rasusmilch/PT100_Mesh_Datalogger/documents/adafruit_products_framschem.png

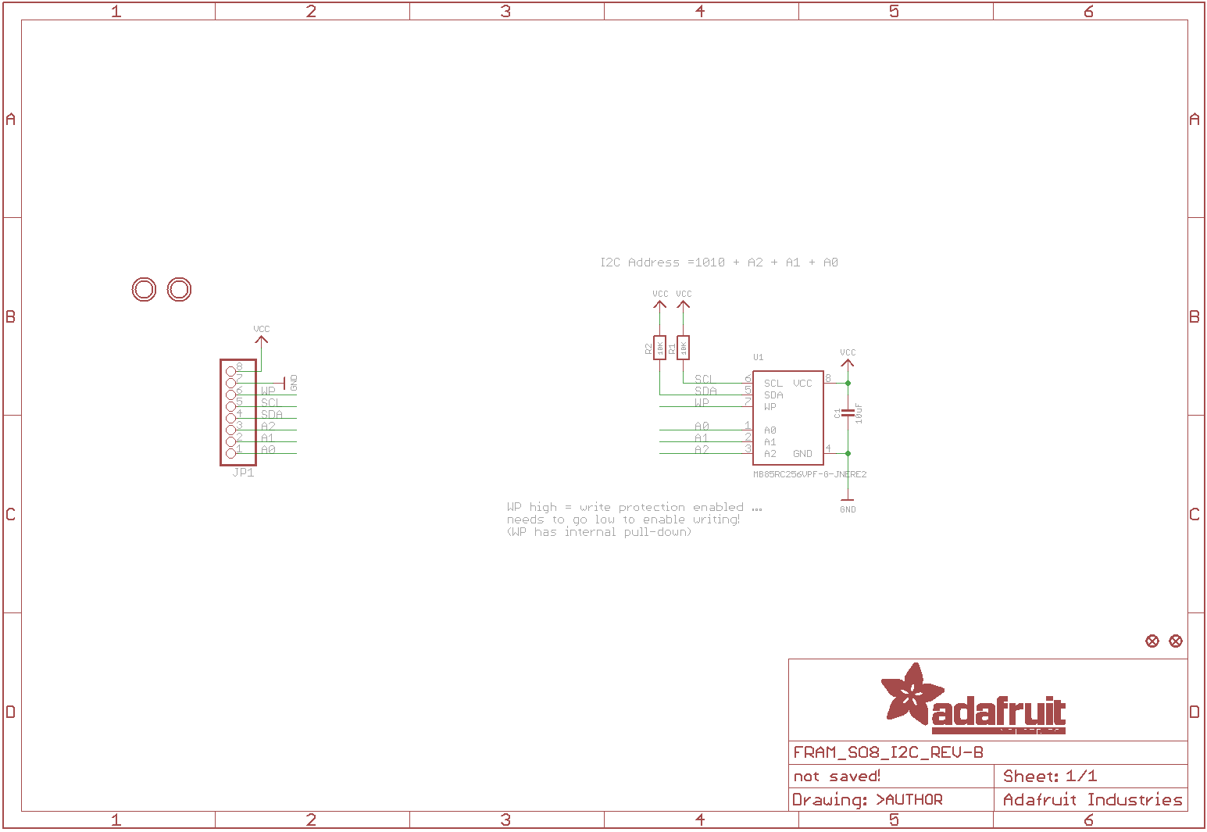
documents/adafruit_products_framschem.png
