rasusmilch/PT100_Mesh_Datalogger/documents/Figure_2.png

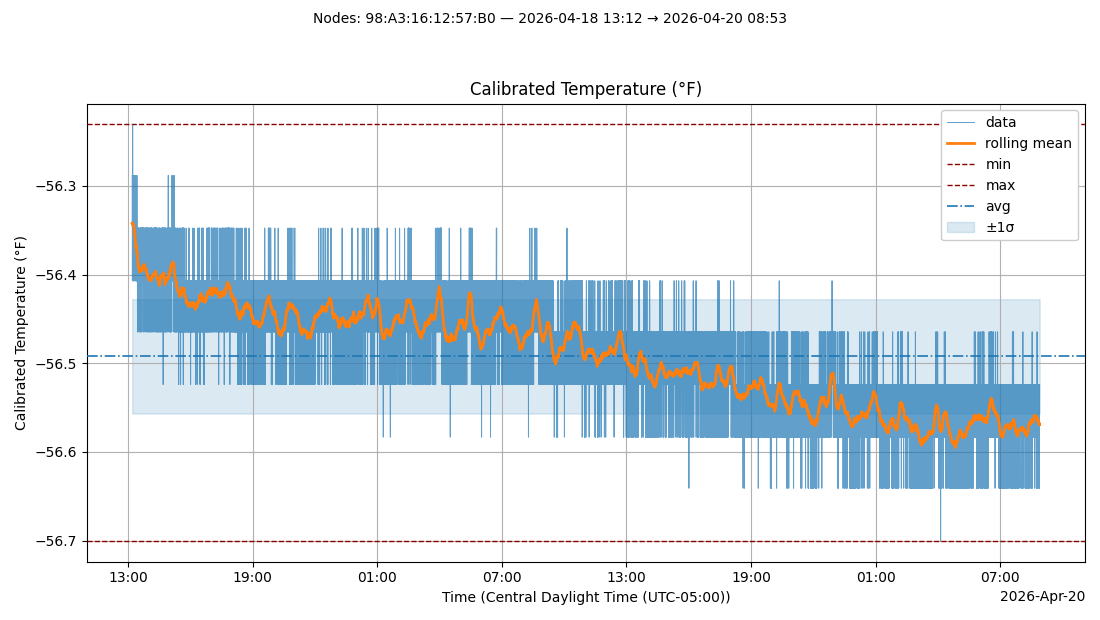
documents/Figure_2.png
