rasusmilch/PT100_Mesh_Datalogger/documents/MAX31865.png

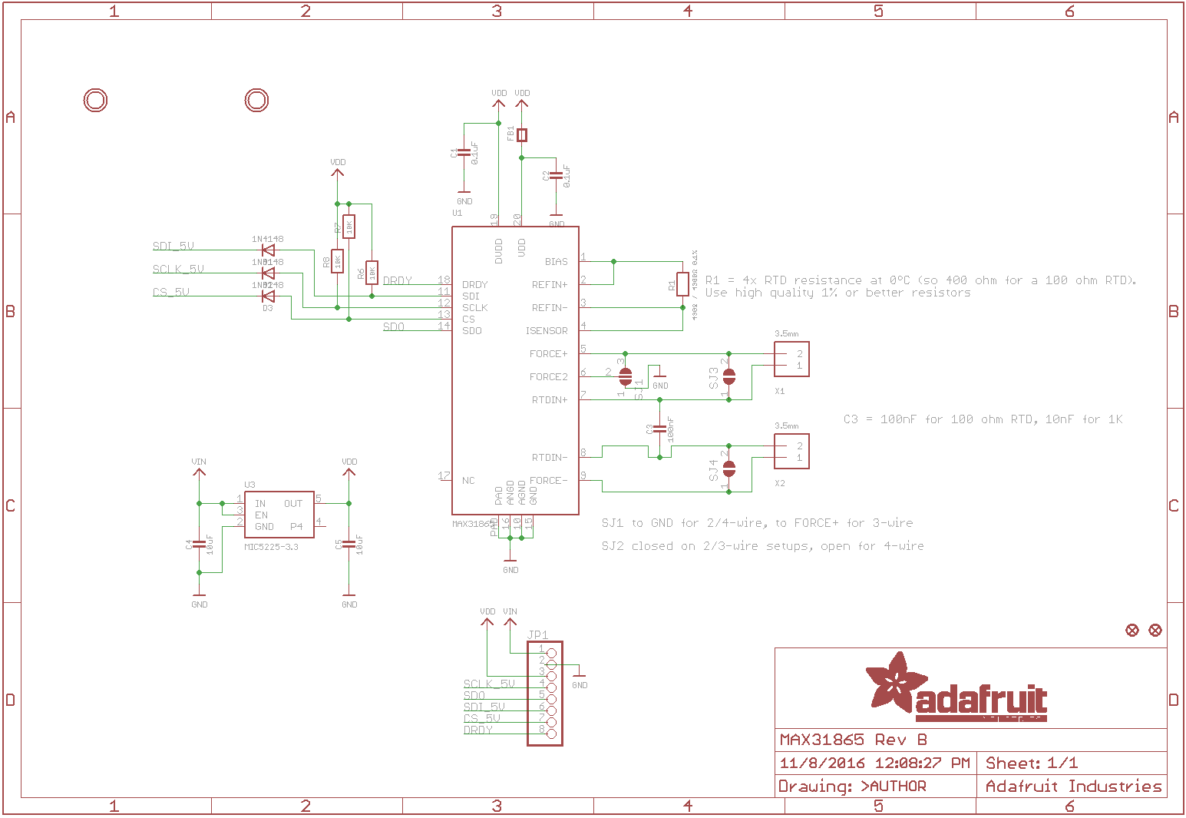
documents/MAX31865.png
