rasusmilch/PT100_Mesh_Datalogger/KiCad/PT100_Datalogger/Documentation/PT100_Datalogger_REV_A.pdf

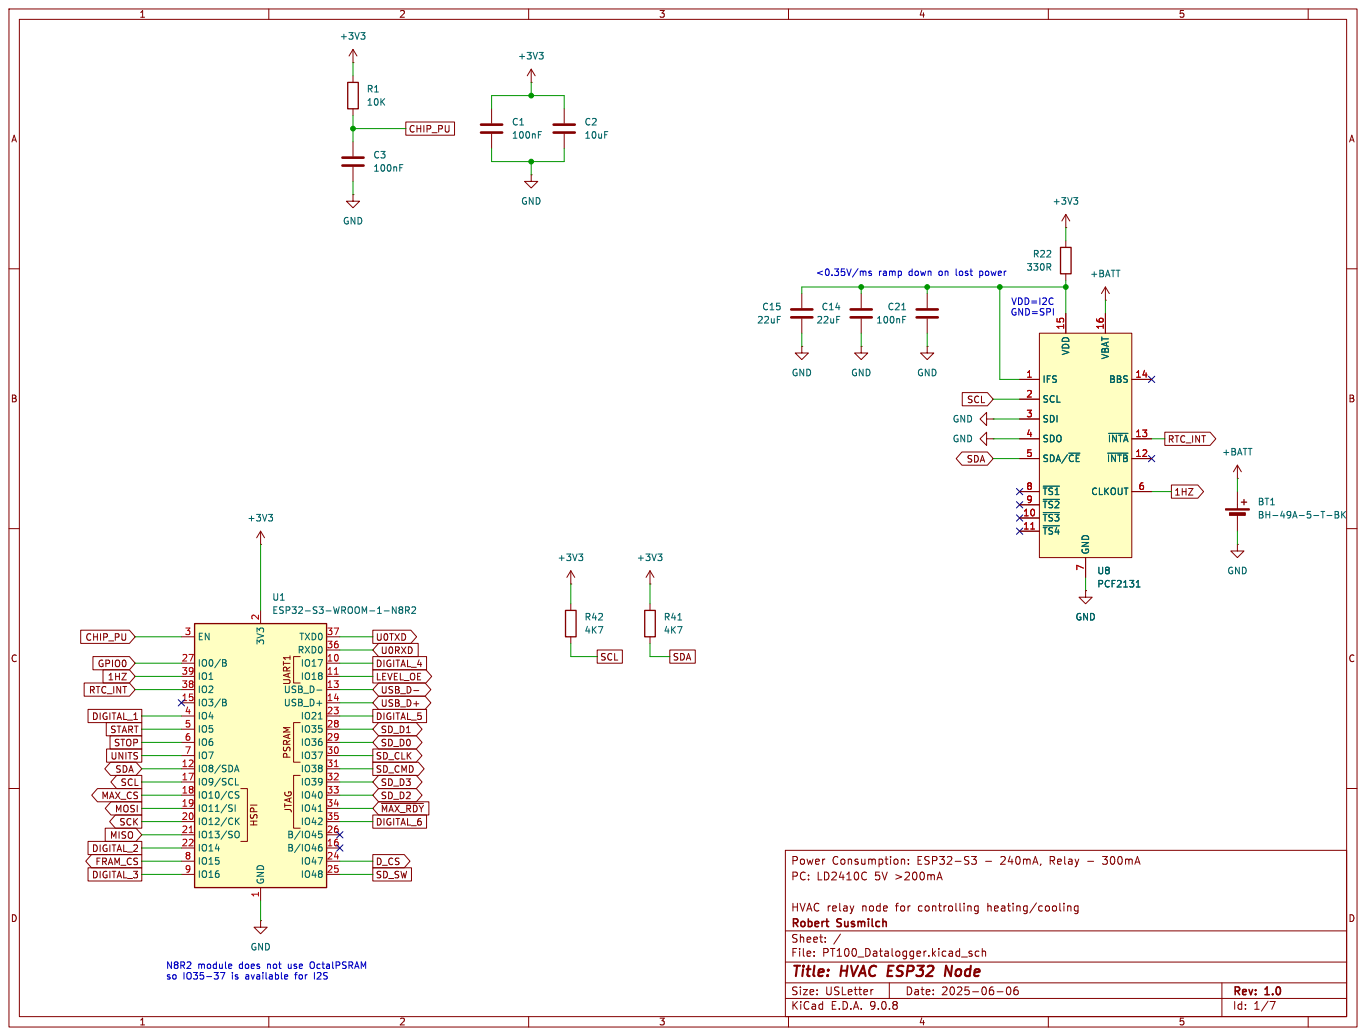
[picture p20: page 1]

7 VBAT 16 BBS 14 ~{INTA}13 ~{INTB}12 CLKOUT 6 U8PCF2131 C14

7 VBAT 16 BBS 14 ~{INTA}13 ~{INTB}12 CLKOUT 6 GND

N8R2 module does not use OctalPSRAM

Id: 1/7 Title: HVAC ESP32 Node

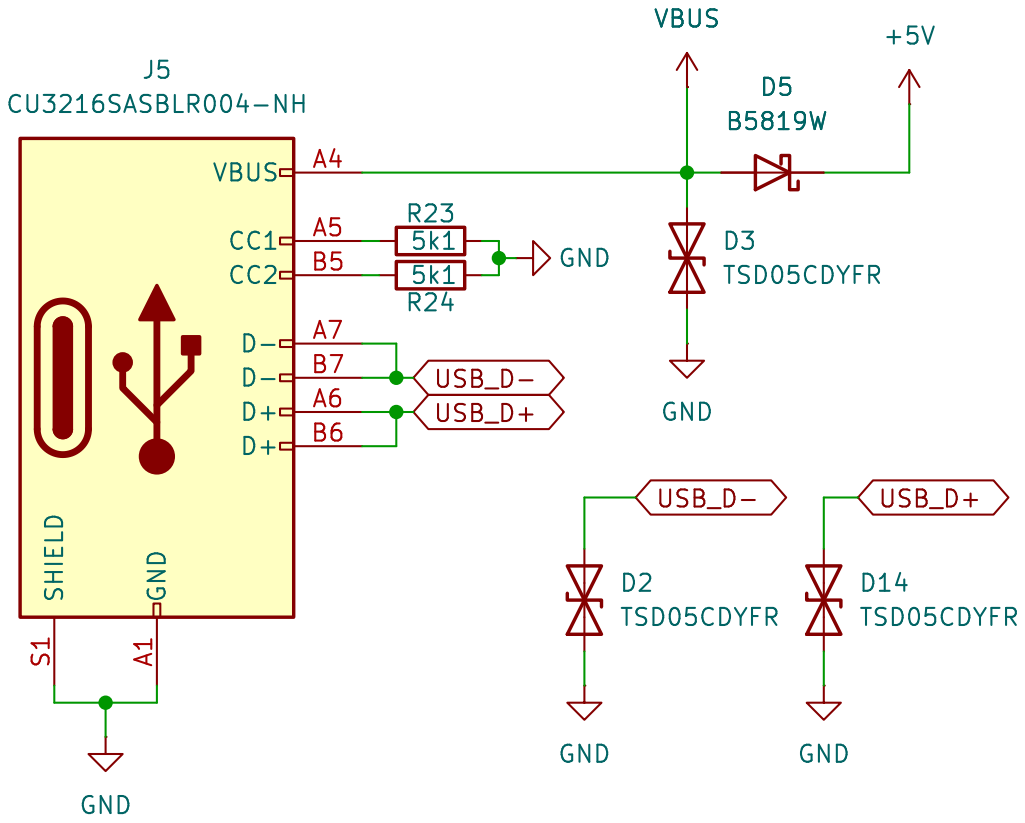
[picture p21: page 2]

Id: 2/7 Title: HVAC ESP32 Node

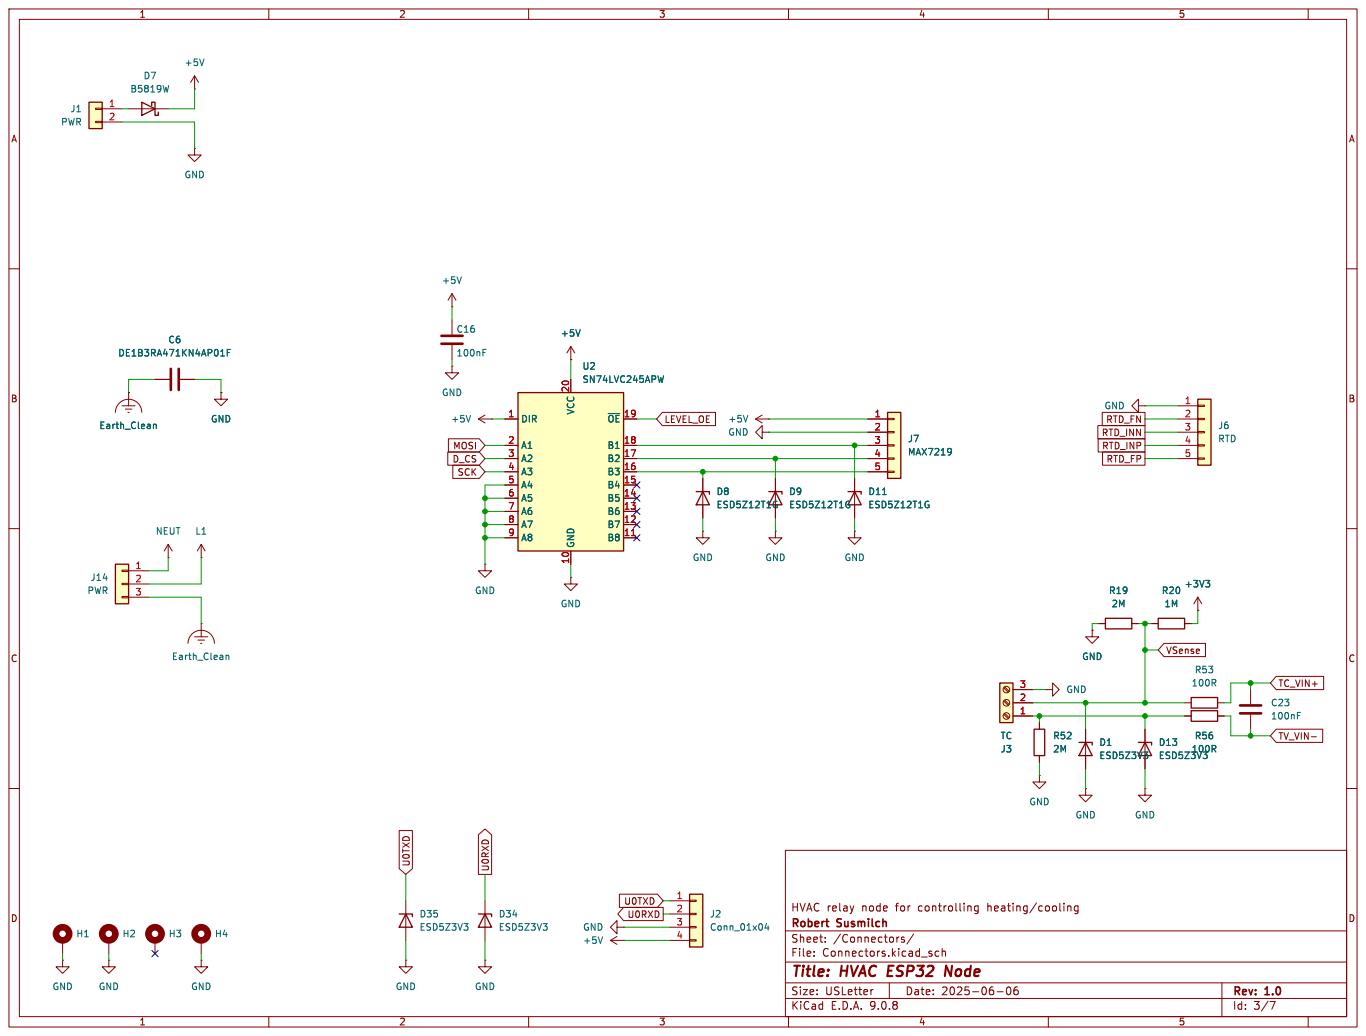
[picture p22: page 3]

Id: 3/7 Title: HVAC ESP32 Node

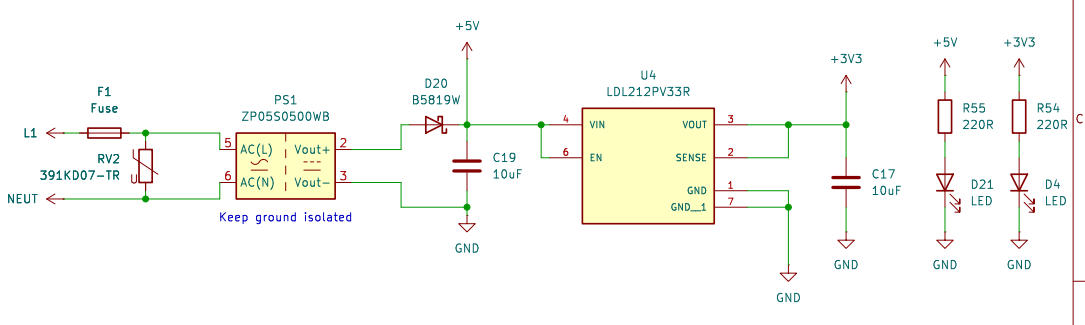
[picture p23: page 4]

Id: 5/7 Title: HVAC ESP32 Node

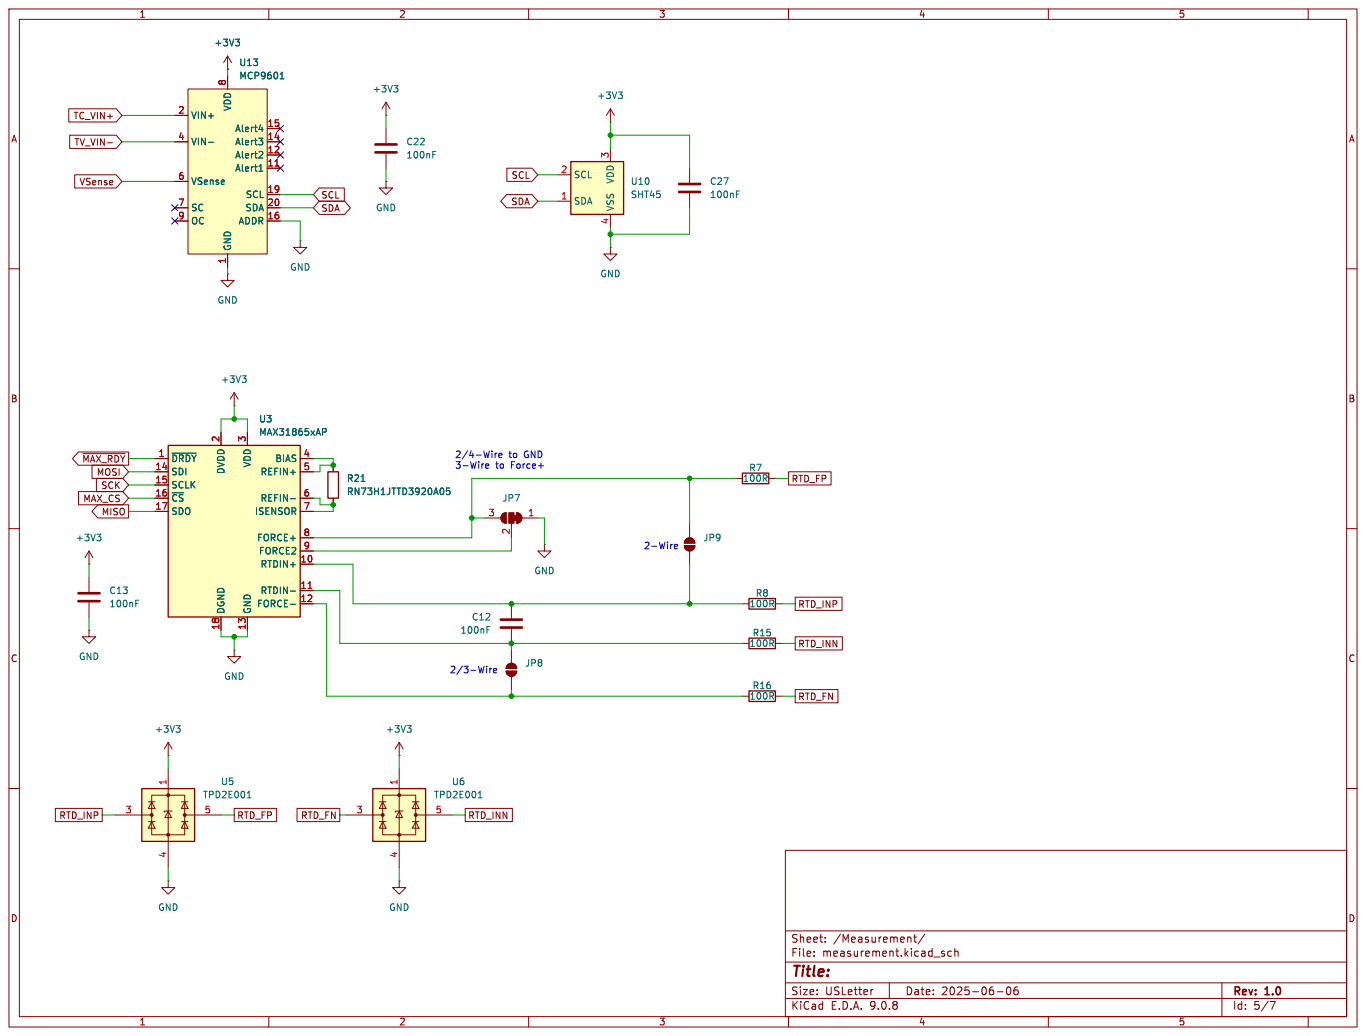
[picture p24: page 5]

3 GND 13 BIAS 4 REFIN+ 5 REFIN- 6

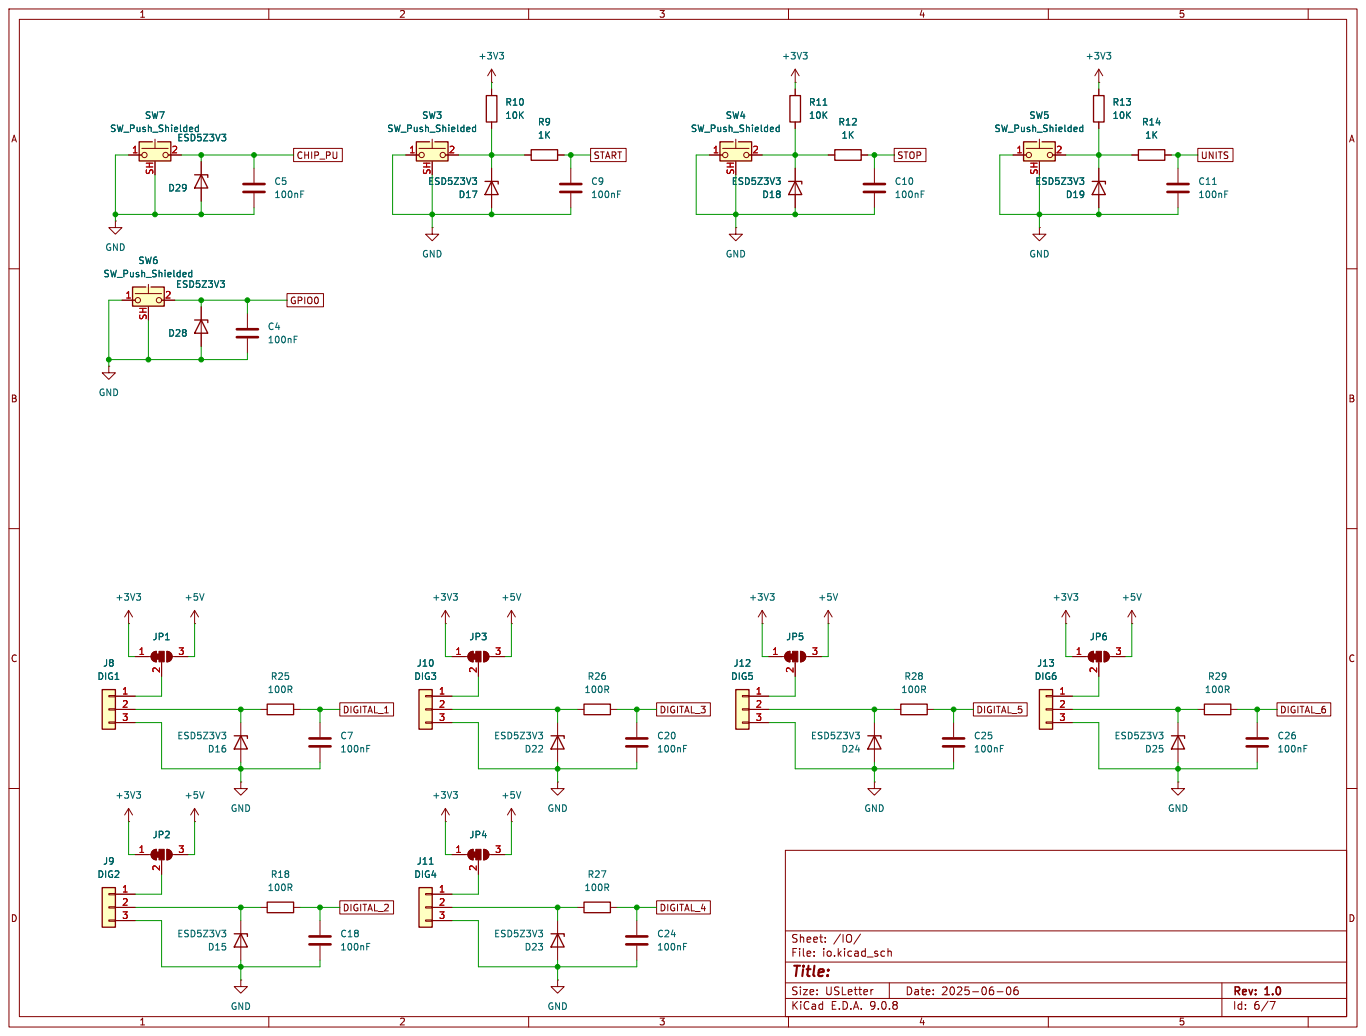
[picture p25: page 6]

Id: 6/7 Title: File: io.kicad_sch Sheet: /IO/ C24

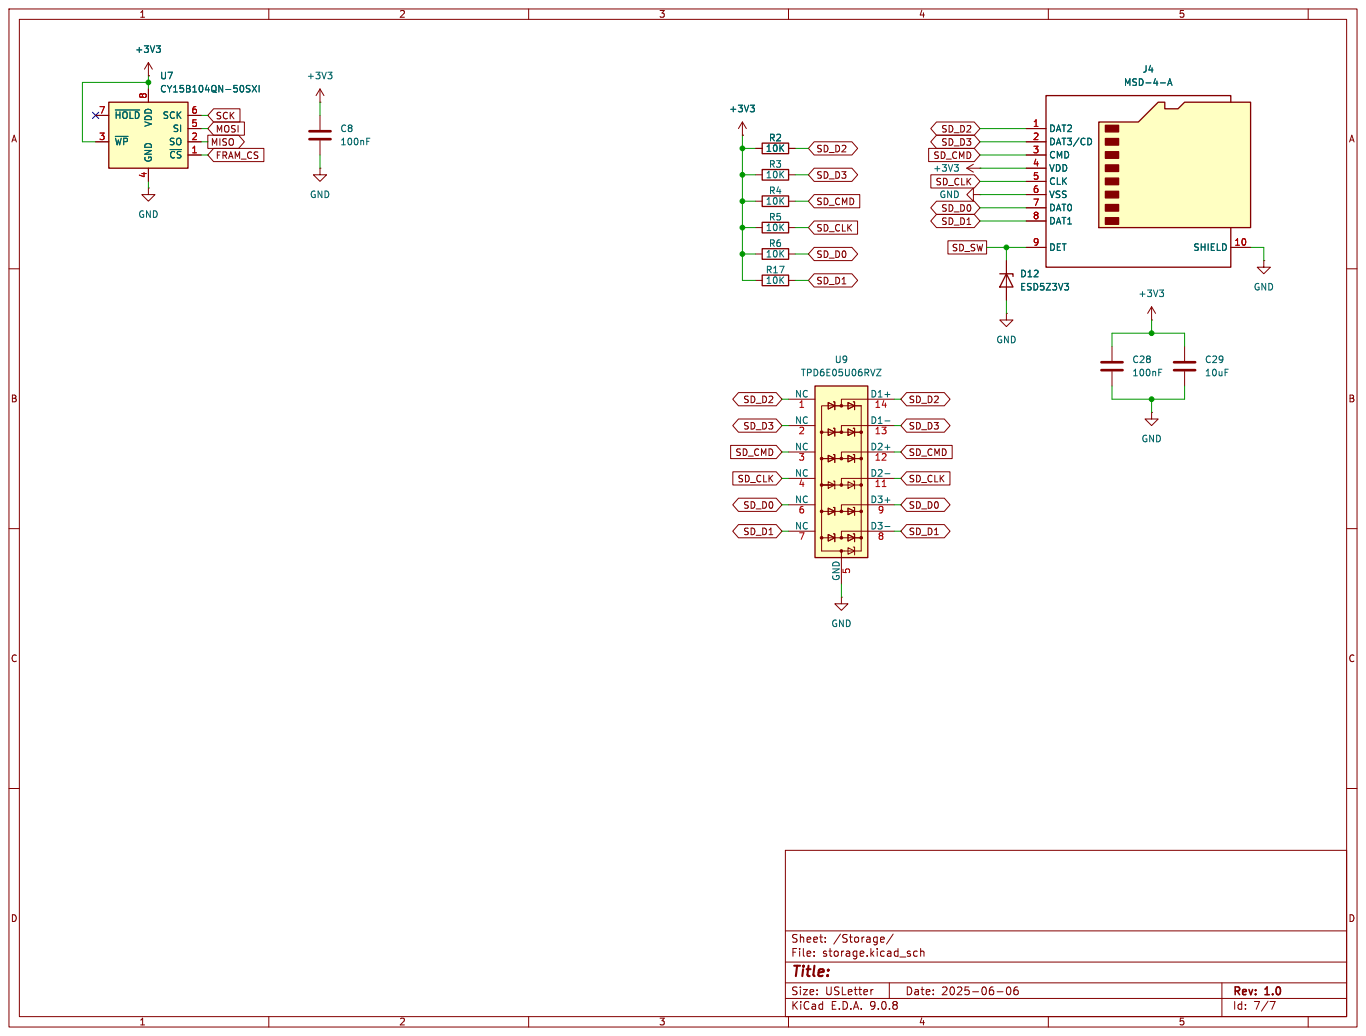
[picture p26: page 7]

4 SCK 6 SI 5 SO 2 ~{CS}1 U7 CY15B104QN-50SXI GND

4 SCK 6 SI 5 SO 2 ~{CS}1 R2

Id: 7/7 Title: File: storage.kicad_sch Sheet: /Storage/
