rasusmilch/PT100_Mesh_Datalogger/main/console_commands.c

#include "console_commands.h"

#include "freertos/FreeRTOS.h"
#include "freertos/semphr.h"
#include "freertos/task.h"

#include <ctype.h>
#include <dirent.h>
#include <errno.h>
#include <inttypes.h>
#include <limits.h>
#include <math.h>
#include <stdio.h>
#include <stdlib.h>
#include <string.h>
#include <sys/stat.h>
#include <time.h>

#include "app_net_config.h"
#include "app_settings.h"
#include "argtable3/argtable3.h"
#include "boot_mode.h"
#include "calibration.h"
#include "diagnostics/diag_fram.h"
#include "diagnostics/diag_mesh.h"
#include "diagnostics/diag_rtc.h"
#include "diagnostics/diag_rtd.h"
#include "diagnostics/diag_sd.h"
#include "diagnostics/diag_storage.h"
#include "diagnostics/diag_wifi.h"
#include "display_attention.h"
#include "driver/uart.h"
#include "driver/uart_vfs.h"
#include "esp_console.h"
#include "esp_heap_caps.h"
#include "esp_memory_utils.h"
#include "esp_netif.h"
#include "esp_timer.h"
#include "esp_wifi.h"
#include "fram_error_log.h"
#include "net_supervisor.h"
#include "runtime_health.h"
#include "time_civil.h"

#if CONFIG_ESP_CONSOLE_USB_SERIAL_JTAG
#include "driver/usb_serial_jtag.h"
#include "driver/usb_serial_jtag_vfs.h"
#include <fcntl.h>
#include <unistd.h>
#endif

#include "console_alerts.h"
#include "console_help.h"
#include "console_registry.h"
#include "esp_log.h"
#include "esp_system.h"
#include "i2c_bus.h"
#include "max31865_reader.h"
#include "mem_guard.h"
#include "runtime_manager.h"
#include "runtime_markers.h"
#include "sd_card_detect.h"
#include "sdkconfig.h"
#include "time_sync.h"
#include "units_gpio.h"
#include "wifi_credentials.h"
#include "wifi_manager.h"
#include "wifi_service.h"

static const char* kTag = "console";
static const TickType_t kConsoleFramLogLockTimeoutTicks = pdMS_TO_TICKS(2000);
static const int32_t kFlushTimeoutDefaultMs = 15000;
static const size_t kConsoleMaxCmdlineLength = 1024;
static const int kConsoleTransportRxBufferSize = 2048;
static const int kConsoleTransportTxBufferSize = 2048;
static const double kDefaultCaptureDriftLimitCPerMin = 0.020;
static char* s_console_cmdline_buffer = NULL;
static char* s_console_cmdline_snapshot = NULL;
static bool s_console_cmdline_buffer_in_psram = false;
static bool s_console_cmdline_snapshot_in_psram = false;
static void
FormatFileTime(const time_t* timestamp, char* buffer, size_t buffer_size);
static void
FormatUtcEpochIso8601(int64_t epoch_utc, char* buffer, size_t buffer_size);
static void
FormatLocalEpochIso8601(int64_t epoch_utc, char* buffer, size_t buffer_size);
static void
FormatErrlogFlags(uint16_t flags, char* buffer, size_t buffer_size);
static bool
CalConsoleOpIsActive(void);
static esp_err_t
CalConsoleOpStartLive(uint32_t every_ms,
                      int seconds,
                      int live_output_mode,
                      bool drift_notify_armed,
                      double drift_notify_threshold_c_per_min);
static esp_err_t
CalConsoleOpStartCapture(double actual_temp_c,
                         double stable_stddev_c,
                         bool drift_limit_enabled,
                         double drift_limit_c_per_min,
                         calibration_drift_limit_source_t drift_limit_source,
                         int min_seconds,
                         int timeout_seconds);
static void
CalConsoleOpRequestCancel(void);
static void
CalConsoleOpTask(void* task_arg);
static void
PrintCalWindowLine_(const char* prefix,
                    const char* timestamp_utc,
                    size_t sample_count,
                    int32_t last_raw_mC,
                    int32_t last_raw_mOhm,
                    int32_t mean_raw_mC,
                    int32_t stddev_mC,
                    double drift_c_per_min,
                    double delta_c,
                    bool drift_target_enabled,
                    const char* drift_eta_to_target_text);
static void
PrintCalWindowCalibratedLine_(const char* timestamp_utc,
                              size_t sample_count,
                              int32_t last_raw_mOhm,
                              int32_t mean_raw_mOhm,
                              int32_t stddev_mOhm,
                              double calibrated_temp_c,
                              double mean_calibrated_temp_c,
                              double stddev_calibrated_temp_c,
                              double drift_c_per_min,
                              double delta_c,
                              uint8_t fault_status);
static bool
ParseCalLiveArguments_(int argc,
                       char** argv,
                       const char* usage,
                       int* every_ms_out,
                       int* seconds_out,
                       bool* drift_notify_armed_out,
                       double* drift_notify_threshold_out);
static void
PrintCalLiveUsage_(const char* command_name);
static bool
FormatCalLiveTimestampNow_(char* buffer, size_t buffer_size);
static bool
EvaluateCalibratedTemperature_(double raw_temp_c,
                               double raw_resistance_ohm,
                               double* calibrated_temp_c_out);
static double
ConsoleResistanceToTemperatureFitCallback_(double resistance_ohm,
                                           void* context);
static void
PrintCalibrationFitLabelAndValueOrNa_(const char* label,
                                      bool available,
                                      double value);
static const char*
CalibrationFitDomainDisplayString_(calibration_domain_t fit_domain);
static const char*
CalibrationFitCorrectionLabel_(calibration_domain_t fit_domain);
static const char*
CalibrationFitCorrectionColumnHeader_(calibration_domain_t fit_domain);
static const char*
CalibrationFitDegreeLabel_(calibration_fit_mode_t fit_mode);
static void
PrintCalibrationFitValueOrNa_(const char* label,
                              bool available,
                              double value,
                              const char* unit_suffix);
static void
PrintCalibrationFitDiagnosticsBlock_(
  const calibration_fit_diagnostics_t* diagnostics);
static void
PrintCalibrationModelFitTable_(const calibration_fit_report_t* fit_report);
static void
PrintCalibrationModelFitReport_(const app_settings_t* settings);
static bool
RefreshCalibratedWindowTempStatsCache_(size_t sample_count,
                                       uint32_t window_generation,
                                       int32_t last_raw_mC,
                                       int32_t last_raw_mOhm,
                                       int32_t mean_raw_mC,
                                       int32_t mean_raw_mOhm);
static bool
CalHistoryEnsureStorage_(void);
static void
CalLogMemorySnapshot_(const char* stage, const char* mode_label);
static void
CalTrackLiveLowWatermark_(void);
static void
CalTrackLiveStackAndTempUsage_(size_t temp_bytes);
static void
CalLogLiveRetainedResources_(const char* mode_label);
/**
 * @brief Queue a one-shot cal live drift-ready ntfy message via alert queue.
 * @param drift_c_per_min Current gated drift value (C/min).
 * @param threshold_c_per_min Armed absolute drift threshold (C/min).
 * @param sustained_seconds Required sustained-under-threshold duration.
 * @return true when an ntfy job was queued successfully.
 */
static bool
QueueCalLiveDriftReadyNtfy_(double drift_c_per_min,
                            double threshold_c_per_min,
                            uint32_t sustained_seconds);
static void
PrintCalCaptureWindowLine_(double elapsed_s,
                           size_t sample_count,
                           int32_t last_raw_mC,
                           int32_t last_raw_mOhm,
                           int32_t mean_raw_mC,
                           double stddev_c,
                           double drift_c_per_min,
                           double delta_c,
                           double stable_elapsed_s,
                           int min_seconds,
                           double stable_stddev_c,
                           bool drift_limit_enabled,
                           double drift_limit_c_per_min,
                           calibration_drift_limit_source_t drift_limit_source,
                           double actual_temp_c);
static const char*
DriftLimitSourceToString_(calibration_drift_limit_source_t source);
static const char*
FindOptionValue_(int argc, char** argv, const char* name);
static bool
OptionPresent_(int argc, char** argv, const char* name);
static bool
ParseOptionInt_(int argc, char** argv, const char* name, int* value_out);
static bool
ParseOptionDouble_(int argc, char** argv, const char* name, double* value_out);
static bool
ParseTempC_(const char* text, double* value_out);
static bool
ParseCalAddPositionalArgs_(int argc,
                           char** argv,
                           double* raw_c_out,
                           double* actual_c_out);
static bool
ParseCalImportArgs_(int argc,
                    char** argv,
                    double* raw_ohm_out,
                    double* actual_c_out,
                    bool* raw_c_supplied_out,
                    double* raw_c_out,
                    bool* stddev_c_supplied_out,
                    double* stddev_c_out);
static bool
ParseCalibrationImportStatusLineSpan_(const char* line_start,
                                      size_t line_len,
                                      calibration_point_t* point_out,
                                      size_t* token_count_out);
static bool
ParseCalibrationImportStatusTokens_(int argc,
                                    char** argv,
                                    int start_index,
                                    calibration_point_t* point_out,
                                    size_t* token_count_out);
static bool
CalibrationImportPayloadFromConsoleLine_(const char* action,
                                         const char** payload_start_out,
                                         size_t* payload_len_out,
                                         bool* payload_quoted_out,
                                         bool* unterminated_quote_out);
static bool
NextCalibrationImportTokenSpan_(const char* line_start,
                                size_t line_len,
                                size_t* cursor_inout,
                                const char** token_start_out,
                                size_t* token_len_out);
static bool
ParseCalibrationImportDoubleSpan_(const char* value_start,
                                  size_t value_len,
                                  double* parsed_out);
static bool
ParseCalibrationImportDriftLimitSourceSpan_(
  const char* value_start,
  size_t value_len,
  calibration_drift_limit_source_t* source_out);
static bool
CalibrationImportKeyEquals_(const char* key_start,
                            size_t key_len,
                            const char* expected);
static int
FindCalibrationPointIndexByActualMc_(const app_settings_t* settings,
                                     int32_t actual_mC);
static esp_err_t
SaveCalibrationPointsAndDomain_(app_settings_t* settings);
static esp_err_t
DeleteCalibrationPointByDisplayIndex_(app_settings_t* settings,
                                      size_t display_index,
                                      calibration_point_t* deleted_point_out);
static bool
JoinArgsWithSpaces(int argc,
                   char** argv,
                   int start_index,
                   char* out,
                   size_t out_size);
static int
CalTopicHelp(const char* topic);
static int
SdTopicHelp(const char* topic);
static void
PrintModeHelpBody(void);
static void
PrintNetHelpBody(void);
static int
ModeTopicHelp(const char* topic);
/**
 * @brief Compute effective sensor poll period shown by console diagnostics.
 * @param settings Current settings snapshot.
 * @return Effective poll period in milliseconds.
 */
static uint32_t
ConsoleEffectiveSensorPollPeriodMs(const app_settings_t* settings);
static bool
ConsoleInputTooLongOrUnterminatedQuote_(const char* line,
                                        size_t max_cmdline_length);
static bool
ConsoleCmdlineBufferInit_(size_t max_cmdline_length);
static bool
ConsoleCmdlineSnapshotCapture_(const char* line, size_t max_cmdline_length);
static char*
ConsoleReadLine_(const char* prompt);

/**
 * @brief Print combined calibration status including window stats, points, and
 * schedule metadata.
 * @param settings Active settings snapshot.
 * @param state Runtime state for time stability / due-check flags.
 */
static void
PrintCalibrationStatusUnified(const app_settings_t* settings,
                              const runtime_state_t* state);
/**
 * @brief Print human-readable calibration equation and named coefficients.
 * @param model Active stored calibration model.
 */
static void
PrintCalibrationEquationBlock_(const calibration_model_t* model);
/**
 * @brief Print polynomial coefficients using symbolic names that map from
 * highest-order term down to constant term.
 * @param coefficients Stored polynomial coefficients in constant-first order.
 * @param degree Polynomial degree to print.
 */
static void
PrintNamedPolynomialCoefficients_(const double* coefficients, uint8_t degree);
/**
 * @brief Summary values for rendering one calibration point in status/report
 * output.
 */
typedef struct
{
  bool ideal_ref_res_available;
  bool captured_raw_res_available;
  bool captured_raw_temp_avg_available;
  bool captured_raw_temp_stddev_available;
  bool captured_raw_res_stddev_available;
  bool captured_drift_available;
  bool captured_delta_available;
  bool drift_limit_available;
  bool captured_window_available;
  bool captured_ema_alpha_available;
  bool residual_res_available;
  bool residual_temp_available;
  double ideal_ref_res_ohm;
  double captured_raw_res_avg_ohm;
  double captured_raw_temp_avg_c;
  double captured_raw_temp_stddev_c;
  double captured_raw_res_stddev_ohm;
  double captured_drift_c_per_min;
  double captured_delta_c;
  double drift_limit_c_per_min;
  double captured_ema_alpha;
  int captured_window_s;
  calibration_drift_limit_source_t drift_limit_source;
  double residual_res_ohm;
  double residual_temp_c;
} cal_point_print_summary_t;

/**
 * @brief Convert reference temperature to ideal PT100 resistance using the
 * shared CVD helper used by calibration apply.
 * @param reference_temp_c Reference temperature in Celsius.
 * @param out_ideal_ref_res_ohm Output ideal resistance in ohms.
 * @return true when conversion succeeds.
 */
static bool
ComputeIdealReferenceResistanceOhm_(double reference_temp_c,
                                    double* out_ideal_ref_res_ohm);

/**
 * @brief Build printable summary values for one calibration point.
 * @param point Calibration point.
 * @param summary_out Receives derived/availability fields for output.
 */
static void
BuildCalibrationPointPrintSummary_(const calibration_point_t* point,
                                   cal_point_print_summary_t* summary_out);

/**
 * @brief Print one concise calibration-point status line.
 * @param point Calibration point.
 * @param summary Precomputed printable summary values.
 * @param display_index 1-based display index.
 * @param point_is_resistance_domain True for captured/imported resistance
 * domain points.
 */
static void
PrintCalibrationPointStatusLine_(const calibration_point_t* point,
                                 const cal_point_print_summary_t* summary,
                                 uint32_t display_index,
                                 bool point_is_resistance_domain);

/**
 * @brief Print one report-friendly calibration-point block.
 * @param point Calibration point.
 * @param summary Precomputed printable summary values.
 * @param display_index 1-based display index.
 * @param point_is_resistance_domain True for captured/imported resistance
 * domain points.
 */
static void
PrintCalibrationPointReportBlock_(const calibration_point_t* point,
                                  const cal_point_print_summary_t* summary,
                                  uint32_t display_index,
                                  bool point_is_resistance_domain);

/**
 * @brief Force PTLOG daily file re-evaluation after calibration metadata
 * changes that affect PTLOG header content.
 * @param reason Human-readable trigger label for operator output.
 */
static void
ForcePtlogRevisionForCalibrationMetadata(const char* reason);

/**
 * @brief Print the compact calibration schedule and due status block.
 * @param settings Current settings.
 * @param state Current runtime state (may be NULL).
 */
static void
PrintCalibrationStatusBlock(const app_settings_t* settings,
                            const runtime_state_t* state);

/**
 * @brief Evaluate whether calibration is currently applied/valid for
 * reporting.
 * @param settings Current settings.
 * @param state Current runtime state (may be NULL).
 * @param reason_out Optional output reason string.
 * @return true when calibration is applied.
 */
static bool
ConsoleCalibrationIsApplied(const app_settings_t* settings,
                            const runtime_state_t* state,
                            const char** reason_out);

/**
 * @brief Parse a UTC date string in YYYY-MM-DD format into an epoch seconds
 * value.
 * @param value Input string.
 * @param epoch_out Output epoch seconds (UTC midnight).
 * @return true on success.
 */
static bool
ParseUtcDateString(const char* value, int64_t* epoch_out);

/**
 * @brief Parse calibration due unit string (days|months|years).
 * @param value Input string.
 * @param unit_out Output unit enum value.
 * @return true on success.
 */
static bool
ParseCalDueUnit(const char* value, uint8_t* unit_out);
static bool
ParseMetarAltimeterInHg(const char* token, float* altimeter_inHg_out);
static bool
MetarTokenLooksLikeObservation_(const char* token);
static bool
MetarTokenLooksLikeStation_(const char* token);
static bool
MetarTokenLooksLikeTempDew_(const char* token);
static bool
ResolveMetarObservationIsoUtc_(const char* token,
                               bool system_time_valid,
                               int64_t now_epoch_utc,
                               char* iso_out,
                               size_t iso_out_size,
                               bool* resolved_out);
static bool
ParseMetarLine_(const char* metar_line,
                calibration_metar_reference_t* metar_out,
                char* error_out,
                size_t error_out_size);
static void
PrintCalibrationMetarBlock_(const calibration_metar_reference_t* metar,
                            const char* heading,
                            bool include_report_block);
static bool
ParseElevationFt_(const char* token, uint16_t* elevation_ft_out);
static float
SaturationTempCFromStationInHg(float station_inHg);
static float
StationPressureFromSlpInHg(float slp_inHg, float elev_ft);
static void
PrintSatPtUsage(void);
/**
 * @brief Print system time in UTC and local time using current TZ/DST settings.
 * @param runtime Runtime context.
 */
static void
PrintTimeShow(const app_runtime_t* runtime);

static bool
ConsoleFramLogLock(const runtime_state_t* state)
{
  if (state == NULL || state->fram_log_mutex == NULL) {
    return false;
  }
  return xSemaphoreTake(state->fram_log_mutex,
                        kConsoleFramLogLockTimeoutTicks) == pdTRUE;
}

static void
ConsoleFramLogUnlock(const runtime_state_t* state)
{
  if (state == NULL || state->fram_log_mutex == NULL) {
    return;
  }
  (void)xSemaphoreGive(state->fram_log_mutex);
}
/**
 * @brief Execute MaybePushCalRawSampleFromSensor.
 */
typedef struct
{
  bool read_ok;
  bool sample_valid_for_window;
  bool sample_skipped_duplicate;
  bool sample_skipped_invalid_or_fault;
  uint8_t fault_status;
} cal_live_sensor_status_t;
static uint32_t g_cal_runtime_last_sample_id = 0u;

static cal_live_sensor_status_t
MaybePushCalRawSampleFromSensorWithStatus_(void)
{
  cal_live_sensor_status_t status = { 0 };

  const app_runtime_t* runtime = RuntimeGetRuntime();
  if (runtime == NULL || runtime->sensor == NULL) {
    return status;
  }

  if (RuntimeIsRunning()) {
    runtime_sensor_sample_t runtime_sample = { 0 };
    if (!RuntimeCopyLatestSensorSample(&runtime_sample)) {
      return status;
    }
    status.read_ok = true;
    status.fault_status = (uint8_t)runtime_sample.fault;
    if (runtime_sample.sample_id == g_cal_runtime_last_sample_id) {
      status.sample_skipped_duplicate = true;
      ESP_LOGD(kTag,
               "cal sample duplicate skipped: sample_id=%" PRIu32,
               runtime_sample.sample_id);
      return status;
    }
    g_cal_runtime_last_sample_id = runtime_sample.sample_id;

    if (!runtime_sample.valid || runtime_sample.fault != 0u) {
      status.sample_skipped_invalid_or_fault = true;
      ESP_LOGD(kTag,
               "cal sample skipped: sample_id=%" PRIu32
               " valid=%u fault=0x%02X",
               runtime_sample.sample_id,
               runtime_sample.valid ? 1u : 0u,
               (unsigned)runtime_sample.fault);
      return status;
    }

    // Calibration window is single-writer (console ops only).
    // Runtime produces sensor samples but MUST NOT write to the window.
    // Console consumes runtime samples via snapshot + sample_id tracking.
    CalWindowPushRawSample(runtime_sample.temp_mC, runtime_sample.ohm_mohm);
    status.sample_valid_for_window = true;
    ESP_LOGD(kTag,
             "cal sample consumed: sample_id=%" PRIu32,
             runtime_sample.sample_id);
    return status;
  }

  max31865_sample_t sample = { 0 };
  esp_err_t read_result = Max31865ReadOnce(runtime->sensor, &sample);
  if (read_result != ESP_OK) {
    return status;
  }

  status.read_ok = true;
  status.fault_status = sample.fault_status;
  if (sample.fault_present) {
    return status;
  }

  // Run mode can remain active while a console calibration operation is in
  // progress; however, this console path remains the sole writer to the
  // calibration window. Runtime/background/display/logging flows must not push
  // samples into this window.
  int32_t raw_milli_c = (int32_t)llround(sample.temperature_c * 1000.0);
  int32_t raw_milli_ohm = (int32_t)llround(sample.resistance_ohm * 1000.0);
  CalWindowPushRawSample(raw_milli_c, raw_milli_ohm);
  status.sample_valid_for_window = true;
  return status;
}

typedef enum
{
  CAL_CONSOLE_OP_NONE = 0,
  CAL_CONSOLE_OP_LIVE,
  CAL_CONSOLE_OP_CAPTURE
} cal_console_op_mode_t;

typedef enum
{
  CAL_CONSOLE_LIVE_OUTPUT_RAW = 0,
  CAL_CONSOLE_LIVE_OUTPUT_CALIBRATED
} cal_console_live_output_mode_t;

typedef struct
{
  cal_console_op_mode_t mode;
  TaskHandle_t task_handle;
  volatile bool cancel_requested;
  uint32_t print_every_ms;
  int live_seconds;
  double capture_actual_temp_c;
  double capture_stable_stddev_c;
  bool capture_drift_limit_enabled;
  double capture_drift_limit_c_per_min;
  calibration_drift_limit_source_t capture_drift_limit_source;
  int capture_min_seconds;
  int capture_timeout_seconds;
  bool capture_armed;
  int64_t capture_armed_start_us;
  bool live_drift_notify_armed;
  double live_drift_notify_threshold_c_per_min;
  cal_console_live_output_mode_t live_output_mode;
  int64_t live_drift_under_start_us;
  bool live_drift_notify_sent;
  int64_t start_us;
  size_t last_sample_count;
  uint32_t start_internal_free;
  uint32_t start_internal_largest;
  uint32_t start_psram_free;
  uint32_t start_psram_largest;
  uint32_t low_internal_free;
  uint32_t low_internal_largest;
  uint32_t min_stack_free_bytes;
  uint32_t max_temp_buffer_bytes;
} cal_console_op_state_t;

static const uint32_t kCalOpTaskStackBytes = 6144u;
static const uint32_t kCalDriftReadyBodyMaxBytes = 160u;

static cal_console_op_state_t g_cal_console_op = { 0 };
static SemaphoreHandle_t g_cal_console_op_mutex = NULL;

static app_runtime_t* g_runtime = NULL;
static app_boot_mode_t g_boot_mode = APP_BOOT_MODE_DIAGNOSTICS;

/**
 * @brief Execute BootModeToString.
 * @param mode Parameter mode.
 * @return Return the function result.
 */
static const char*
BootModeToString(app_boot_mode_t mode)
{
  return (mode == APP_BOOT_MODE_RUN) ? "run" : "diagnostics";
}

/**
 * @brief Execute DisplayAttentionItemToName.
 * @param item Parameter item.
 * @return Return the function result.
 */
static const char*
DisplayAttentionItemToName(display_attention_item_t item)
{
  switch (item) {
    case kDispAttnItemSdOut:
      return "sdout";
    case kDispAttnItemSdIo:
      return "sdio";
    case kDispAttnItemFramOvr:
      return "framovr";
    case kDispAttnItemRtdFault:
      return "rtd";
    case kDispAttnItemTimeBad:
      return "time";
    case kDispAttnItemNtpFail:
      return "ntp";
    case kDispAttnItemMeshDown:
      return "mesh";
    case kDispAttnItemHeap:
      return "heap";
    case kDispAttnItemSdSpace:
      return "sdspace";
    default:
      return "unknown";
  }
}

static void
NotifyNetSupervisor(void)
{
  NetSupervisorNotifyUpdate();
}

static void
FormatPermille(uint16_t permille, char* buffer, size_t buffer_size)
{
  if (buffer == NULL || buffer_size == 0) {
    return;
  }
  const unsigned int whole = permille / 1000u;
  const unsigned int frac = permille % 1000u;
  snprintf(buffer, buffer_size, "%u.%03u", whole, frac);
}

static void
PrintRtdEmaSettings(const app_settings_t* settings,
                    const max31865_reader_t* reader)
{
  if (settings == NULL) {
    return;
  }
  char alpha_buffer[8] = { 0 };
  FormatPermille(
    settings->rtd_ema_alpha_permille, alpha_buffer, sizeof(alpha_buffer));
  printf("rtd_ema_enabled: %s\n", settings->rtd_ema_enabled ? "yes" : "no");
  printf("rtd_ema_alpha: %s\n", alpha_buffer);
  if (reader != NULL) {
    printf("rtd_ema_valid: %s\n", reader->ema_valid ? "yes" : "no");
  }
}

static void
PrintRtdFaultSettings(const app_settings_t* settings,
                      const runtime_state_t* state)
{
  if (settings == NULL) {
    return;
  }
  printf("rtd_fault_assert_ms: %u\n", (unsigned)settings->rtd_fault_assert_ms);
  printf("rtd_fault_clear_ms: %u\n", (unsigned)settings->rtd_fault_clear_ms);
  if (state != NULL) {
    char fault_desc[128] = { 0 };
    Max31865FormatFault(
      state->rtd_fault_last_status, fault_desc, sizeof(fault_desc));
    printf("rtd_fault_debounced: %s\n",
           state->last_sensor_fault_present ? "yes" : "no");
    printf("rtd_fault_last_status: 0x%02X\n", state->rtd_fault_last_status);
    printf("rtd_fault_last_desc: %s\n", fault_desc);
    printf("rtd_fault_suppressed_count: %u\n",
           (unsigned)state->rtd_fault_suppressed_count);
    printf("rtd_fault_first_read_count: %u\n",
           (unsigned)state->rtd_fault_first_read_count);
    printf("rtd_fault_retry_fault_count: %u\n",
           (unsigned)state->rtd_fault_retry_fault_count);
    printf("rtd_fault_retry_clean_count: %u\n",
           (unsigned)state->rtd_fault_retry_clean_count);
    printf("rtd_fault_last_first_status: 0x%02X\n",
           state->rtd_fault_last_first_status);
    printf("rtd_fault_last_retry_status: 0x%02X\n",
           state->rtd_fault_last_retry_status);
    printf("rtd_fault_last_retry_err: %s\n",
           esp_err_to_name(state->rtd_fault_last_retry_err));
    printf("rtd_fault_ntfy_pending_first_read_count: %u\n",
           (unsigned)state->rtd_fault_ntfy_pending_first_read_count);
    printf("rtd_fault_ntfy_pending_retry_fault_count: %u\n",
           (unsigned)state->rtd_fault_ntfy_pending_retry_fault_count);
    printf("rtd_fault_ntfy_pending_retry_clean_count: %u\n",
           (unsigned)state->rtd_fault_ntfy_pending_retry_clean_count);
    printf("rtd_fault_ntfy_suppressed_count: %u\n",
           (unsigned)state->rtd_fault_ntfy_suppressed_count);
    printf("rtd_read_err_last: %s\n",
           esp_err_to_name(state->max31865_last_read_err));
    printf("rtd_read_err_count: %u\n",
           (unsigned)state->max31865_read_err_count);
    printf("rtd_invalid_state_count: %u\n",
           (unsigned)state->max31865_invalid_state_count);
  }
}

/**
 * @brief Execute ParseDisplayAttentionName.
 * @param value Parameter value.
 * @param item_out Parameter item_out.
 * @return Return the function result.
 */
static bool
ParseDisplayAttentionName(const char* value, display_attention_item_t* item_out)
{
  if (value == NULL || item_out == NULL) {
    return false;
  }
  if (strcasecmp(value, "sdout") == 0) {
    *item_out = kDispAttnItemSdOut;
    return true;
  }
  if (strcasecmp(value, "sdio") == 0) {
    *item_out = kDispAttnItemSdIo;
    return true;
  }
  if (strcasecmp(value, "framovr") == 0) {
    *item_out = kDispAttnItemFramOvr;
    return true;
  }
  if (strcasecmp(value, "rtd") == 0) {
    *item_out = kDispAttnItemRtdFault;
    return true;
  }
  if (strcasecmp(value, "time") == 0) {
    *item_out = kDispAttnItemTimeBad;
    return true;
  }
  if (strcasecmp(value, "ntp") == 0) {
    *item_out = kDispAttnItemNtpFail;
    return true;
  }
  if (strcasecmp(value, "mesh") == 0) {
    *item_out = kDispAttnItemMeshDown;
    return true;
  }
  if (strcasecmp(value, "heap") == 0) {
    *item_out = kDispAttnItemHeap;
    return true;
  }
  if (strcasecmp(value, "sdspace") == 0) {
    *item_out = kDispAttnItemSdSpace;
    return true;
  }
  return false;
}

/**
 * @brief Execute WifiServiceModeToString.
 * @param mode Parameter mode.
 * @return Return the function result.
 */
static const char*
WifiServiceModeToString(wifi_service_mode_t mode)
{
  switch (mode) {
    case WIFI_SERVICE_MODE_NONE:
      return "none";
    case WIFI_SERVICE_MODE_DIAGNOSTIC_STA:
      return "diagnostic_sta";
    case WIFI_SERVICE_MODE_MESH:
      return "mesh";
    default:
      return "unknown";
  }
}

/**
 * @brief Execute WifiAuthModeToString.
 * @param mode Parameter mode.
 * @return Return the function result.
 */
static const char*
WifiAuthModeToString(wifi_auth_mode_t mode)
{
  switch (mode) {
    case WIFI_AUTH_OPEN:
      return "open";
    case WIFI_AUTH_WEP:
      return "wep";
    case WIFI_AUTH_WPA_PSK:
      return "wpa_psk";
    case WIFI_AUTH_WPA2_PSK:
      return "wpa2_psk";
    case WIFI_AUTH_WPA_WPA2_PSK:
      return "wpa_wpa2";
    case WIFI_AUTH_WPA2_ENTERPRISE:
      return "wpa2_ent";
    case WIFI_AUTH_WPA3_PSK:
      return "wpa3_psk";
    case WIFI_AUTH_WPA2_WPA3_PSK:
      return "wpa2_wpa3";
    case WIFI_AUTH_WAPI_PSK:
      return "wapi_psk";
    default:
      return "unknown";
  }
}

/**
 * @brief Execute WifiDisconnectReasonToString.
 * @param reason Parameter reason.
 * @return Return the function result.
 */
static const char*
WifiDisconnectReasonToString(wifi_err_reason_t reason)
{
  switch (reason) {
    case WIFI_REASON_AUTH_EXPIRE:
      return "auth_expire";
    case WIFI_REASON_AUTH_LEAVE:
      return "auth_leave";
    case WIFI_REASON_ASSOC_EXPIRE:
      return "assoc_expire";
    case WIFI_REASON_ASSOC_TOOMANY:
      return "assoc_toomany";
    case WIFI_REASON_NOT_AUTHED:
      return "not_authed";
    case WIFI_REASON_NOT_ASSOCED:
      return "not_assoc";
    case WIFI_REASON_ASSOC_LEAVE:
      return "assoc_leave";
    case WIFI_REASON_ASSOC_NOT_AUTHED:
      return "assoc_not_authed";
    case WIFI_REASON_DISASSOC_PWRCAP_BAD:
      return "disassoc_pwrcap";
    case WIFI_REASON_DISASSOC_SUPCHAN_BAD:
      return "disassoc_supchan";
    case WIFI_REASON_IE_INVALID:
      return "ie_invalid";
    case WIFI_REASON_MIC_FAILURE:
      return "mic_failure";
    case WIFI_REASON_4WAY_HANDSHAKE_TIMEOUT:
      return "4way_timeout";
    case WIFI_REASON_GROUP_KEY_UPDATE_TIMEOUT:
      return "gk_timeout";
    case WIFI_REASON_IE_IN_4WAY_DIFFERS:
      return "ie_4way_diff";
    case WIFI_REASON_GROUP_CIPHER_INVALID:
      return "group_cipher";
    case WIFI_REASON_PAIRWISE_CIPHER_INVALID:
      return "pairwise_cipher";
    case WIFI_REASON_AKMP_INVALID:
      return "akmp_invalid";
    case WIFI_REASON_UNSUPP_RSN_IE_VERSION:
      return "rsn_ver";
    case WIFI_REASON_INVALID_RSN_IE_CAP:
      return "rsn_cap";
    case WIFI_REASON_802_1X_AUTH_FAILED:
      return "8021x_failed";
    case WIFI_REASON_BEACON_TIMEOUT:
      return "beacon_timeout";
    case WIFI_REASON_AUTH_FAIL:
      return "auth_fail";
    case WIFI_REASON_NO_AP_FOUND:
      return "no_ap";
    case WIFI_REASON_CONNECTION_FAIL:
      return "conn_fail";
    case WIFI_REASON_ASSOC_FAIL:
      return "assoc_fail";
    case WIFI_REASON_HANDSHAKE_TIMEOUT:
      return "handshake_timeout";
    default:
      return "unknown";
  }
}

/**
 * @brief Execute PrintWifiUsage.
 */
static void
PrintWifiUsage(void)
{
  printf(
    "usage:\n"
    "  wifi help\n"
    "  wifi show\n"
    "  wifi set <ssid> [password]\n"
    "  wifi clear\n"
    "  wifi scan [--max N]\n"
    "  wifi status\n"
    "  wifi connect [--timeout_ms T]\n"
    "  wifi disconnect\n"
    "  wifi cfg show\n"
    "  wifi cfg defaults\n"
    "  wifi cfg set sntp <primary[, secondary[, tertiary]]>\n"
    "  wifi cfg set sntp_fail_n <1..20>\n"
    "  wifi cfg set mesh_chan <1..13>\n"
    "  wifi cfg set mesh_id <XX:XX:XX:XX:XX:XX>\n"
    "  wifi cfg set mesh_ap_pass <password>\n"
    "  wifi cfg set no_router 0|1\n"
    "  wifi cfg set time_sync_s <seconds>\n"
    "  wifi ntp status\n"
    "  wifi ntp sync [--server host] [--timeout_ms T] [--update-rtc 0|1]\n"
    "\n"
    "notes:\n"
    "  - wifi cfg set ... writes to NVS and persists across reboot.\n"
    "  - wifi cfg defaults clears NVS overrides (revert to Kconfig defaults).\n"
    "  - Changes are applied by the network supervisor when possible.\n"
    "  - time_sync_s is clamped to 5..3600 seconds.\n"
    "  - wifi ntp sync performs a one-off sync; it does not change NVS\n"
    "    unless you also use wifi cfg set sntp/time_sync_s.\n"
    "  - sntp CSV allows optional spaces after commas; whitespace is "
    "stripped.\n");
}

// In diagnostics/console mode, Wi-Fi may not be initialized yet. Most Wi-Fi
// manager operations (scan/connect/disconnect) require the Wi-Fi service to be
// acquired so the netif/event loop/Wi-Fi driver are ready.
//
// This helper acquires the diagnostic STA mode if Wi-Fi is currently idle.
// If the system is running Wi-Fi for another mode (e.g., mesh), we refuse to
// mutate it from the console.
static esp_err_t
AcquireWifiForConsole(bool* did_acquire)
{
  if (did_acquire != NULL) {
    *did_acquire = false;
  }

  (void)WifiServiceInitOnce();

  const wifi_service_mode_t active_mode = WifiServiceActiveMode();
  if (active_mode != WIFI_SERVICE_MODE_NONE &&
      active_mode != WIFI_SERVICE_MODE_DIAGNOSTIC_STA) {
    return ESP_ERR_INVALID_STATE;
  }

  const esp_err_t result = WifiServiceAcquire(WIFI_SERVICE_MODE_DIAGNOSTIC_STA);
  if (result == ESP_OK && did_acquire != NULL) {
    *did_acquire = true;
  }
  return result;
}

static void
ReleaseWifiForConsoleIfNeeded(bool did_acquire)
{
  if (did_acquire) {
    (void)WifiServiceRelease();
  }
}

/**
 * @brief Execute PrintWifiConfig.
 */
static void
PrintWifiConfig(void)
{
  const uint8_t mesh_channel = AppNetConfigGetMeshChannel();
  const char* mesh_id = AppNetConfigGetMeshIdString();
  const bool mesh_id_valid = (mesh_id != NULL && mesh_id[0] != '\0');
  const char* ap_password = AppNetConfigGetMeshApPassword();
  const size_t ap_password_len = strlen(ap_password);
  const char* sntp_server_csv = AppNetConfigGetSntpServersCsv();
  const uint8_t sntp_server_count = AppNetConfigGetSntpServerCount();
  const char* sntp_primary = AppNetConfigGetSntpServerAt(0);
  const char* sntp_secondary = AppNetConfigGetSntpServerAt(1);
  const char* sntp_tertiary = AppNetConfigGetSntpServerAt(2);

  printf("mesh_channel: %u\n", (unsigned)mesh_channel);
  printf("mesh_channel_source: %s\n",
         AppNetConfigMeshChannelIsOverridden() ? "nvs" : "kconfig");
  printf("mesh_id: %s\n", mesh_id_valid ? mesh_id : "<invalid>");
  printf("mesh_id_source: %s\n",
         AppNetConfigMeshIdIsOverridden() ? "nvs" : "kconfig");
  if (ap_password_len == 0) {
    printf("mesh_ap_password: <empty>\n");
  } else {
    printf("mesh_ap_password: <redacted>\n");
  }
  printf("mesh_ap_password_len: %u\n", (unsigned)ap_password_len);
  printf("mesh_ap_password_source: %s\n",
         AppNetConfigMeshApPasswordIsOverridden() ? "nvs" : "kconfig");
  printf("mesh_no_router: %u\n", AppNetConfigGetMeshDisableRouter() ? 1u : 0u);
  printf("mesh_no_router_source: %s\n",
         AppNetConfigMeshDisableRouterIsOverridden() ? "nvs" : "kconfig");

  printf("sntp_servers_csv: %s\n",
         (sntp_server_csv[0] != '\0') ? sntp_server_csv : "<empty>");
  printf("sntp_server_count: %u\n", (unsigned)sntp_server_count);
  printf("sntp_primary: %s\n",
         (sntp_primary[0] != '\0') ? sntp_primary : "<empty>");
  printf("sntp_secondary: %s\n",
         (sntp_secondary[0] != '\0') ? sntp_secondary : "<empty>");
  printf("sntp_tertiary: %s\n",
         (sntp_tertiary[0] != '\0') ? sntp_tertiary : "<empty>");
  printf("sntp_server_source: %s\n",
         AppNetConfigSntpServerIsOverridden() ? "nvs" : "kconfig");
  printf("sntp_fail_n: %u\n", (unsigned)AppNetConfigGetSntpFailThresholdN());
  printf("sntp_fail_n_source: %s\n",
         AppNetConfigSntpFailThresholdIsOverridden() ? "nvs" : "kconfig");
  printf("time_sync_s: %u\n", (unsigned)AppNetConfigGetTimeSyncPeriodSeconds());
  printf("time_sync_s_source: %s\n",
         AppNetConfigTimeSyncPeriodIsOverridden() ? "nvs" : "kconfig");
}

/**
 * @brief Execute PickDefaultSntpServer.
 * @return Return the function result.
 */
static const char*
PickDefaultSntpServer(void)
{
  const char* server = AppNetConfigGetSntpServer();
  return (server[0] != '\0') ? server : "pool.ntp.org";
}

/**
 * @brief Execute PrintDisplayAttentionPolicy.
 * @param policy Parameter policy.
 */
static void
PrintDisplayAttentionPolicy(uint32_t policy)
{
  const display_attention_item_t items[] = {
    kDispAttnItemSdOut,    kDispAttnItemSdIo,    kDispAttnItemFramOvr,
    kDispAttnItemRtdFault, kDispAttnItemTimeBad, kDispAttnItemNtpFail,
    kDispAttnItemMeshDown, kDispAttnItemHeap,    kDispAttnItemSdSpace,
  };
  printf("display_attention_policy: 0x%08" PRIX32 "\n", policy);
  for (size_t idx = 0; idx < sizeof(items) / sizeof(items[0]); ++idx) {
    const display_attention_item_t item = items[idx];
    const display_attention_severity_t severity =
      DisplayAttentionPolicyGet(policy, item);
    const char* label = "off";
    if (severity == DISP_SEV_WARN) {
      label = "warn";
    } else if (severity == DISP_SEV_ERROR) {
      label = "error";
    }
    printf("  %s: %s\n", DisplayAttentionItemToName(item), label);
  }
}

/**
 * @brief Execute SaveDisplayAttentionPolicy.
 * @param policy Parameter policy.
 * @return Return the function result.
 */
static int
SaveDisplayAttentionPolicy(uint32_t policy)
{
  if (g_runtime == NULL) {
    return 1;
  }
  const esp_err_t result = AppSettingsSaveDisplayAttentionPolicy(policy);
  if (result != ESP_OK) {
    printf("save failed: %s\n", esp_err_to_name(result));
    return 1;
  }
  g_runtime->settings->display_attention_policy = policy;
  g_runtime->settings->display_attention_mask =
    AppSettingsGetDisplayAttentionMask();

  // Ensure the display task reflects policy changes immediately.
  RuntimeSetDisplayAttentionPolicy(policy);
  printf("OK\n");
  PrintDisplayAttentionPolicy(policy);
  return 0;
}

/**
 * @brief Execute ParseDisplayAttentionSeverity.
 * @param value Parameter value.
 * @param severity_out Parameter severity_out.
 * @return Return the function result.
 */
static bool
ParseDisplayAttentionSeverity(const char* value,
                              display_attention_severity_t* severity_out)
{
  if (value == NULL || severity_out == NULL) {
    return false;
  }
  if (strcasecmp(value, "off") == 0) {
    *severity_out = DISP_SEV_OFF;
    return true;
  }
  if (strcasecmp(value, "warn") == 0) {
    *severity_out = DISP_SEV_WARN;
    return true;
  }
  if (strcasecmp(value, "error") == 0) {
    *severity_out = DISP_SEV_ERROR;
    return true;
  }
  return false;
}

/**
 * @brief Execute CalibrationModeToString.
 * @param mode Parameter mode.
 * @return Return the function result.
 */
static const char*
CalibrationModeToString(calibration_fit_mode_t mode)
{
  switch (mode) {
    case CAL_FIT_MODE_LINEAR:
      return "linear";
    case CAL_FIT_MODE_PIECEWISE:
      return "piecewise";
    case CAL_FIT_MODE_POLY:
      return "poly";
    default:
      return "unknown";
  }
}

/**
 * @brief Execute SaveCalibrationWithContext.
 * @param model Parameter model.
 * @return Return the function result.
 */
static esp_err_t
SaveCalibrationWithContext(const calibration_model_t* model)
{
  if (g_runtime == NULL || g_runtime->sensor == NULL) {
    return ESP_ERR_INVALID_STATE;
  }
  calibration_context_t context;
  AppSettingsBuildCalibrationContextFromReader(&context, g_runtime->sensor);

  if (g_runtime->settings != NULL) {
    g_runtime->settings->calibration = *model;
    g_runtime->settings->calibration_context = context;
    g_runtime->settings->calibration_context_valid = true;
  }

  esp_err_t result = AppSettingsSaveCalibrationWithContext(model, &context);
  if (result != ESP_OK) {
    return result;
  }
  if (TimeSyncIsSystemTimeValid() && g_runtime->settings != NULL) {
    g_runtime->settings->cal_last_utc = (int64_t)time(NULL);
    result = AppSettingsSaveCalibrationSchedule(g_runtime->settings);
  }
  return result;
}

/**
 * @brief Compute effective sensor polling period from display and log periods.
 * @param settings Current settings snapshot.
 * @return Poll period in milliseconds clamped to [100, 3600000].
 */
static uint32_t
ConsoleEffectiveSensorPollPeriodMs(const app_settings_t* settings)
{
  uint32_t display_period_ms = 1000u;
  uint32_t log_period_ms = 1000u;

  if (settings != NULL) {
    display_period_ms = settings->display_sample_period_ms;
    log_period_ms = settings->log_period_ms;
  }

  if (display_period_ms == 0u) {
    display_period_ms = 1000u;
  }
  if (display_period_ms < 100u) {
    display_period_ms = 100u;
  } else if (display_period_ms > 3600000u) {
    display_period_ms = 3600000u;
  }

  if (log_period_ms >= 100u && log_period_ms <= 3600000u &&
      log_period_ms < display_period_ms) {
    display_period_ms = log_period_ms;
  }

  return display_period_ms;
}

/**
 * @brief Execute CommandStatus.
 * @param argc Parameter argc.
 * @param argv Parameter argv.
 * @return Return the function result.
 */
static int
CommandStatus(int argc, char** argv)
{
  (void)argc;
  (void)argv;
  if (g_runtime == NULL) {
    return 1;
  }

  const app_settings_t* settings = g_runtime->settings;
  const runtime_state_t* state = RuntimeGetState();

  printf("node_id: %s\n", g_runtime->node_id_string);
  printf("runtime_running: %s\n", RuntimeIsRunning() ? "yes" : "no");
  printf("time_valid: %s\n", TimeSyncIsSystemTimeValid() ? "yes" : "no");
  printf("log_period_ms: %u\n", (unsigned)settings->log_period_ms);
  printf("display_sample_period_ms: %u\n",
         (unsigned)settings->display_sample_period_ms);
  printf("rtc_resync_period_ms: %u\n",
         (unsigned)settings->rtc_resync_period_ms);
  printf("sd_flush_period_ms: %u\n", (unsigned)settings->sd_flush_period_ms);
  printf("sd_batch_target_bytes: %u\n",
         (unsigned)settings->sd_batch_bytes_target);
  printf("sd_verify_readback: %s\n",
         (state != NULL && state->sd_verify_readback) ? "on" : "off");
  printf("node_role: %s\n", AppSettingsRoleToString(settings->node_role));
  const app_net_mode_t effective_net_mode =
    AppSettingsGetEffectiveNetMode(settings->node_role, settings->net_mode);
  printf("configured_net_mode: %s\n",
         AppSettingsNetModeToString(settings->net_mode));
  printf("effective_net_mode: %s\n",
         AppSettingsNetModeToString(effective_net_mode));
  const char* net_override_reason = AppSettingsGetNetModeOverrideReason(
    settings->node_role, settings->net_mode);
  if (net_override_reason != NULL) {
    printf("effective_override_reason: %s\n", net_override_reason);
  }
  printf("allow_children: %s\n", settings->allow_children ? "yes" : "no");
  printf("tz_posix: %s\n", settings->tz_posix);
  printf("dst_enabled: %s\n", settings->dst_enabled ? "yes" : "no");
  printf("mqtt_enabled: %s\n", settings->mqtt_enabled ? "yes" : "no");
  printf("mqtt_broker_uri: %s\n", settings->mqtt_broker_uri);
  printf("mqtt_topic_prefix: %s\n", settings->mqtt_topic_prefix);
  printf("mqtt_qos: %u\n", (unsigned)settings->mqtt_qos);
  printf("mqtt_retain: %s\n", settings->mqtt_retain ? "yes" : "no");
  if (settings->node_role == APP_NODE_ROLE_ROOT) {
    printf("bridge_mode: %s\n",
           AppSettingsMqttBridgeModeToString(settings->mqtt_bridge_mode));
    const bool broker_bridge_active =
      settings->mqtt_enabled &&
      (settings->mqtt_bridge_mode == MQTT_BRIDGE_BROKER ||
       settings->mqtt_bridge_mode == MQTT_BRIDGE_BOTH);
    printf("broker_bridge_active: %s\n", broker_bridge_active ? "yes" : "no");
  }
  PrintRtdEmaSettings(settings, g_runtime->sensor);
  PrintRtdFaultSettings(settings, RuntimeGetState());

  // Ensure the TZ rules are loaded before formatting local time.
  // (TZ is applied via AppSettingsApplyTimeZone() at boot and by the tz/dst
  // commands.)
  tzset();

  const time_t now = time(NULL);

  struct tm utc_time;
  char utc_buffer[48] = { 0 };
  if (gmtime_r(&now, &utc_time) != NULL) {
    strftime(utc_buffer, sizeof(utc_buffer), "%Y-%m-%d %H:%M:%SZ", &utc_time);
  }
  printf("utc_time: %s (epoch=%ld)\n",
         (utc_buffer[0] != '\0') ? utc_buffer : "unknown",
         (long)now);

  struct tm local_time;
  char local_buffer[48] = { 0 };
  if (localtime_r(&now, &local_time) != NULL) {
    strftime(
      local_buffer, sizeof(local_buffer), "%Y-%m-%d %H:%M:%S", &local_time);
  }

  // Compute UTC offset in seconds (local = UTC + offset).
  // Avoid relying on non-portable tm_gmtoff.
  struct tm utc_as_local = utc_time;
  utc_as_local.tm_isdst = -1;
  const time_t utc_epoch_as_local = mktime(&utc_as_local);
  long utc_offset_sec = 0;
  if (utc_epoch_as_local != (time_t)-1) {
    utc_offset_sec = (long)difftime(now, utc_epoch_as_local);
  }

  printf("local_time: %s (utc_offset_sec=%ld dst_in_effect=%d)\n",
         (local_buffer[0] != '\0') ? local_buffer : "unknown",
         utc_offset_sec,
         local_time.tm_isdst);
  size_t fram_count = 0;
  size_t fram_capacity = 0;
  uint64_t fram_overrun_total = 0;
  uint32_t fram_buffered = 0;
  uint32_t fram_next_sequence = 0;
  const bool fram_locked = ConsoleFramLogLock(state);
  if (fram_locked) {
    fram_count = FramLogGetCountRecords(g_runtime->fram_log);
    fram_capacity = FramLogGetCapacityRecords(g_runtime->fram_log);
    fram_overrun_total = FramLogGetOverrunRecordsTotal(g_runtime->fram_log);
    fram_buffered = FramLogGetBufferedRecords(g_runtime->fram_log);
    fram_next_sequence = FramLogNextSequence(g_runtime->fram_log);
    ConsoleFramLogUnlock(state);
  } else {
    printf("fram_stats: unavailable (lock timeout)\n");
  }
  const uint32_t fram_fill_pct =
    (fram_capacity > 0) ? (uint32_t)((fram_count * 100u) / fram_capacity) : 0u;
  printf("fram_count: %zu\n", fram_count);
  printf("fram_capacity: %zu\n", fram_capacity);
  printf("fram_fill_pct: %u\n", (unsigned)fram_fill_pct);
  printf("fram_overrun_records_total: %" PRIu64 "\n", fram_overrun_total);
  printf("fram_flush_watermark_records: %u\n",
         (unsigned)settings->fram_flush_watermark_records);
  const bool fram_full =
    (g_runtime->fram_full != NULL) ? *g_runtime->fram_full : false;
  printf("fram_full: %s\n", fram_full ? "yes" : "no");
  printf("fram_count/seq: %u/%u\n",
         (unsigned)fram_buffered,
         (unsigned)fram_next_sequence);
  if (state != NULL) {
    printf("fram_corrupt_detect_count: %u\n",
           (unsigned)state->fram_corrupt_detect_count);
    printf("fram_corrupt_skip_count: %u\n",
           (unsigned)state->fram_corrupt_skip_count);
    printf("fram_corrupt_last_reason: %s\n",
           FramLogValidateResultToString(state->fram_corrupt_last_reason));
    printf("fram_corrupt_last_slot: %u\n",
           (unsigned)state->fram_corrupt_last_slot);
    printf("fram_corrupt_last_addr: 0x%04x\n",
           (unsigned)state->fram_corrupt_last_addr);
    printf("fram_corrupt_last_magic: 0x%08" PRIx32 "\n",
           state->fram_corrupt_last_magic);
    printf("fram_corrupt_last_schema: %u\n",
           (unsigned)state->fram_corrupt_last_schema);
    printf("fram_corrupt_last_exp_crc: 0x%04x\n",
           (unsigned)state->fram_corrupt_last_exp_crc);
    printf("fram_corrupt_last_act_crc: 0x%04x\n",
           (unsigned)state->fram_corrupt_last_act_crc);
  }
  const uint32_t export_dropped = (g_runtime->export_dropped_count != NULL)
                                    ? *g_runtime->export_dropped_count
                                    : 0u;
  const uint32_t export_write_fail =
    (g_runtime->export_write_fail_count != NULL)
      ? *g_runtime->export_write_fail_count
      : 0u;
  printf("data_csv_drop_count: %u\n", (unsigned)export_dropped);
  printf("data_csv_write_fail_count: %u\n", (unsigned)export_write_fail);
  printf("data_stream_enabled: %s\n",
         RuntimeIsDataStreamingEnabled() ? "yes" : "no");
  DataPortBackend data_stream_backend = RuntimeGetDataStreamBackend();
  printf("data_stream_backend: %s\n",
         DataPortBackendToString(data_stream_backend));
  if (data_stream_backend == DATA_PORT_BACKEND_UART0) {
    int32_t uart0_tx_gpio = -1;
    int32_t uart0_rx_gpio = -1;
    DataPortGetUart0Pins(&uart0_tx_gpio, &uart0_rx_gpio);
    printf("data_stream_uart0_tx_gpio: %ld\n", (long)uart0_tx_gpio);
    printf("data_stream_uart0_rx_gpio: %ld\n", (long)uart0_rx_gpio);
  }
  printf("data_stream_init_err: %s\n",
         esp_err_to_name(RuntimeGetDataStreamInitError()));
  const uint32_t export_drop_count =
    (g_runtime->export_drop_count != NULL) ? *g_runtime->export_drop_count : 0u;
  const uint32_t export_send_fail_count =
    (g_runtime->export_send_fail_count != NULL)
      ? *g_runtime->export_send_fail_count
      : 0u;
  const uint32_t broker_drop_count =
    (g_runtime->broker_drop_count != NULL) ? *g_runtime->broker_drop_count : 0u;
  const uint32_t broker_send_fail_count =
    (g_runtime->broker_send_fail_count != NULL)
      ? *g_runtime->broker_send_fail_count
      : 0u;
  const runtime_cached_status_t* cached_status = RuntimeGetCachedStatus();
  runtime_health_snapshot_t health = { 0 };
  if (state != NULL) {
    RuntimeHealthRead(&state->health_cache, &health);
  }
  const bool mqtt_connected = (g_runtime->mqtt_client_connected != NULL)
                                ? *g_runtime->mqtt_client_connected
                                : false;
  UBaseType_t export_outbox_used = 0;
  if (g_runtime->export_outbox != NULL && *g_runtime->export_outbox != NULL) {
    export_outbox_used = uxQueueMessagesWaiting(*g_runtime->export_outbox);
  }
  printf("mqtt_connected: %s\n", mqtt_connected ? "yes" : "no");
  printf("export_outbox_depth/used: %u/%u\n",
         (unsigned)CONFIG_APP_EXPORT_OUTBOX_DEPTH,
         (unsigned)export_outbox_used);
  printf("export_drop_count: %u\n", (unsigned)export_drop_count);
  printf("export_send_fail_count: %u\n", (unsigned)export_send_fail_count);
  if (settings->node_role == APP_NODE_ROLE_ROOT) {
    UBaseType_t broker_outbox_used = 0;
    if (g_runtime->broker_outbox != NULL && *g_runtime->broker_outbox != NULL) {
      broker_outbox_used = uxQueueMessagesWaiting(*g_runtime->broker_outbox);
    }
    printf("broker_outbox_depth/used: %u/%u\n",
           (unsigned)CONFIG_APP_BROKER_OUTBOX_DEPTH,
           (unsigned)broker_outbox_used);
    printf("broker_drop_count: %u\n", (unsigned)broker_drop_count);
    printf("broker_send_fail_count: %u\n", (unsigned)broker_send_fail_count);
    if (cached_status != NULL) {
      printf("root_publish_consumer_active: %s\n",
             cached_status->root_publish_consumer_active ? "yes" : "no");
      printf("root_publish_drop_no_consumer: %u\n",
             (unsigned)cached_status->root_publish_drop_no_consumer);
    }
  }

  printf("calibration: mode=%s degree=%u coeffs=[%.9g, %.9g, %.9g, %.9g]\n",
         CalibrationModeToString(settings->calibration.mode),
         (unsigned)settings->calibration.degree,
         settings->calibration.coefficients[0],
         settings->calibration.coefficients[1],
         settings->calibration.coefficients[2],
         settings->calibration.coefficients[3]);
  PrintCalibrationStatusBlock(settings, state);

  const bool sd_mounted = g_runtime->sd_logger->is_mounted;
  const bool sd_degraded = RuntimeSdIsDegraded();
  const uint32_t sd_fail_count = RuntimeSdFailCount();
  const TickType_t now_ticks = xTaskGetTickCount();
  const uint32_t sd_backoff_until = RuntimeSdBackoffUntilTicks();
  uint32_t sd_backoff_remaining_ms = 0;
  if (sd_backoff_until != 0 && now_ticks < (TickType_t)sd_backoff_until) {
    sd_backoff_remaining_ms =
      (uint32_t)pdTICKS_TO_MS((TickType_t)sd_backoff_until - now_ticks);
  }
  const char* sd_card_present = "unknown";
  const char* sd_safe_to_remove = "unknown";
  if (cached_status != NULL) {
    sd_card_present = cached_status->sd_card_present ? "yes" : "no";
    sd_safe_to_remove = cached_status->sd_safe_to_remove ? "yes" : "no";
  }
  printf("sd_mounted: %s\n", sd_mounted ? "yes" : "no");
  printf("sd_card_present: %s\n", sd_card_present);
  printf("sd_safe_to_remove: %s\n", sd_safe_to_remove);
  printf("sd_card_detect_gpio: %d\n", CONFIG_APP_SD_CARD_DETECT_GPIO);
  printf("sd_card_detect_present_level: %s\n",
#if CONFIG_APP_SD_CARD_DETECT_PRESENT_HIGH
         "high"
#else
         "low"
#endif
  );
  printf("sd_degraded: %s\n", sd_degraded ? "yes" : "no");
  if (cached_status != NULL) {
    printf("deferred_count: %u\n", (unsigned)cached_status->deferred_count);
    printf("deferred_drops: %u\n", (unsigned)cached_status->deferred_drops);
    printf("deferred_active: %s\n",
           cached_status->deferred_active ? "yes" : "no");
    printf("i2c_quiesce_active: %s\n",
           cached_status->i2c_quiesce_active ? "yes" : "no");
  }
  printf("sd_fail_count: %u\n", (unsigned)sd_fail_count);
  printf("sd_backoff_remaining_ms: %u\n", (unsigned)sd_backoff_remaining_ms);
  if (cached_status != NULL) {
    const uint64_t total = cached_status->sd_total_bytes;
    const uint64_t free = cached_status->sd_free_bytes;
    printf("sd_total_bytes: %" PRIu64 " (%" PRIu64 " MiB)\n",
           total,
           (total / (1024u * 1024u)));
    printf("sd_free_bytes: %" PRIu64 " (%" PRIu64 " MiB)\n",
           free,
           (free / (1024u * 1024u)));
    printf("sd_space_reclaim_active: %s\n",
           cached_status->sd_space_reclaim_active ? "yes" : "no");
    printf("sd_space_reclaim_deleted_total: %u\n",
           (unsigned)cached_status->sd_space_reclaim_deleted_total);
    printf("sd_out_of_space_active: %s\n",
           cached_status->sd_out_of_space_active ? "yes" : "no");
  }
  printf("sd_last_record_id: %" PRIu64 "\n",
         SdLoggerLastRecordIdOnSd(g_runtime->sd_logger));
#if CONFIG_APP_HEAP_MONITOR_ENABLE
  printf("heap_internal_free_bytes: %u\n",
         (unsigned)health.heap_internal_free_bytes);
  printf("heap_internal_largest_free_block_bytes: %u\n",
         (unsigned)health.heap_internal_largest_free_block_bytes);
  printf("heap_internal_min_free_bytes: %u\n",
         (unsigned)health.heap_internal_min_free_bytes);
  printf("heap_internal_min_largest_free_block_bytes: %u\n",
         (unsigned)health.heap_internal_min_largest_free_block_bytes);
  printf("heap_internal_frag_percent: %u\n",
         (unsigned)health.heap_internal_frag_percent);
  printf("heap_internal_warn: %s\n", health.heap_internal_warn ? "yes" : "no");
  printf("heap_internal_crit: %s\n", health.heap_internal_crit ? "yes" : "no");
#if CONFIG_APP_HEAP_PSRAM_MONITOR_ENABLE
  printf("heap_psram_free_bytes: %u\n", (unsigned)health.heap_psram_free_bytes);
  printf("heap_psram_largest_free_block_bytes: %u\n",
         (unsigned)health.heap_psram_largest_free_block_bytes);
  printf("heap_psram_min_free_bytes: %u\n",
         (unsigned)health.heap_psram_min_free_bytes);
  printf("heap_psram_min_largest_free_block_bytes: %u\n",
         (unsigned)health.heap_psram_min_largest_free_block_bytes);
  printf("heap_psram_frag_percent: %u\n",
         (unsigned)health.heap_psram_frag_percent);
  printf("heap_psram_warn: %s\n", health.heap_psram_warn ? "yes" : "no");
  printf("heap_psram_crit: %s\n", health.heap_psram_crit ? "yes" : "no");
#endif
#endif
  printf("allocs_since_run: %" PRIu64 "\n", MemGuardGetAllocCountSinceRun());
  printf("mesh_connected: %s\n",
         MeshTransportIsConnected(g_runtime->mesh) ? "yes" : "no");
  const bool wifi_connected = WifiManagerIsConnected();
  printf("wifi_connected: %s\n", wifi_connected ? "yes" : "no");
  if (wifi_connected) {
    esp_netif_ip_info_t ip_info;
    memset(&ip_info, 0, sizeof(ip_info));
    if (WifiManagerGetIpInfo(&ip_info) == ESP_OK) {
      char ip[16] = { 0 };
      esp_ip4addr_ntoa(&ip_info.ip, ip, sizeof(ip));
      printf("wifi_ip: %s\n", ip);
    } else {
      printf("wifi_ip: n/a\n");
    }
  } else {
    printf("wifi_ip: n/a\n");
  }
  const bool calibration_applied =
    (g_runtime->settings->calibration_points_count > 0u) &&
    g_runtime->settings->calibration.is_valid && !(*g_runtime->cal_overdue) &&
    !(*g_runtime->cal_due_check_suspended);
  printf("calibration_applied: %s (points=%u)\n",
         calibration_applied ? "yes" : "no",
         (unsigned)g_runtime->settings->calibration_points_count);
  return 0;
}

/**
 * @brief Execute CommandRtd.
 * @param argc Parameter argc.
 * @param argv Parameter argv.
 * @return Return the function result.
 */
static int
CommandRtd(int argc, char** argv)
{
  if (g_runtime == NULL) {
    return 1;
  }
  if (argc < 2) {
    printf("usage: rtd show | rtd ema show | rtd ema on|off | rtd ema alpha "
           "<0.0..1.0> | rtd fault [assert_ms clear_ms]\n");
    return 1;
  }

  app_settings_t* settings = g_runtime->settings;
  const char* action = argv[1];

  if (strcmp(action, "show") == 0) {
    PrintRtdEmaSettings(settings, g_runtime->sensor);
    return 0;
  }

  if (strcmp(action, "fault") == 0) {
    if (argc == 2) {
      PrintRtdFaultSettings(settings, RuntimeGetState());
      return 0;
    }
    if (argc != 4) {
      printf("usage: rtd fault [assert_ms clear_ms]\n");
      return 1;
    }
    char* end = NULL;
    const uint32_t max_ms = 60000u;
    long long assert_value = strtoll(argv[2], &end, 10);
    if (end == argv[2] || *end != '\0' || assert_value < 0) {
      printf("assert_ms must be a non-negative integer\n");
      return 1;
    }
    long long clear_value = strtoll(argv[3], &end, 10);
    if (end == argv[3] || *end != '\0' || clear_value < 0) {
      printf("clear_ms must be a non-negative integer\n");
      return 1;
    }
    uint32_t assert_ms = (uint32_t)assert_value;
    uint32_t clear_ms = (uint32_t)clear_value;
    if (assert_value > (long long)max_ms) {
      assert_ms = max_ms;
      printf("assert_ms clamped to %u\n", (unsigned)max_ms);
    }
    if (clear_value > (long long)max_ms) {
      clear_ms = max_ms;
      printf("clear_ms clamped to %u\n", (unsigned)max_ms);
    }
    settings->rtd_fault_assert_ms = assert_ms;
    settings->rtd_fault_clear_ms = clear_ms;
    const esp_err_t result =
      AppSettingsSaveRtdFaultDebounceMs(assert_ms, clear_ms);
    if (result != ESP_OK) {
      printf("save failed: %s\n", esp_err_to_name(result));
      return 1;
    }
    printf("rtd_fault_assert_ms set to %u\n", (unsigned)assert_ms);
    printf("rtd_fault_clear_ms set to %u\n", (unsigned)clear_ms);
    return 0;
  }

  if (strcmp(action, "ema") != 0) {
    printf("usage: rtd show | rtd ema show | rtd ema on|off | rtd ema alpha "
           "<0.0..1.0> | rtd fault [assert_ms clear_ms]\n");
    return 1;
  }

  if (argc < 3) {
    printf("usage: rtd ema show | rtd ema on|off | rtd ema alpha <0.0..1.0>\n");
    return 1;
  }

  const char* subaction = argv[2];
  if (strcmp(subaction, "show") == 0) {
    PrintRtdEmaSettings(settings, g_runtime->sensor);
    return 0;
  }

  if (strcmp(subaction, "on") == 0 || strcmp(subaction, "off") == 0) {
    if (argc != 3) {
      printf("usage: rtd ema on|off\n");
      return 1;
    }
    const bool enabled = (strcmp(subaction, "on") == 0);
    settings->rtd_ema_enabled = enabled;
    esp_err_t result = AppSettingsSaveRtdEmaEnabled(enabled);
    if (result != ESP_OK) {
      printf("save failed: %s\n", esp_err_to_name(result));
      return 1;
    }
    printf("rtd_ema_enabled set to %s\n", enabled ? "on" : "off");
    return 0;
  }

  if (strcmp(subaction, "alpha") == 0) {
    if (argc != 4) {
      printf("usage: rtd ema alpha <0.0..1.0>\n");
      return 1;
    }
    char* end = NULL;
    const double value = strtod(argv[3], &end);
    if (end == argv[3] || *end != '\0' || value <= 0.0 || value > 1.0) {
      printf("usage: rtd ema alpha <0.0..1.0>\n");
      return 1;
    }
    long long permille = llround(value * 1000.0);
    if (permille < 1) {
      permille = 1;
    } else if (permille > 1000) {
      permille = 1000;
    }
    const uint16_t permille_u16 = (uint16_t)permille;
    settings->rtd_ema_alpha_permille = permille_u16;
    esp_err_t result = AppSettingsSaveRtdEmaAlphaPermille(permille_u16);
    if (result != ESP_OK) {
      printf("save failed: %s\n", esp_err_to_name(result));
      return 1;
    }
    char alpha_buffer[8] = { 0 };
    FormatPermille(permille_u16, alpha_buffer, sizeof(alpha_buffer));
    printf("rtd_ema_alpha set to %s\n", alpha_buffer);
    return 0;
  }

  printf("usage: rtd show | rtd ema show | rtd ema on|off | rtd ema alpha "
         "<0.0..1.0> | rtd fault [assert_ms clear_ms]\n");
  return 1;
}

static void
PrintStackUsage(void)
{
  printf("usage: stack [show] [--headroom BYTES]\n");
  printf("       Reports monitored tasks from a static registry; includes\n");
  printf("       alloc/min_free/peak/recommended history.\n");
  printf("       recommended = round_up(peak_used + headroom, 256).\n");
}

/**
 * @brief Execute CommandStack.
 * @param argc Parameter argc.
 * @param argv Parameter argv.
 * @return Return the function result.
 */
static int
CommandStack(int argc, char** argv)
{
  uint32_t headroom_bytes = 1024;

  for (int i = 1; i < argc; ++i) {
    if (strcmp(argv[i], "show") == 0) {
      continue;
    }
    if (strcmp(argv[i], "--headroom") == 0) {
      if ((i + 1) >= argc) {
        printf("--headroom requires a byte count\n");
        PrintStackUsage();
        return 2;
      }
      headroom_bytes = (uint32_t)strtoul(argv[++i], NULL, 10);
      continue;
    }

    printf("unknown option: %s\n", argv[i]);
    PrintStackUsage();
    return 2;
  }

  RuntimePrintStackMonitor(headroom_bytes);
  return 0;
}

/**
 * @brief Execute CommandDisplay.
 * @param argc Parameter argc.
 * @param argv Parameter argv.
 * @return Return the function result.
 */
static int
CommandDisplay(int argc, char** argv)
{
  if (g_runtime == NULL) {
    return 1;
  }
  if (argc < 2) {
    printf("usage: disp show | disp units C|F | disp interval <ms> | disp attn "
           "... | disp test [ms]\n");
    return 1;
  }

  const char* action = argv[1];
  if (strcmp(action, "show") == 0) {
    const spi_host_device_t display_host = RuntimeGetDisplaySpiHost();
    const int display_host_id = (display_host == SPI3_HOST) ? 3 : 2;
#if CONFIG_APP_MAX7219_SHARE_APP_SPI_BUS
    const bool display_shared = true;
#else
    const bool display_shared = false;
#endif
#if CONFIG_APP_MAX7219_ENABLE
    const bool display_enabled = true;
#else
    const bool display_enabled = false;
#endif
    const app_display_units_t effective_units =
      RuntimeGetEffectiveDisplayUnits();
    printf("display_units: %s (effective: %s)\n",
           AppSettingsDisplayUnitsToString(g_runtime->settings->display_units),
           AppSettingsDisplayUnitsToString(effective_units));
    printf("display_sample_period_ms: %u\n",
           (unsigned)g_runtime->settings->display_sample_period_ms);
    printf("sensor_poll_period_ms (effective): %u\n",
           (unsigned)ConsoleEffectiveSensorPollPeriodMs(g_runtime->settings));
    printf("max7219_enabled: %s\n", display_enabled ? "yes" : "no");
    printf("max7219_spi_host: %d%s\n",
           display_host_id,
           display_shared ? " (shared)" : "");
    printf("max7219_chain_len: %d\n", CONFIG_APP_MAX7219_CHAIN_LEN);
    printf("max7219_intensity: %d\n", CONFIG_APP_MAX7219_INTENSITY);
    printf("max7219_pins: mosi=%d sclk=%d cs=%d%s\n",
           RuntimeGetDisplayMosiGpio(),
           RuntimeGetDisplaySclkGpio(),
           RuntimeGetDisplayCsGpio(),
           display_shared ? " (shared)" : "");
    PrintDisplayAttentionPolicy(AppSettingsGetDisplayAttentionPolicy());
    return 0;
  }

  if (strcmp(action, "units") == 0) {
    if (argc < 3) {
      printf("usage: disp units C|F\n");
      return 1;
    }
    app_display_units_t units = APP_DISPLAY_UNITS_F;
    if (!AppSettingsParseDisplayUnits(argv[2], &units)) {
      printf("usage: disp units C|F\n");
      return 1;
    }
    if (!UnitsGpioSetTemporaryUnits(units)) {
      printf("failed to set temporary units\n");
      return 1;
    }
    printf("display_units temporary override set to %s\n",
           AppSettingsDisplayUnitsToString(units));
    return 0;
  }

  if (strcmp(action, "interval") == 0) {
    if (argc != 3) {
      printf("usage: disp interval <ms>\n");
      return 1;
    }
    char* end = NULL;
    long interval_ms_long = strtol(argv[2], &end, 10);
    if (end == argv[2] || *end != '\0') {
      printf("invalid interval\n");
      return 1;
    }
    if (interval_ms_long < 100 || interval_ms_long > 3600000) {
      printf("invalid interval\n");
      return 1;
    }

    const uint32_t interval_ms = (uint32_t)interval_ms_long;
    g_runtime->settings->display_sample_period_ms = interval_ms;
    esp_err_t result = AppSettingsSaveDisplaySamplePeriodMs(interval_ms);
    if (result != ESP_OK) {
      printf("save failed: %s\n", esp_err_to_name(result));
      return 1;
    }
    RuntimeNudgeSensorTask();
    printf("display_sample_period_ms set to %u\n", (unsigned)interval_ms);
    return 0;
  }

  if (strcmp(action, "attn") == 0) {
    if (argc < 3) {
      printf("usage: disp attn show|set|defaults|ack\n");
      return 1;
    }
    const char* attn_action = argv[2];
    if (strcmp(attn_action, "show") == 0) {
      PrintDisplayAttentionPolicy(AppSettingsGetDisplayAttentionPolicy());
      return 0;
    }
    if (strcmp(attn_action, "set") == 0) {
      if (argc < 5) {
        printf("usage: disp attn set <name> <off|warn|error>\n");
        return 1;
      }
      display_attention_item_t item = kDispAttnItemSdOut;
      if (!ParseDisplayAttentionName(argv[3], &item)) {
        printf(
          "unknown name. valid: sdout, sdio, framovr, rtd, time, mesh, heap\n");
        return 1;
      }
      display_attention_severity_t severity = DISP_SEV_OFF;
      if (!ParseDisplayAttentionSeverity(argv[4], &severity)) {
        printf("unknown severity. valid: off, warn, error\n");
        return 1;
      }
      uint32_t policy = AppSettingsGetDisplayAttentionPolicy();
      policy = DisplayAttentionPolicySet(policy, item, severity);
      return SaveDisplayAttentionPolicy(policy);
    }
    if (strcmp(attn_action, "defaults") == 0) {
      const uint32_t policy = AppSettingsDefaultDisplayAttentionPolicy();
      return SaveDisplayAttentionPolicy(policy);
    }
    if (strcmp(attn_action, "ack") == 0) {
      if (RuntimeAcknowledgeDisplayAttention(kDispAttnItemFramOvr)) {
        printf("OK\n");
        return 0;
      }
      printf("ack failed\n");
      return 1;
    }
    printf("unknown action. usage: disp attn show|set|defaults|ack\n");
    return 1;
  }

  if (strcmp(action, "test") == 0) {
    uint32_t duration_ms = 2000u;
    if (argc >= 3) {
      char* end = NULL;
      unsigned long parsed = strtoul(argv[2], &end, 10);
      if (end == argv[2] || *end != '\0') {
        printf("usage: disp test [ms]\n");
        return 1;
      }
      duration_ms = (uint32_t)parsed;
    }
    esp_err_t result = RuntimeShowDisplayTestPattern(duration_ms);
    if (result != ESP_OK) {
      printf("display test failed: %s\n", esp_err_to_name(result));
      return 1;
    }
    printf("display test pattern for %u ms\n", (unsigned)duration_ms);
    return 0;
  }

  printf("unknown action. usage: disp show | disp units C|F | disp interval "
         "<ms> | disp attn ... | disp "
         "test [ms]\n");
  return 1;
}

static void
PrintUnitsUsage(void)
{
  printf("usage: units set C|F\n");
}

/**
 * @brief Execute CommandUnits.
 * @param argc Parameter argc.
 * @param argv Parameter argv.
 * @return Return the function result.
 */
static int
CommandUnits(int argc, char** argv)
{
  if (g_runtime == NULL) {
    return 1;
  }
  if (argc < 2) {
    PrintUnitsUsage();
    return 1;
  }

  const char* action = argv[1];
  if (strcmp(action, "set") == 0) {
    if (argc < 3) {
      PrintUnitsUsage();
      return 1;
    }
    app_display_units_t units = APP_DISPLAY_UNITS_F;
    if (!AppSettingsParseDisplayUnits(argv[2], &units)) {
      PrintUnitsUsage();
      return 1;
    }
    if (!UnitsGpioSetTemporaryUnits(units)) {
      printf("failed to set temporary units\n");
      return 1;
    }
    printf("display_units temporary override set to %s\n",
           AppSettingsDisplayUnitsToString(units));
    return 0;
  }

  PrintUnitsUsage();
  return 1;
}

/**
 * @brief Execute CommandRaw.
 * @param argc Parameter argc.
 * @param argv Parameter argv.
 * @return Return the function result.
 */
static int
CommandRaw(int argc, char** argv)
{
  (void)argc;
  (void)argv;
  if (g_runtime == NULL) {
    return 1;
  }

  max31865_sample_t sample;
  esp_err_t result = Max31865ReadOnce(g_runtime->sensor, &sample);
  if (result != ESP_OK) {
    printf("read failed: %s\n", esp_err_to_name(result));
    return 1;
  }

  const calibration_domain_t domain = g_runtime->settings->calibration_domain;
  double corrected_resistance_ohm = sample.resistance_ohm;
  if (domain == CAL_DOMAIN_RESISTANCE_OHM) {
    corrected_resistance_ohm = CalibrationModelEvaluateWithPoints(
      &g_runtime->settings->calibration,
      sample.resistance_ohm,
      g_runtime->settings->calibration_points,
      g_runtime->settings->calibration_points_count);
  }
  double calibrated_temp_c = sample.temperature_c;
  if (!EvaluateCalibratedTemperature_(
        sample.temperature_c, sample.resistance_ohm, &calibrated_temp_c)) {
    printf("calibration evaluate failed\n");
    return 1;
  }

  char fault[64] = { 0 };
  Max31865FormatFault(sample.fault_status, fault, sizeof(fault));

  printf("adc_code_15: %u\n", (unsigned)sample.adc_code);
  printf("resistance_ohm: %.3f\n", sample.resistance_ohm);
  if (domain == CAL_DOMAIN_RESISTANCE_OHM) {
    printf("corrected_resistance_ohm: %.3f\n", corrected_resistance_ohm);
  }
  printf("temp_raw_c: %.3f\n", sample.temperature_c);
  printf("temp_cal_c: %.3f\n", calibrated_temp_c);
  printf("fault: %s (0x%02x)\n", fault, (unsigned)sample.fault_status);
  return 0;
}

/**
 * @brief Execute FlushAllRecordsToSd.
 * @param runtime Parameter runtime.
 * @return Return the function result.
 */
static esp_err_t
FlushAllRecordsToSd(app_runtime_t* runtime)
{
  if (runtime->flush_callback == NULL) {
    return ESP_ERR_INVALID_STATE;
  }
  return runtime->flush_callback(runtime->flush_context);
}

/**
 * @brief Execute FlushOp.
 * @param runtime Parameter runtime.
 * @param ctx Parameter ctx.
 * @return Return the function result.
 */
static esp_err_t
FlushOp(app_runtime_t* runtime, void* ctx)
{
  (void)ctx;
  return FlushAllRecordsToSd(runtime);
}

/**
 * @brief Execute FormatRecordFlags.
 * @param flags Parameter flags.
 * @param out Parameter out.
 * @param out_size Parameter out_size.
 */
static void
FormatRecordFlags(uint16_t flags, char* out, size_t out_size)
{
  if (out == NULL || out_size == 0) {
    return;
  }
  out[0] = '\0';
  const struct
  {
    uint16_t flag;
    const char* name;
  } entries[] = {
    { LOG_RECORD_FLAG_TIME_VALID, "time_valid" },
    { LOG_RECORD_FLAG_CAL_VALID, "cal_valid" },
    { LOG_RECORD_FLAG_SD_ERROR, "sd_error" },
    { LOG_RECORD_FLAG_MESH_CONNECTED, "mesh_connected" },
    { LOG_RECORD_FLAG_SENSOR_FAULT, "sensor_fault" },
    { LOG_RECORD_FLAG_FRAM_FULL, "fram_full" },
    { LOG_RECORD_FLAG_RTD_EMA, "rtd_ema" },
  };

  size_t used = 0;
  bool first = true;
  for (size_t i = 0; i < sizeof(entries) / sizeof(entries[0]); ++i) {
    if ((flags & entries[i].flag) == 0) {
      continue;
    }
    const char* separator = first ? "" : ",";
    const int written =
      snprintf(out + used, out_size - used, "%s%s", separator, entries[i].name);
    if (written < 0 || (size_t)written >= out_size - used) {
      out[out_size - 1] = '\0';
      return;
    }
    used += (size_t)written;
    first = false;
  }

  if (first) {
    snprintf(out, out_size, "none");
  }
}

/**
 * @brief Execute CommandFlush.
 * @param argc Parameter argc.
 * @param argv Parameter argv.
 * @return Return the function result.
 */
static int
CommandFlush(int argc, char** argv)
{
  if (g_runtime == NULL) {
    return 1;
  }

  bool async = false;
  int32_t timeout_ms = kFlushTimeoutDefaultMs;
  for (int index = 1; index < argc; ++index) {
    const char* arg = argv[index];
    if (strcmp(arg, "--async") == 0) {
      async = true;
      continue;
    }
    if (strcmp(arg, "--timeout") == 0) {
      if ((index + 1) >= argc) {
        printf("usage: flush [--async] [--timeout <ms>]\n");
        return 1;
      }
      char* end = NULL;
      const long timeout_long = strtol(argv[index + 1], &end, 10);
      if (end == argv[index + 1] || *end != '\0') {
        printf("invalid timeout\n");
        return 1;
      }
      timeout_ms = (int32_t)timeout_long;
      if (timeout_ms < 0) {
        printf("invalid timeout\n");
        return 1;
      }
      index++;
      continue;
    }
    printf("usage: flush [--async] [--timeout <ms>]\n");
    return 1;
  }

  if (RuntimeIsRunning()) {
    runtime_state_t* state = RuntimeGetState();
    if (state == NULL || state->sd_flush_task == NULL) {
      printf("flush unavailable; SD flush task not running\n");
      return 1;
    }
    const TickType_t now_ticks = xTaskGetTickCount();
    const TickType_t deadline_ticks =
      (timeout_ms > 0) ? (now_ticks + pdMS_TO_TICKS(timeout_ms)) : 0;
    state->sd_manual_drain_active = true;
    state->sd_manual_drain_deadline_ticks = deadline_ticks;
    state->sd_manual_drain_passes = 0;
    state->sd_flush_pending = true;
    state->sd_next_flush_allowed_ticks = 0;
    xTaskNotifyGive(state->sd_flush_task);

    if (async) {
      printf("flush armed (timeout=%d ms)\n", (int)timeout_ms);
      return 0;
    }

    uint32_t remaining = 0;
    while (true) {
      if (ConsoleFramLogLock(state)) {
        remaining = FramLogGetBufferedRecords(&state->fram_log);
        ConsoleFramLogUnlock(state);
      }

      if (remaining == 0u) {
        break;
      }
      if (!state->sd_manual_drain_active) {
        break;
      }
      if (deadline_ticks != 0 &&
          (int32_t)(xTaskGetTickCount() - deadline_ticks) >= 0) {
        break;
      }
      vTaskDelay(pdMS_TO_TICKS(100));
    }

    if (remaining == 0u) {
      printf("flush complete; remaining=0\n");
      return 0;
    }
    if (deadline_ticks != 0 &&
        (int32_t)(xTaskGetTickCount() - deadline_ticks) >= 0) {
      printf("flush timed out; remaining=%u\n", (unsigned)remaining);
      return 1;
    }
    printf("flush stopped; remaining=%u\n", (unsigned)remaining);
    return 1;
  }

  if (async) {
    printf("flush async unsupported while stopped\n");
    return 1;
  }

  const esp_err_t result = RuntimeWithTemporarySdMount(&FlushOp, NULL);
  if (result != ESP_OK) {
    printf("flush failed: %s\n", esp_err_to_name(result));
    return 1;
  }
  return 0;
}

/**
 * @brief Execute CommandFram.
 * @param argc Parameter argc.
 * @param argv Parameter argv.
 * @return Return the function result.
 */
static int
CommandFram(int argc, char** argv)
{
  if (g_runtime == NULL) {
    return 1;
  }
  if (argc < 2) {
    printf("usage: fram status | fram show | fram clear\n");
    return 1;
  }

  const char* action = argv[1];
  if (strcmp(action, "status") != 0 && strcmp(action, "show") != 0 &&
      strcmp(action, "clear") != 0) {
    printf(
      "unknown fram command. try 'fram status | fram show | fram clear'\n");
    return 1;
  }

  runtime_state_t* state = RuntimeGetState();
  if (!ConsoleFramLogLock(state)) {
    printf("fram: busy (lock timeout)\n");
    return 1;
  }
  fram_log_status_t status;
  esp_err_t result = FramLogGetStatus(g_runtime->fram_log, &status);
  ConsoleFramLogUnlock(state);
  if (result != ESP_OK) {
    printf("fram: not initialized\n");
    return 1;
  }
  status.flush_watermark_records =
    g_runtime->settings->fram_flush_watermark_records;

  printf("fram: mounted=%s full=%s\n",
         status.mounted ? "yes" : "no",
         status.full ? "yes" : "no");
  printf("fram: cap=%u rec_size=%u watermark=%u\n",
         (unsigned)status.capacity_records,
         (unsigned)status.record_size_bytes,
         (unsigned)status.flush_watermark_records);
  printf("fram: write=%u read=%u count=%u seq=%u id=%" PRIu64 "\n",
         (unsigned)status.write_index_abs,
         (unsigned)status.read_index_abs,
         (unsigned)status.buffered_count,
         (unsigned)status.next_sequence,
         status.next_record_id);
  if (strcmp(action, "clear") == 0) {
    if (!ConsoleFramLogLock(state)) {
      printf("fram clear skipped: lock timeout\n");
      return 1;
    }
    result = FramLogReset(g_runtime->fram_log);
    ConsoleFramLogUnlock(state);
    if (result != ESP_OK) {
      printf("fram clear failed: %s\n", esp_err_to_name(result));
      return 1;
    }
    if (g_runtime->fram_full != NULL) {
      *g_runtime->fram_full = false;
    }
    printf("fram: cleared\n");
    return 0;
  }
  if (strcmp(action, "show") == 0) {
    if (!ConsoleFramLogLock(state)) {
      printf("fram show skipped: lock timeout\n");
      return 1;
    }
    const uint32_t buffered = FramLogGetBufferedRecords(g_runtime->fram_log);
    const uint64_t last_sd_id = SdLoggerLastRecordIdOnSd(g_runtime->sd_logger);
    printf("fram: buffered=%u last_sd_record_id=%" PRIu64 "\n",
           (unsigned)buffered,
           last_sd_id);
    for (uint32_t offset = 0; offset < buffered; ++offset) {
      log_record_t record;
      const esp_err_t peek_result =
        FramLogPeekOffset(g_runtime->fram_log, offset, &record);
      if (peek_result == ESP_ERR_NOT_FOUND) {
        break;
      }
      const bool corrupted = (peek_result == ESP_ERR_INVALID_RESPONSE);
      if (peek_result != ESP_OK && !corrupted) {
        printf("fram show failed at offset %u: %s\n",
               (unsigned)offset,
               esp_err_to_name(peek_result));
        ConsoleFramLogUnlock(state);
        return 1;
      }

      if (corrupted) {
        uint16_t actual_crc = 0;
        const fram_log_validate_result_t validate_result =
          FramLogValidateRecord(&record, &actual_crc);
        printf(
          "record[%u]: corrupt=yes reason=%s exp_crc=0x%04x act_crc=0x%04x\n",
          (unsigned)offset,
          FramLogValidateResultToString(validate_result),
          (unsigned)record.crc16_ccitt,
          (unsigned)actual_crc);
        continue;
      }

      char time_string[32] = "unknown";
      if (record.timestamp_epoch_sec > 0) {
        const time_t epoch = (time_t)record.timestamp_epoch_sec;
        FormatFileTime(&epoch, time_string, sizeof(time_string));
      }

      char flags_string[128];
      FormatRecordFlags(record.flags, flags_string, sizeof(flags_string));
      const bool pending = record.record_id > last_sd_id;

      printf("record[%u]: id=%" PRIu64 " seq=%u pending=%s corrupt=no\n",
             (unsigned)offset,
             record.record_id,
             (unsigned)record.sequence,
             pending ? "yes" : "no");
      printf("  time: %s.%03d epoch=%" PRIi64 "\n",
             time_string,
             (int)record.timestamp_millis,
             record.timestamp_epoch_sec);
      printf("  temp: raw=%.3fC cal=%.3fC resistance=%.3f ohm\n",
             record.raw_temp_milli_c / 1000.0,
             record.temp_milli_c / 1000.0,
             record.resistance_milli_ohm / 1000.0);
      printf("  flags: 0x%04x [%s]\n", (unsigned)record.flags, flags_string);
      printf("  fault_status: 0x%02x\n", (unsigned)record.fault_status);
    }
    ConsoleFramLogUnlock(state);
  }
  return 0;
}

/**
 * @brief Execute PrintSdStatus.
 * @param runtime Parameter runtime.
 */
static void
PrintSdStatus(const app_runtime_t* runtime)
{
  const sd_logger_t* logger = runtime->sd_logger;
  const bool sd_mounted = logger->is_mounted;
  const bool sd_degraded = RuntimeSdIsDegraded();
  const uint32_t sd_fail_count = RuntimeSdFailCount();
  const TickType_t now_ticks = xTaskGetTickCount();
  const uint32_t sd_backoff_until = RuntimeSdBackoffUntilTicks();
  const runtime_cached_status_t* cached_status = RuntimeGetCachedStatus();
  uint32_t sd_backoff_remaining_ms = 0;
  if (sd_backoff_until != 0 && now_ticks < (TickType_t)sd_backoff_until) {
    sd_backoff_remaining_ms =
      (uint32_t)pdTICKS_TO_MS((TickType_t)sd_backoff_until - now_ticks);
  }

  printf("sd_mounted: %s\n", sd_mounted ? "yes" : "no");
  printf("sd_degraded: %s\n", sd_degraded ? "yes" : "no");
  if (cached_status != NULL) {
    printf("deferred_count: %u\n", (unsigned)cached_status->deferred_count);
    printf("deferred_drops: %u\n", (unsigned)cached_status->deferred_drops);
    printf("deferred_active: %s\n",
           cached_status->deferred_active ? "yes" : "no");
    printf("i2c_quiesce_active: %s\n",
           cached_status->i2c_quiesce_active ? "yes" : "no");
  }
  printf("sd_fail_count: %u\n", (unsigned)sd_fail_count);
  printf("sd_backoff_remaining_ms: %u\n", (unsigned)sd_backoff_remaining_ms);
  runtime_state_t* state = RuntimeGetState();
  if (state != NULL) {
    printf("sd_verify_readback: %s\n",
           state->sd_verify_readback ? "on" : "off");
  }
  printf("sd_last_record_id: %" PRIu64 "\n", SdLoggerLastRecordIdOnSd(logger));
  if (sd_mounted) {
    printf("sd_mount_point: %s\n", logger->mount_point);
    if (logger->card != NULL) {
      const uint64_t size_bytes = (uint64_t)logger->card->csd.capacity *
                                  (uint64_t)logger->card->csd.sector_size;
      printf("sd_card_name: %s\n", logger->card->cid.name);
      printf("sd_card_size_mb: %llu\n",
             (unsigned long long)(size_bytes / (1024ULL * 1024ULL)));
    }
  }
}

/**
 * @brief Execute FormatFileTime.
 * @param timestamp Parameter timestamp.
 * @param buffer Parameter buffer.
 * @param buffer_size Parameter buffer_size.
 */
static void
FormatFileTime(const time_t* timestamp, char* buffer, size_t buffer_size)
{
  if (buffer == NULL || buffer_size == 0) {
    return;
  }
  struct tm time_info;
  if (timestamp == NULL || gmtime_r(timestamp, &time_info) == NULL) {
    buffer[0] = '\0';
    return;
  }
  strftime(buffer, buffer_size, "%Y-%m-%d %H:%M:%SZ", &time_info);
}

/**
 * @brief Execute CommandSdView.
 * @param logger Parameter logger.
 * @return Return the function result.
 */
static int
CommandSdView(const sd_logger_t* logger)
{
  if (!logger->is_mounted) {
    printf("sd not mounted\n");
    return 1;
  }

  runtime_state_t* state = RuntimeGetState();
  if (state == NULL || !RuntimeSdIoLock(state, pdMS_TO_TICKS(2000))) {
    printf("sd view failed: sd io lock timeout\n");
    return 1;
  }

  if (!RuntimeSpiBusLockForSharedDevices(state, pdMS_TO_TICKS(2000))) {
    RuntimeSdIoUnlock(state);
    printf("sd view failed: spi bus lock timeout\n");
    return 1;
  }

  DIR* dir = opendir(logger->mount_point);
  if (dir == NULL) {
    RuntimeSpiBusUnlockForSharedDevices(state);
    RuntimeSdIoUnlock(state);
    printf("sd view failed: %s\n", strerror(errno));
    return 1;
  }

  printf("sd files in %s:\n", logger->mount_point);
  struct dirent* entry = NULL;
  int file_count = 0;
  while ((entry = readdir(dir)) != NULL) {
    if (strcmp(entry->d_name, ".") == 0 || strcmp(entry->d_name, "..") == 0) {
      continue;
    }
    // FATFS long file names may be up to 255 chars. Include mount point, '/',
    // and NUL terminator. Keep this comfortably above worst-case.
    char path[512];
    int path_length =
      snprintf(path, sizeof(path), "%s/%s", logger->mount_point, entry->d_name);
    if (path_length < 0 || path_length >= (int)sizeof(path)) {
      printf("  %s (path too long)\n", entry->d_name);
      continue;
    }
    struct stat info;
    if (stat(path, &info) != 0) {
      printf("  %s (stat failed: %s)\n", entry->d_name, strerror(errno));
      continue;
    }
    char time_buffer[32];
    FormatFileTime(&info.st_mtime, time_buffer, sizeof(time_buffer));
    const char* kind = S_ISDIR(info.st_mode) ? "dir" : "file";
    printf("  %s %-4s size=%llu mtime=%s\n",
           entry->d_name,
           kind,
           (unsigned long long)info.st_size,
           time_buffer);
    ++file_count;
  }
  closedir(dir);
  RuntimeSpiBusUnlockForSharedDevices(state);
  RuntimeSdIoUnlock(state);
  printf("sd file count: %d\n", file_count);
  return 0;
}

/**
 * @brief Execute SdStatusOp.
 * @param runtime Parameter runtime.
 * @param ctx Parameter ctx.
 * @return Return the function result.
 */
static esp_err_t
SdStatusOp(app_runtime_t* runtime, void* ctx)
{
  (void)ctx;
  PrintSdStatus(runtime);
  return ESP_OK;
}

/**
 * @brief Execute SdViewOp.
 * @param runtime Parameter runtime.
 * @param ctx Parameter ctx.
 * @return Return the function result.
 */
static esp_err_t
SdViewOp(app_runtime_t* runtime, void* ctx)
{
  (void)ctx;
  return (CommandSdView(runtime->sd_logger) == 0) ? ESP_OK : ESP_FAIL;
}

/**
 * @brief Execute SdFormatOp.
 * @param runtime Parameter runtime.
 * @param ctx Parameter ctx.
 * @return Return the function result.
 */
static esp_err_t
SdFormatOp(app_runtime_t* runtime, void* ctx)
{
  (void)ctx;
  runtime_state_t* state = RuntimeGetState();
  if (state == NULL || !RuntimeSdIoLock(state, pdMS_TO_TICKS(2000))) {
    return ESP_ERR_TIMEOUT;
  }
  if (!RuntimeSpiBusLockForSharedDevices(state, pdMS_TO_TICKS(2000))) {
    RuntimeSdIoUnlock(state);
    return ESP_ERR_TIMEOUT;
  }
  esp_err_t result = SdLoggerFormatDestructive(runtime->sd_logger);
  RuntimeSpiBusUnlockForSharedDevices(state);
  RuntimeSdIoUnlock(state);
  return result;
}

/**
 * @brief Execute SdMountOp.
 * @param runtime Parameter runtime.
 * @param ctx Parameter ctx.
 * @return Return the function result.
 */
static esp_err_t
SdMountOp(app_runtime_t* runtime, void* ctx)
{
  (void)runtime;
  (void)ctx;
  return ESP_OK;
}

/**
 * @brief Execute CommandSd.
 * @param argc Parameter argc.
 * @param argv Parameter argv.
 * @return Return the function result.
 */
static int
CommandSd(int argc, char** argv)
{
  if (g_runtime == NULL || g_runtime->sd_logger == NULL) {
    return 1;
  }
  if (argc < 2) {
    printf("usage: sd status|mount|unmount|format|view|verify\n");
    return 1;
  }

  const char* action = argv[1];
  if (strcmp(action, "status") == 0) {
    if (!heap_caps_check_integrity_all(true)) {
      printf("heap integrity check failed (heap corrupted)\r\n");
      return 1;
    }

    if (!RuntimeIsRunning()) {
      esp_err_t result = RuntimeWithTemporarySdMount(&SdStatusOp, NULL);
      if (result != ESP_OK) {
        printf("sd status failed: %s\n", esp_err_to_name(result));
        return 1;
      }
      return 0;
    }
    PrintSdStatus(g_runtime);
    return 0;
  }

  if (strcmp(action, "view") == 0) {
    if (!RuntimeIsRunning()) {
      esp_err_t result = RuntimeWithTemporarySdMount(&SdViewOp, NULL);
      if (result != ESP_OK) {
        printf("sd view failed: %s\n", esp_err_to_name(result));
        return 1;
      }
      return 0;
    }
    return CommandSdView(g_runtime->sd_logger);
  }

  if (strcmp(action, "verify") == 0) {
    runtime_state_t* state = RuntimeGetState();
    if (state == NULL) {
      printf("sd verify failed: runtime unavailable\n");
      return 1;
    }
    if (argc < 3) {
      printf("sd verify readback: %s\n",
             state->sd_verify_readback ? "on" : "off");
      return 0;
    }
    const char* value = argv[2];
    if (strcmp(value, "on") == 0) {
      const esp_err_t save_result = AppSettingsSaveSdVerifyReadback(true);
      if (save_result != ESP_OK) {
        printf("sd verify readback save failed: %s\n",
               esp_err_to_name(save_result));
        return 1;
      }
      state->sd_verify_readback = true;
      g_runtime->settings->sd_verify_readback = true;
      printf("sd verify readback: on\n");
      return 0;
    }
    if (strcmp(value, "off") == 0) {
      const esp_err_t save_result = AppSettingsSaveSdVerifyReadback(false);
      if (save_result != ESP_OK) {
        printf("sd verify readback save failed: %s\n",
               esp_err_to_name(save_result));
        return 1;
      }
      state->sd_verify_readback = false;
      g_runtime->settings->sd_verify_readback = false;
      printf("sd verify readback: off\n");
      return 0;
    }
    printf("usage: sd verify\n");
    printf("       sd verify on|off\n");
    return 1;
  }

  if (RuntimeIsRunning()) {
    printf("Stop run mode first: run stop\n");
    return 1;
  }

  if (strcmp(action, "mount") == 0) {
    esp_err_t result = RuntimeWithTemporarySdMount(&SdMountOp, NULL);
    if (result != ESP_OK) {
      printf("sd mount failed: %s\n", esp_err_to_name(result));
      return 1;
    }
    printf("sd mounted (temporary)\n");
    return 0;
  }

  if (strcmp(action, "unmount") == 0) {
    esp_err_t result = RuntimeSdUnmountNow();
    if (result != ESP_OK) {
      printf("sd unmount failed: %s\n", esp_err_to_name(result));
      return 1;
    }
    printf("sd unmounted\n");
    return 0;
  }

  if (strcmp(action, "format") == 0) {
    esp_err_t result = RuntimeWithTemporarySdMount(&SdFormatOp, NULL);
    if (result != ESP_OK) {
      printf("sd format failed: %s\n", esp_err_to_name(result));
      return 1;
    }
    printf("sd format complete (FAT filesystem recreated)\n");
    return 0;
  }

  printf(
    "unknown sd command. try 'sd status|mount|unmount|format|view|verify'\n");
  return 1;
}

// NOTE: The "log" command uses manual argv parsing.
//
// We intentionally do NOT use argtable for this command because argtable's
// positional parsing cannot express "subcommand + single positional value"
// without accidentally binding the value to the wrong field.
//
// Example of the problem with argtable positional arguments:
//   "log flush_period 300000"
// would bind "300000" to the first positional integer field, not the one
// associated with "flush_period".
//
// Manual parsing keeps the CLI simple and predictable.

static struct
{
  struct arg_str* action;
  struct arg_str* mode_value;
  struct arg_end* end;
} g_mode_args;

static struct
{
  struct arg_str* action;
  struct arg_end* end;
} g_data_args;

static struct
{
  struct arg_str* action;
  struct arg_end* end;
} g_run_args;

static struct
{
  struct arg_str* action;
  struct arg_str* posix;
  struct arg_end* end;
} g_tz_args;

static struct
{
  struct arg_str* action;
  struct arg_str* local_time;
  struct arg_int* is_dst;
  struct arg_end* end;
} g_time_args;

static struct
{
  struct arg_str* action;
  struct arg_int* enabled;
  struct arg_end* end;
} g_dst_args;

static struct
{
  struct arg_str* action;
  struct arg_str* role;
  struct arg_end* end;
} g_role_args;

static struct
{
  struct arg_str* action;
  struct arg_str* mode;
  struct arg_end* end;
} g_net_args;

static struct
{
  struct arg_str* action;
  struct arg_int* enabled;
  struct arg_end* end;
} g_children_args;

/**
 * @brief Execute CommandLog.
 * @param argc Parameter argc.
 * @param argv Parameter argv.
 * @return Return the function result.
 */
static int
CommandLog(int argc, char** argv)
{
  if (g_runtime == NULL) {
    return 1;
  }

  if (argc < 2) {
    printf("usage: log interval <ms> | log watermark <records> | log "
           "flush_period <ms> | log batch <bytes> | log show\n");
    return 1;
  }

  const char* action = argv[1];
  if (strcmp(action, "flush_ms") == 0) {
    // Backwards/typo-friendly alias.
    action = "flush_period";
  }
  if (strcmp(action, "interval") == 0) {
    if (argc != 3) {
      printf("usage: log interval <ms>\n");
      return 1;
    }
    char* end = NULL;
    long interval_ms_long = strtol(argv[2], &end, 10);
    if (end == argv[2] || *end != '\0') {
      printf("invalid interval\n");
      return 1;
    }
    const int interval_ms = (int)interval_ms_long;
    if (interval_ms < 100 || interval_ms > 3600000) {
      printf("invalid interval\n");
      return 1;
    }
    g_runtime->settings->log_period_ms = (uint32_t)interval_ms;
    esp_err_t result = AppSettingsSaveLogPeriodMs((uint32_t)interval_ms);
    if (result != ESP_OK) {
      printf("save failed: %s\n", esp_err_to_name(result));
      return 1;
    }
    RuntimeNudgeSensorTask();
    printf("log_period_ms set to %d\n", interval_ms);
    return 0;
  }

  if (strcmp(action, "watermark") == 0) {
    if (argc != 3) {
      printf("usage: log watermark <records>\n");
      return 1;
    }
    char* end = NULL;
    long watermark_long = strtol(argv[2], &end, 10);
    if (end == argv[2] || *end != '\0') {
      printf("invalid watermark\n");
      return 1;
    }
    const int watermark = (int)watermark_long;
    if (watermark < 1) {
      printf("invalid watermark\n");
      return 1;
    }
    g_runtime->settings->fram_flush_watermark_records = (uint32_t)watermark;
    esp_err_t result =
      AppSettingsSaveFramFlushWatermarkRecords((uint32_t)watermark);
    if (result != ESP_OK) {
      printf("save failed: %s\n", esp_err_to_name(result));
      return 1;
    }
    printf("fram flush watermark set to %d\n", watermark);
    return 0;
  }

  if (strcmp(action, "flush_period") == 0) {
    if (argc != 3) {
      printf("usage: log flush_period <ms>\n");
      return 1;
    }
    char* end = NULL;
    long period_ms_long = strtol(argv[2], &end, 10);
    if (end == argv[2] || *end != '\0') {
      printf("invalid period\n");
      return 1;
    }
    const int period_ms = (int)period_ms_long;
    if (period_ms < 1000) {
      printf("invalid period\n");
      return 1;
    }
    g_runtime->settings->sd_flush_period_ms = (uint32_t)period_ms;
    esp_err_t result = AppSettingsSaveSdFlushPeriodMs((uint32_t)period_ms);
    if (result != ESP_OK) {
      printf("save failed: %s\n", esp_err_to_name(result));
      return 1;
    }
    printf("sd_flush_period_ms set to %d\n", period_ms);
    return 0;
  }

  if (strcmp(action, "batch") == 0) {
    if (argc != 3) {
      printf("usage: log batch <bytes>\n");
      return 1;
    }
    char* end = NULL;
    long batch_bytes_long = strtol(argv[2], &end, 10);
    if (end == argv[2] || *end != '\0') {
      printf("invalid batch size\n");
      return 1;
    }
    const int batch_bytes = (int)batch_bytes_long;
    if (batch_bytes < 4096) {
      printf("invalid batch size\n");
      return 1;
    }
    g_runtime->settings->sd_batch_bytes_target = (uint32_t)batch_bytes;
    esp_err_t result = AppSettingsSaveSdBatchBytes((uint32_t)batch_bytes);
    if (result != ESP_OK) {
      printf("save failed: %s\n", esp_err_to_name(result));
      return 1;
    }
    printf("sd batch target set to %d bytes\n", batch_bytes);
    return 0;
  }

  if (strcmp(action, "show") == 0) {
    printf("log_period_ms: %u\n", (unsigned)g_runtime->settings->log_period_ms);
    printf("fram_flush_watermark_records: %u\n",
           (unsigned)g_runtime->settings->fram_flush_watermark_records);
    printf("sd_flush_period_ms: %u\n",
           (unsigned)g_runtime->settings->sd_flush_period_ms);
    printf("sd_batch_target_bytes: %u\n",
           (unsigned)g_runtime->settings->sd_batch_bytes_target);
    return 0;
  }

  printf("unknown action. usage: log interval <ms> | log watermark <records> | "
         "log flush_period <ms> | log batch <bytes> | log show\n");
  return 1;
}

/**
 * @brief Execute CommandErrlog.
 * @param argc Parameter argc.
 * @param argv Parameter argv.
 * @return Return the function result.
 */
static int
CommandErrlog(int argc, char** argv)
{
  runtime_state_t* state = RuntimeGetState();
  if (state != NULL) {
    (void)RuntimeMaybeInitFramErrorLog(state);
  }
  if (g_runtime == NULL || g_runtime->fram_error_log == NULL) {
    printf("runtime not ready\n");
    return 1;
  }
  if (!g_runtime->fram_error_log->initialized) {
    uint64_t pending_active = 0;
    uint64_t pending_resolved = 0;
    if (state != NULL) {
      taskENTER_CRITICAL(&state->errlog_latch_lock);
      pending_active = state->errlog_pending_active_mask;
      pending_resolved = state->errlog_pending_resolved_mask;
      taskEXIT_CRITICAL(&state->errlog_latch_lock);
    }
    printf("FRAM errlog unavailable; pending_latches=0x%016" PRIx64
           "/0x%016" PRIx64 "\n",
           pending_active,
           pending_resolved);
    return 1;
  }
  if (argc < 2) {
    printf(
      "usage: errlog show [--last N] | errlog stats | errlog status | errlog "
      "clear\n");
    return 1;
  }

  const char* action = argv[1];
  fram_error_log_status_t status = { 0 };
  const esp_err_t status_result =
    FramErrorLogGetStatus(g_runtime->fram_error_log, &status);
  if (status_result != ESP_OK) {
    printf("errlog status failed: %s\n", esp_err_to_name(status_result));
    return 1;
  }
  if (strcmp(action, "stats") == 0) {
    if (status.state == FRAM_ERRLOG_STATE_CORRUPT) {
      printf("FRAM errlog corrupt; run `errlog clear` to reinitialize.\n");
      return 1;
    }
    fram_error_log_stats_t stats = { 0 };
    const esp_err_t result =
      FramErrorLogGetStats(g_runtime->fram_error_log, &stats);
    if (result != ESP_OK) {
      printf("errlog stats failed: %s\n", esp_err_to_name(result));
      return 1;
    }
    printf("errlog count=%" PRIu32 " capacity=%" PRIu32 " write_index=%" PRIu32
           "\n",
           stats.count,
           stats.capacity,
           stats.write_index);
    printf("errlog active_bitmap=0x%08" PRIx32 "%08" PRIx32 "\n",
           stats.active_bitmap_high,
           stats.active_bitmap_low);
    return 0;
  }

  if (strcmp(action, "status") == 0) {
    printf("errlog state=%s blank=%s\n",
           FramErrorLogStateToString(status.state),
           status.region_blank ? "yes" : "no");
    printf("header copy0: valid=%s reason=%s\n",
           status.copy0.valid ? "yes" : "no",
           FramErrorLogHeaderReasonToString(status.copy0.reason));
    printf("header copy1: valid=%s reason=%s\n",
           status.copy1.valid ? "yes" : "no",
           FramErrorLogHeaderReasonToString(status.copy1.reason));
    printf("rtc_pending=%" PRIu16 "\n", RuntimeRtcErrlogLatchPendingCount());
    return 0;
  }

  if (strcmp(action, "clear") == 0) {
    const esp_err_t result = FramErrorLogClear(g_runtime->fram_error_log);
    if (result != ESP_OK) {
      printf("errlog clear failed: %s\n", esp_err_to_name(result));
      return 1;
    }
    printf("errlog cleared\n");
    return 0;
  }

  if (strcmp(action, "show") == 0) {
    if (status.state == FRAM_ERRLOG_STATE_CORRUPT) {
      printf("FRAM errlog corrupt; run `errlog clear` to reinitialize.\n");
      printf("header copy0: valid=%s reason=%s\n",
             status.copy0.valid ? "yes" : "no",
             FramErrorLogHeaderReasonToString(status.copy0.reason));
      printf("header copy1: valid=%s reason=%s\n",
             status.copy1.valid ? "yes" : "no",
             FramErrorLogHeaderReasonToString(status.copy1.reason));
      return 0;
    }
    int last = 0;
    for (int i = 2; i < argc; ++i) {
      if (strcmp(argv[i], "--last") == 0 && (i + 1) < argc) {
        last = atoi(argv[++i]);
      } else {
        printf("usage: errlog show [--last N]\n");
        return 1;
      }
    }
    if (last < 0) {
      printf("last must be >= 0\n");
      return 1;
    }
    fram_error_log_stats_t stats = { 0 };
    const esp_err_t stats_result =
      FramErrorLogGetStats(g_runtime->fram_error_log, &stats);
    if (stats_result != ESP_OK) {
      printf("errlog show failed: %s\n", esp_err_to_name(stats_result));
      return 1;
    }
    if (stats.count == 0) {
      printf("errlog empty\n");
      return 0;
    }
    uint32_t start_index = 0;
    if (last > 0 && (uint32_t)last < stats.count) {
      start_index = stats.count - (uint32_t)last;
    }
    printf("errlog entries: showing %" PRIu32 " of %" PRIu32 "\n",
           stats.count - start_index,
           stats.count);
    for (uint32_t i = start_index; i < stats.count; ++i) {
      fram_error_log_entry_t entry = { 0 };
      bool crc_ok = false;
      const esp_err_t result =
        FramErrorLogReadEntry(g_runtime->fram_error_log, i, &entry, &crc_ok);
      if (result != ESP_OK) {
        printf(
          "entry[%" PRIu32 "] read failed: %s\n", i, esp_err_to_name(result));
        continue;
      }
      char utc_buffer[32];
      char local_buffer[32];
      char flags_buffer[32];
      FormatUtcEpochIso8601(entry.epoch_sec, utc_buffer, sizeof(utc_buffer));
      FormatLocalEpochIso8601(
        entry.epoch_sec, local_buffer, sizeof(local_buffer));
      FormatErrlogFlags(entry.flags, flags_buffer, sizeof(flags_buffer));
      printf("entry[%" PRIu32 "]: utc=%s local=%s.%03u code=%u flags=%s "
             "detail0=%" PRId32 " detail1=%" PRId32 " crc=%s\n",
             i,
             utc_buffer,
             local_buffer,
             (unsigned)entry.millis,
             (unsigned)entry.code,
             flags_buffer,
             entry.detail0,
             entry.detail1,
             crc_ok ? "ok" : "bad");
    }
    return 0;
  }

  printf(
    "unknown action. usage: errlog show [--last N] | errlog stats | errlog "
    "status | errlog clear\n");
  return 1;
}

static struct
{
  struct arg_str* action;
  struct arg_dbl* raw_c;
  struct arg_dbl* actual_c;
  struct arg_int* every_ms;
  struct arg_int* seconds;
  struct arg_dbl* stable_stddev_c;
  struct arg_int* min_seconds;
  struct arg_int* timeout_seconds;
  struct arg_dbl* drift_c_per_min;
  struct arg_lit* no_drift_limit;
  struct arg_str* mode;
  struct arg_lit* allow_wide_slope;
  struct arg_end* end;
} g_cal_args;

static bool
CalConsoleOpLock_(TickType_t ticks)
{
  if (g_cal_console_op_mutex == NULL) {
    return false;
  }
  return xSemaphoreTake(g_cal_console_op_mutex, ticks) == pdTRUE;
}

static void
CalConsoleOpUnlock_(void)
{
  if (g_cal_console_op_mutex == NULL) {
    return;
  }
  (void)xSemaphoreGive(g_cal_console_op_mutex);
}

static bool
CalConsoleOpIsActive(void)
{
  bool active = false;
  if (!CalConsoleOpLock_(pdMS_TO_TICKS(50))) {
    return false;
  }
  active = (g_cal_console_op.mode != CAL_CONSOLE_OP_NONE);
  CalConsoleOpUnlock_();
  return active;
}

static esp_err_t
CalConsoleOpStartLive(uint32_t every_ms,
                      int seconds,
                      int live_output_mode,
                      bool drift_notify_armed,
                      double drift_notify_threshold_c_per_min)
{
  if (!CalConsoleOpLock_(pdMS_TO_TICKS(100))) {
    return ESP_ERR_INVALID_STATE;
  }
  if (g_cal_console_op.mode != CAL_CONSOLE_OP_NONE) {
    CalConsoleOpUnlock_();
    return ESP_ERR_INVALID_STATE;
  }
  g_cal_console_op.mode = CAL_CONSOLE_OP_LIVE;
  g_cal_console_op.task_handle = NULL;
  g_cal_console_op.cancel_requested = false;
  g_cal_console_op.print_every_ms = every_ms;
  g_cal_console_op.live_seconds = seconds;
  g_cal_console_op.capture_actual_temp_c = 0.0;
  g_cal_console_op.capture_stable_stddev_c = 0.0;
  g_cal_console_op.capture_drift_limit_enabled = true;
  g_cal_console_op.capture_drift_limit_c_per_min = 0.0;
  g_cal_console_op.capture_drift_limit_source = CAL_DRIFT_LIMIT_SOURCE_DEFAULT;
  g_cal_console_op.capture_min_seconds = 0;
  g_cal_console_op.capture_timeout_seconds = 0;
  g_cal_console_op.capture_armed = false;
  g_cal_console_op.capture_armed_start_us = 0;
  g_cal_console_op.live_drift_notify_armed = drift_notify_armed;
  g_cal_console_op.live_drift_notify_threshold_c_per_min =
    drift_notify_threshold_c_per_min;
  g_cal_console_op.live_output_mode =
    (live_output_mode == (int)CAL_CONSOLE_LIVE_OUTPUT_CALIBRATED)
      ? CAL_CONSOLE_LIVE_OUTPUT_CALIBRATED
      : CAL_CONSOLE_LIVE_OUTPUT_RAW;
  g_cal_console_op.live_drift_under_start_us = -1;
  g_cal_console_op.live_drift_notify_sent = false;
  g_cal_console_op.start_us = esp_timer_get_time();
  g_cal_console_op.last_sample_count = 0;
  g_cal_console_op.start_internal_free =
    heap_caps_get_free_size(MALLOC_CAP_INTERNAL | MALLOC_CAP_8BIT);
  g_cal_console_op.start_internal_largest =
    heap_caps_get_largest_free_block(MALLOC_CAP_INTERNAL | MALLOC_CAP_8BIT);
  g_cal_console_op.start_psram_free =
    heap_caps_get_free_size(MALLOC_CAP_SPIRAM | MALLOC_CAP_8BIT);
  g_cal_console_op.start_psram_largest =
    heap_caps_get_largest_free_block(MALLOC_CAP_SPIRAM | MALLOC_CAP_8BIT);
  g_cal_console_op.low_internal_free = g_cal_console_op.start_internal_free;
  g_cal_console_op.low_internal_largest =
    g_cal_console_op.start_internal_largest;
  g_cal_console_op.min_stack_free_bytes = UINT32_MAX;
  g_cal_console_op.max_temp_buffer_bytes = 0u;
  g_cal_runtime_last_sample_id = 0u;
  if (!CalHistoryEnsureStorage_()) {
    g_cal_console_op.mode = CAL_CONSOLE_OP_NONE;
    g_cal_console_op.task_handle = NULL;
    CalConsoleOpUnlock_();
    printf("cal live: requires PSRAM-backed metric history\n");
    return ESP_ERR_NO_MEM;
  }
  BaseType_t created = xTaskCreate(&CalConsoleOpTask,
                                   "cal_op",
                                   kCalOpTaskStackBytes,
                                   NULL,
                                   2,
                                   &g_cal_console_op.task_handle);
  if (created != pdPASS) {
    g_cal_console_op.mode = CAL_CONSOLE_OP_NONE;
    g_cal_console_op.task_handle = NULL;
    CalConsoleOpUnlock_();
    return ESP_ERR_NO_MEM;
  }
  const char* mode_label =
    (g_cal_console_op.live_output_mode == CAL_CONSOLE_LIVE_OUTPUT_CALIBRATED)
      ? "cal livecal"
      : "cal live";
  CalLogMemorySnapshot_("start-pre", mode_label);
  CalLogLiveRetainedResources_(mode_label);
  CalConsoleOpUnlock_();
  return ESP_OK;
}

static esp_err_t
CalConsoleOpArmCaptureWhileLive(
  double actual_temp_c,
  double stable_stddev_c,
  bool drift_limit_enabled,
  double drift_limit_c_per_min,
  calibration_drift_limit_source_t drift_limit_source,
  int min_seconds,
  int timeout_seconds,
  bool* replaced_out)
{
  if (replaced_out != NULL) {
    *replaced_out = false;
  }
  if (!CalConsoleOpLock_(pdMS_TO_TICKS(100))) {
    return ESP_ERR_INVALID_STATE;
  }
  if (g_cal_console_op.mode != CAL_CONSOLE_OP_LIVE) {
    CalConsoleOpUnlock_();
    return ESP_ERR_INVALID_STATE;
  }
  if (replaced_out != NULL) {
    *replaced_out = g_cal_console_op.capture_armed;
  }
  g_cal_console_op.capture_actual_temp_c = actual_temp_c;
  g_cal_console_op.capture_stable_stddev_c = stable_stddev_c;
  g_cal_console_op.capture_drift_limit_enabled = drift_limit_enabled;
  g_cal_console_op.capture_drift_limit_c_per_min = drift_limit_c_per_min;
  g_cal_console_op.capture_drift_limit_source = drift_limit_source;
  g_cal_console_op.capture_min_seconds = min_seconds;
  g_cal_console_op.capture_timeout_seconds = timeout_seconds;
  g_cal_console_op.capture_armed = true;
  g_cal_console_op.capture_armed_start_us = esp_timer_get_time();
  CalConsoleOpUnlock_();
  return ESP_OK;
}

static esp_err_t
CalConsoleOpStartCapture(double actual_temp_c,
                         double stable_stddev_c,
                         bool drift_limit_enabled,
                         double drift_limit_c_per_min,
                         calibration_drift_limit_source_t drift_limit_source,
                         int min_seconds,
                         int timeout_seconds)
{
  if (!CalConsoleOpLock_(pdMS_TO_TICKS(100))) {
    return ESP_ERR_INVALID_STATE;
  }
  if (g_cal_console_op.mode != CAL_CONSOLE_OP_NONE) {
    CalConsoleOpUnlock_();
    return ESP_ERR_INVALID_STATE;
  }
  g_cal_console_op.mode = CAL_CONSOLE_OP_CAPTURE;
  g_cal_console_op.task_handle = NULL;
  g_cal_console_op.cancel_requested = false;
  g_cal_console_op.print_every_ms = 1000;
  g_cal_console_op.live_seconds = 0;
  g_cal_console_op.capture_actual_temp_c = actual_temp_c;
  g_cal_console_op.capture_stable_stddev_c = stable_stddev_c;
  g_cal_console_op.capture_drift_limit_enabled = drift_limit_enabled;
  g_cal_console_op.capture_drift_limit_c_per_min = drift_limit_c_per_min;
  g_cal_console_op.capture_drift_limit_source = drift_limit_source;
  g_cal_console_op.capture_min_seconds = min_seconds;
  g_cal_console_op.capture_timeout_seconds = timeout_seconds;
  g_cal_console_op.capture_armed = true;
  g_cal_console_op.capture_armed_start_us = esp_timer_get_time();
  g_cal_console_op.live_drift_notify_armed = false;
  g_cal_console_op.live_drift_notify_threshold_c_per_min = 0.0;
  g_cal_console_op.live_output_mode = CAL_CONSOLE_LIVE_OUTPUT_RAW;
  g_cal_console_op.live_drift_under_start_us = -1;
  g_cal_console_op.live_drift_notify_sent = false;
  g_cal_console_op.start_us = esp_timer_get_time();
  g_cal_console_op.last_sample_count = 0;
  g_cal_console_op.start_internal_free =
    heap_caps_get_free_size(MALLOC_CAP_INTERNAL | MALLOC_CAP_8BIT);
  g_cal_console_op.start_internal_largest =
    heap_caps_get_largest_free_block(MALLOC_CAP_INTERNAL | MALLOC_CAP_8BIT);
  g_cal_console_op.start_psram_free =
    heap_caps_get_free_size(MALLOC_CAP_SPIRAM | MALLOC_CAP_8BIT);
  g_cal_console_op.start_psram_largest =
    heap_caps_get_largest_free_block(MALLOC_CAP_SPIRAM | MALLOC_CAP_8BIT);
  g_cal_console_op.low_internal_free = g_cal_console_op.start_internal_free;
  g_cal_console_op.low_internal_largest =
    g_cal_console_op.start_internal_largest;
  g_cal_console_op.min_stack_free_bytes = UINT32_MAX;
  g_cal_console_op.max_temp_buffer_bytes = 0u;
  g_cal_runtime_last_sample_id = 0u;
  if (!CalHistoryEnsureStorage_()) {
    g_cal_console_op.mode = CAL_CONSOLE_OP_NONE;
    g_cal_console_op.task_handle = NULL;
    CalConsoleOpUnlock_();
    printf("cal capture: requires PSRAM-backed metric history\n");
    return ESP_ERR_NO_MEM;
  }
  BaseType_t created = xTaskCreate(&CalConsoleOpTask,
                                   "cal_op",
                                   kCalOpTaskStackBytes,
                                   NULL,
                                   2,
                                   &g_cal_console_op.task_handle);
  if (created != pdPASS) {
    g_cal_console_op.mode = CAL_CONSOLE_OP_NONE;
    g_cal_console_op.task_handle = NULL;
    CalConsoleOpUnlock_();
    return ESP_ERR_NO_MEM;
  }
  CalLogMemorySnapshot_("start-pre", "cal capture");
  CalLogLiveRetainedResources_("cal capture");
  CalConsoleOpUnlock_();
  return ESP_OK;
}

static void
CalConsoleOpRequestCancel(void)
{
  if (!CalConsoleOpLock_(pdMS_TO_TICKS(50))) {
    return;
  }
  if (g_cal_console_op.mode != CAL_CONSOLE_OP_NONE) {
    g_cal_console_op.cancel_requested = true;
  }
  CalConsoleOpUnlock_();
}

static void
PrintCalWindowLine_(const char* prefix,
                    const char* timestamp_utc,
                    size_t sample_count,
                    int32_t last_raw_mC,
                    int32_t last_raw_mOhm,
                    int32_t mean_raw_mC,
                    int32_t stddev_mC,
                    double drift_c_per_min,
                    double delta_c,
                    bool drift_target_enabled,
                    const char* drift_eta_to_target_text)
{
  if (prefix == NULL) {
    return;
  }
  const char* ts_text = (timestamp_utc != NULL) ? timestamp_utc : "n/a";
  const char* eta_text =
    (drift_eta_to_target_text != NULL) ? drift_eta_to_target_text : "n/a";
  if (drift_target_enabled) {
    printf("%s: ts=%s n=%u last=%.3fC last_ohm=%.3f mean=%.3fC std=%.3fC "
           "drift=%.3fC/min delta=%.3fC drift_eta_to_target=%s\n",
           prefix,
           ts_text,
           (unsigned)sample_count,
           last_raw_mC / 1000.0,
           last_raw_mOhm / 1000.0,
           mean_raw_mC / 1000.0,
           stddev_mC / 1000.0,
           drift_c_per_min,
           delta_c,
           eta_text);
    return;
  }

  printf("%s: ts=%s n=%u last=%.3fC last_ohm=%.3f mean=%.3fC std=%.3fC "
         "drift=%.3fC/min delta=%.3fC\n",
         prefix,
         ts_text,
         (unsigned)sample_count,
         last_raw_mC / 1000.0,
         last_raw_mOhm / 1000.0,
         mean_raw_mC / 1000.0,
         stddev_mC / 1000.0,
         drift_c_per_min,
         delta_c);
}

static void
PrintCalWindowCalibratedLine_(const char* timestamp_utc,
                              size_t sample_count,
                              int32_t last_raw_mOhm,
                              int32_t mean_raw_mOhm,
                              int32_t stddev_mOhm,
                              double calibrated_temp_c,
                              double mean_calibrated_temp_c,
                              double stddev_calibrated_temp_c,
                              double drift_c_per_min,
                              double delta_c,
                              uint8_t fault_status)
{
  char fault_desc[64] = { 0 };
  Max31865FormatFault(fault_status, fault_desc, sizeof(fault_desc));
  printf("cal livecal: ts=%s n=%u raw_ohm=%.3f std_ohm=%.3f mean_ohm=%.3f "
         "cal_temp=%.3fC std_temp=%.3fC mean_temp=%.3fC drift=%.3fC/min "
         "delta=%.3fC fault=%s (0x%02X)\n",
         (timestamp_utc != NULL) ? timestamp_utc : "n/a",
         (unsigned)sample_count,
         last_raw_mOhm / 1000.0,
         stddev_mOhm / 1000.0,
         mean_raw_mOhm / 1000.0,
         calibrated_temp_c,
         stddev_calibrated_temp_c,
         mean_calibrated_temp_c,
         drift_c_per_min,
         delta_c,
         fault_desc,
         (unsigned)fault_status);
}

static void
PrintCalCaptureWindowLine_(double elapsed_s,
                           size_t sample_count,
                           int32_t last_raw_mC,
                           int32_t last_raw_mOhm,
                           int32_t mean_raw_mC,
                           double stddev_c,
                           double drift_c_per_min,
                           double delta_c,
                           double stable_elapsed_s,
                           int min_seconds,
                           double stable_stddev_c,
                           bool drift_limit_enabled,
                           double drift_limit_c_per_min,
                           calibration_drift_limit_source_t drift_limit_source,
                           double actual_temp_c)
{
  const char* drift_source = DriftLimitSourceToString_(drift_limit_source);
  char drift_limit_buf[40] = { 0 };
  if (drift_limit_enabled) {
    snprintf(drift_limit_buf,
             sizeof(drift_limit_buf),
             "%.3fC/min(%s)",
             drift_limit_c_per_min,
             drift_source);
  } else {
    snprintf(drift_limit_buf, sizeof(drift_limit_buf), "disabled");
  }
  if (sample_count == 0u) {
    printf("cal capture: t=%.1fs n=%u last=n/a last_ohm=n/a mean=%.3fC "
           "std=%.3fC drift=%.3fC/min delta=%.3fC stable=%.1f/%ds thr=%.3fC "
           "drift_thr=%s actual=%.3fC\n",
           elapsed_s,
           (unsigned)sample_count,
           mean_raw_mC / 1000.0,
           stddev_c,
           drift_c_per_min,
           delta_c,
           stable_elapsed_s,
           min_seconds,
           stable_stddev_c,
           drift_limit_buf,
           actual_temp_c);
    return;
  }

  printf("cal capture: t=%.1fs n=%u last=%.3fC last_ohm=%.3f mean=%.3fC "
         "std=%.3fC drift=%.3fC/min delta=%.3fC stable=%.1f/%ds thr=%.3fC "
         "drift_thr=%s actual=%.3fC\n",
         elapsed_s,
         (unsigned)sample_count,
         last_raw_mC / 1000.0,
         last_raw_mOhm / 1000.0,
         mean_raw_mC / 1000.0,
         stddev_c,
         drift_c_per_min,
         delta_c,
         stable_elapsed_s,
         min_seconds,
         stable_stddev_c,
         drift_limit_buf,
         actual_temp_c);
}

static const char*
DriftLimitSourceToString_(calibration_drift_limit_source_t source)
{
  switch (source) {
    case CAL_DRIFT_LIMIT_SOURCE_DEFAULT:
      return "DEFAULT";
    case CAL_DRIFT_LIMIT_SOURCE_USER:
      return "USER";
    case CAL_DRIFT_LIMIT_SOURCE_DISABLED:
      return "DISABLED";
    case CAL_DRIFT_LIMIT_SOURCE_LEGACY_UNAVAILABLE:
      return "LEGACY_UNAVAILABLE";
    default:
      return "UNKNOWN";
  }
}

static const char*
FindOptionValue_(int argc, char** argv, const char* name)
{
  if (argv == NULL || name == NULL) {
    return NULL;
  }
  const size_t name_len = strlen(name);
  for (int i = 2; i < argc; ++i) {
    const char* arg = argv[i];
    if (arg == NULL || strncmp(arg, "--", 2) != 0) {
      continue;
    }
    const char* option = arg + 2;
    if (strncmp(option, name, name_len) != 0) {
      continue;
    }
    if (option[name_len] == '=') {
      return option + name_len + 1;
    }
    if (option[name_len] == '\0') {
      if (i + 1 < argc) {
        return argv[i + 1];
      }
      return NULL;
    }
  }
  return NULL;
}

static bool
OptionPresent_(int argc, char** argv, const char* name)
{
  if (argv == NULL || name == NULL) {
    return false;
  }
  const size_t name_len = strlen(name);
  for (int i = 2; i < argc; ++i) {
    const char* arg = argv[i];
    if (arg == NULL || strncmp(arg, "--", 2) != 0) {
      continue;
    }
    const char* option = arg + 2;
    if (strncmp(option, name, name_len) != 0) {
      continue;
    }
    if (option[name_len] == '\0' || option[name_len] == '=') {
      return true;
    }
  }
  return false;
}

static bool
ParseOptionInt_(int argc, char** argv, const char* name, int* value_out)
{
  if (value_out == NULL) {
    return false;
  }
  const char* value = FindOptionValue_(argc, argv, name);
  if (value == NULL) {
    return false;
  }
  char* end = NULL;
  long parsed = strtol(value, &end, 10);
  if (end == value || *end != '\0' || parsed < INT_MIN || parsed > INT_MAX) {
    return false;
  }
  *value_out = (int)parsed;
  return true;
}

static bool
NextCalibrationImportTokenSpan_(const char* line_start,
                                size_t line_len,
                                size_t* cursor_inout,
                                const char** token_start_out,
                                size_t* token_len_out)
{
  if (line_start == NULL || cursor_inout == NULL || token_start_out == NULL ||
      token_len_out == NULL) {
    return false;
  }

  size_t cursor = *cursor_inout;
  while (cursor < line_len && isspace((unsigned char)line_start[cursor])) {
    cursor++;
  }
  if (cursor >= line_len) {
    *cursor_inout = cursor;
    return false;
  }

  const char* token_start = line_start + cursor;
  while (cursor < line_len && !isspace((unsigned char)line_start[cursor])) {
    cursor++;
  }

  *token_start_out = token_start;
  *token_len_out = (size_t)((line_start + cursor) - token_start);
  *cursor_inout = cursor;
  return true;
}
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
