rasusmilch/PT100_Mesh_Datalogger/main/runtime_manager.c

#include "runtime_manager.h"

#include <errno.h>
#include <inttypes.h>
#include <math.h>
#include <stdalign.h>
#include <stdio.h>
#include <stdlib.h>
#include <string.h>
#include <time.h>

#include "alerts/alert_manager.h"
#include "app_net_config.h"
#include "calibration.h"
#include "data_csv.h"
#include "data_port.h"
#include "display_attention.h"
#include "esp_app_desc.h"
#include "esp_attr.h"
#include "esp_heap_caps.h"
#include "esp_idf_version.h"
#include "esp_log.h"
#include "esp_mac.h"
#include "esp_mesh_lite.h"
#include "esp_mesh_lite_port.h"
#include "esp_system.h"
#include "esp_timer.h"
#include "fram_error_log.h"
#include "fram_i2c.h"
#include "fram_layout.h"
#include "fram_log.h"
#include "freertos/FreeRTOS.h"
#include "freertos/queue.h"
#include "freertos/semphr.h"
#include "freertos/task.h"
#include "gpio_buttons.h"
#include "heap_event_log.h"
#include "heap_monitor.h"
#include "heap_phase_log.h"
#include "i2c_bus.h"
#include "log_rate_limit.h"
#include "max31865_reader.h"
#include "max7219_display.h"
#include "mem_guard.h"
#include "mem_pool.h"
#include "mesh_transport.h"
#include "mqtt_client_wrap.h"
#include "net_supervisor.h"
#include "ptlog_format.h"
#include "run_gpio.h"
#include "runtime_health.h"
#include "runtime_health_publisher.h"
#include "runtime_markers.h"
#include "runtime_state.h"
#include "sd_logger.h"
#include "sdkconfig.h"
#include "stack_monitor.h"
#include "time_civil.h"
#include "time_sync.h"
#include "units_gpio.h"
#include "wifi_credentials.h"
#include "wifi_manager.h"
#include "wifi_service.h"

static const char* kTag = "runtime";

// String used to represent "no holder" for mutex/I2C operation state.
// This must be a compile-time constant so it can be used in static
// initializers.
static const char kMutexHolderNone[] = "<none>";

static const uint32_t kSdFlushMaxRecordsPerPass = 100;
static const uint32_t kSdFlushMaxMsPerPass = 50;
static const uint32_t kSdFlushTimeSliceMs = 50;
static const uint32_t kSdFlushWarnIntervalMs = 10000;
static const uint32_t kFramLogLockWarnIntervalMs = 10000;
static const uint32_t kI2cTimeoutWarnIntervalMs = 5000;
static const uint32_t kI2cLockDumpIntervalMs = 60000;
static const uint32_t kI2cHangWarnMs = 2000;
static const uint32_t kI2cHangRestartMs = 8000;
static const uint32_t kSdFlushFailureBackoffMs = 5000;
static const uint32_t kSdFlushFailureBackoffMaxMs = 300000;
static const uint32_t kSdFlushMinIntervalMs = 200;
static const uint32_t kSdDetectPollIntervalMs = 250;
static const uint32_t kExportQueueDepth = 64;
static const uint32_t kExportOutboxDepth = CONFIG_APP_EXPORT_OUTBOX_DEPTH;
static const uint32_t kSdIoErrorSetThreshold = 2;
static const uint32_t kSdIoErrorClearThreshold = 2;
static const uint32_t kFramOverrunActiveSetThreshold = 2;
static const uint32_t kFramOverrunActiveClearThreshold = 2;
static const int64_t kCalTimeStableDelaySec = 60;
static const uint32_t kBrokerOutboxDepth = CONFIG_APP_BROKER_OUTBOX_DEPTH;
static const uint32_t kExportLogRateLimitMs = CONFIG_APP_EXPORT_RATE_LIMIT_MS;
static const uint32_t kAlertHttpSendFailLogRateLimitMs = 60000;
static const uint32_t kAlertHttpRetryDelayMs = 1000;
static const uint32_t kAlertHttpMaxAttempts = 3;
static const TickType_t kSdIoLockTimeoutTicks = pdMS_TO_TICKS(2000);
static const TickType_t kSensorSpiBusLockTimeoutTicks = pdMS_TO_TICKS(20);
static const TickType_t kFramLogLockTimeoutTicks = pdMS_TO_TICKS(2000);
static const TickType_t kI2cIoLockTimeoutTicks = pdMS_TO_TICKS(150);
static const TickType_t kI2cRecoveryLockTimeoutTicks = pdMS_TO_TICKS(2000);
static const uint32_t kSensorSpiInvalidStreakThreshold = 3;
static const uint32_t kSensorSpiReinitAlertThreshold = 2;
static const int64_t kSensorSpiReinitWindowMs = 60000;
static const int64_t kSensorSpiStableResolveMs = 30000;
static const uint16_t kErrlogSensorSpiFault = 17;
static const int32_t kStopDrainHardMaxDefaultMs = 15000;
static const int64_t kNetTxStallDropMs = 30000;
static const uint32_t kI2cRecoveryTriggerCount = 3;
static const int64_t kFramRetryIntervalMs = 30000;
static const uint32_t kFramInvalidHeapLogEvery = 10;
static const uint32_t kDeferredDropWarnIntervalMs = 60000;
static const uint32_t kFramSuppressedWarnIntervalMs = 10000;
static const uint32_t kRebootAlertLatchMagic = 0x5254424C;
static const uint16_t kRebootAlertLatchVersion = 2;
static const uint32_t kRtcErrlogLatchMagic = 0x5245434C;
static const uint16_t kRtcErrlogLatchVersion = 1;
static const uint32_t kRebootAlertWifiWaitMs = 2500;
static const uint32_t kRebootAlertHttpTimeoutMs = 1500;
static const uint32_t kRebootAlertResolveDelayMs = 5000;
static const uint32_t kRebootAlertResolveCheckIntervalMs = 1000;
static const uint32_t kSafeHoldMaxMs = 120000;
static const uint32_t kSafeHoldMinRetryMs = 2000;
static const uint32_t kSafeHoldMaxRetryMs = 60000;
static const uint32_t kSafeHoldLogIntervalMs = 5000;
static const uint32_t kRtdFaultNtfyBatchHoldoffMs = 30000;
static const uint32_t kRtdFaultNtfyMinResendIntervalMs = 300000;
static const uint32_t kRtdFaultNtfyPendingThreshold = 5;
static const uint32_t kStorageStallThresholdMs =
  CONFIG_APP_ALERT_STORAGE_STALL_MS;
static char g_sd_csv_line_buffer[CONFIG_APP_MAX_CSV_LINE_BYTES];
static stack_monitor_t g_stack_monitor;
static runtime_state_t g_state;
static app_runtime_t g_runtime;
static runtime_sensor_sample_t g_runtime_sensor_sample;
static bool g_alert_http_psram_failure_logged = false;
static RTC_DATA_ATTR runtime_reboot_alert_latch_t g_reboot_alert_latch = {
  .magic = kRebootAlertLatchMagic,
  .version = kRebootAlertLatchVersion,
};
static RTC_DATA_ATTR runtime_rtc_errlog_latch_t g_rtc_errlog_latch;

enum
{
  SD_FLUSH_TRIGGER_WATERMARK = 1u << 0,
  SD_FLUSH_TRIGGER_PERIODIC = 1u << 1,
  SD_FLUSH_TRIGGER_BACKLOG = 1u << 2,
  SD_FLUSH_TRIGGER_RETRY = 1u << 3,
  SD_FLUSH_TRIGGER_MORE_PENDING = 1u << 4,
  SD_FLUSH_TRIGGER_MANUAL = 1u << 5,
};

typedef struct
{
  bool active;
  const char* op_name;
  uint32_t address;
  size_t length;
  TickType_t start_ticks;
  const char* caller;
} runtime_i2c_op_state_t;

static portMUX_TYPE g_i2c_op_lock = portMUX_INITIALIZER_UNLOCKED;
static portMUX_TYPE g_rtc_errlog_latch_lock = portMUX_INITIALIZER_UNLOCKED;
static portMUX_TYPE g_runtime_sensor_sample_lock = portMUX_INITIALIZER_UNLOCKED;
static runtime_i2c_op_state_t g_i2c_op_state = {
  .active = false,
  .op_name = kMutexHolderNone,
  .address = 0,
  .length = 0,
  .start_ticks = 0,
  .caller = kMutexHolderNone,
};

enum
{
  ERROR_FRAM_IO_FAIL = 100,
  ERROR_I2C_RECOVERY_START = 101,
  ERROR_I2C_RECOVERY_SUCCESS = 102,
  ERROR_I2C_RECOVERY_FAILED = 103,
  ERROR_I2C_HANG_RESTART = 104,
};

enum
{
  SPI_PAUSE_ACK_SENSOR = 1u << 0,
  SPI_PAUSE_ACK_DISPLAY = 1u << 1,
};

static esp_err_t
InitSpiBus(spi_host_device_t host);

static esp_err_t
InitializeMax7219Display(runtime_state_t* state);

static void
UpdateCalibrationDueState(runtime_state_t* state,
                          bool time_valid,
                          int64_t now_utc);

static spi_host_device_t
GetSpiHost(void);

static esp_err_t
InitializeMax31865Sensor(runtime_state_t* state, spi_host_device_t spi_host);

static void
AlertHttpTask(void* context);

static void
RuntimeLogNtfyBodyLines(const char* label, const char* text);

static void
RuntimeLogNtfyJob(const alert_ntfy_job_t* job, const char* stage);

static void
AppendStopStorageSummaryLine(runtime_state_t* state, alert_ntfy_job_t* job);

static void
RuntimeResetStorageStallTracking(runtime_state_t* state, int64_t now_ms);

static bool
RuntimeComputeStorageStallCondition(runtime_state_t* state, int64_t now_ms);

static bool
RuntimeRecoverI2cBus(runtime_state_t* state,
                     const char* reason,
                     esp_err_t last_error);

/**
 * @brief Compute effective sensor polling period for sampling/display updates.
 * @param settings Current app settings snapshot.
 * @return Effective polling period in milliseconds.
 */
static uint32_t
RuntimeEffectiveSensorPollPeriodMs(const app_settings_t* settings);

/**
 * @brief Request net_tx + alert_http pause state and wait for acknowledgements.
 * @param state Runtime state.
 * @param pause_enabled True to request pause, false to resume.
 * @param timeout_ms Maximum wait for acknowledgement.
 */
static void
RuntimeRequestNetPause(runtime_state_t* state,
                       bool pause_enabled,
                       uint32_t timeout_ms);

/**
 * @brief Create the alert_http task with a PSRAM-backed stack.
 * @param state Runtime state (owns the task memory).
 * @param stack_bytes Stack size in bytes.
 * @return pdPASS on success, or pdFAIL on failure.
 */
static BaseType_t
CreateAlertHttpTaskWithPsrStack(runtime_state_t* state, uint32_t stack_bytes);

static void
RootRecordRxCallback(const pt100_mesh_addr_t* from,
                     const log_record_t* record,
                     void* context);
static void
RootPublishRecordRxCallback(const uint8_t src_mac[6],
                            const log_record_t* record,
                            void* context);

static uint64_t
PackMacToLeafId(const uint8_t mac[6]);

static sd_append_verify_t
ResolveSdVerifyMode(const runtime_state_t* state);

static bool
RuntimeBuildPtlogHeaderInternal(const runtime_state_t* state,
                                int64_t epoch_utc,
                                ptlog_header_t* header_out,
                                uint32_t* signature_out);

static bool
RuntimeCalibrationApplied(const runtime_state_t* state);

static void
FormatUtcTimestamp(int64_t epoch_utc, char* out, size_t out_size);

static bool
RuntimeFramLogLock(runtime_state_t* state, TickType_t timeout_ticks);

static void
RuntimeFramLogUnlock(runtime_state_t* state);

static bool
RuntimeVerifyFram(runtime_state_t* state);

static void
UpdateDebouncedRtdFault(runtime_state_t* state,
                        const app_settings_t* settings,
                        bool raw_fault_present,
                        bool sd_flush_busy,
                        int64_t now_ms,
                        uint8_t raw_fault_status);

/**
 * @brief Perform one MAX31865 one-shot conversion/read cycle.
 * @param state Runtime state owning the MAX31865 reader.
 * @param sample_out Output sample buffer.
 * @param one_shot_out Optional one-shot state snapshot for diagnostics.
 * @return ESP_OK on read completion, or an ESP_ERR_* code on failure.
 */
static esp_err_t
RuntimePerformSingleMax31865Read(runtime_state_t* state,
                                 max31865_sample_t* sample_out,
                                 max31865_one_shot_state_t* one_shot_out);

/**
 * @brief Perform MAX31865 one-shot read with immediate fault confirmation
 * retry.
 * @param state Runtime state owning counters and MAX31865 reader.
 * @param sample_out Authoritative sample for this sensor loop.
 * @param used_retry_out True when a same-loop retry was attempted.
 * @param retry_faulted_out True when retry completed with a faulted sample.
 * @param first_fault_status_out Fault status from the first read fault.
 * @param retry_fault_status_out Fault status from the retry read, if any.
 * @param retry_result_out Retry read result (ESP_OK or hard error).
 * @return Result of the authoritative sample path.
 */
static esp_err_t
RuntimePerformMax31865ReadWithFaultRetry(runtime_state_t* state,
                                         max31865_sample_t* sample_out,
                                         bool* used_retry_out,
                                         bool* retry_faulted_out,
                                         uint8_t* first_fault_status_out,
                                         uint8_t* retry_fault_status_out,
                                         esp_err_t* retry_result_out);

/**
 * @brief Accumulate RTD retry diagnostics for rate-limited ntfy summary jobs.
 */
static void
RuntimeAccumulateRtdFaultNtfy(runtime_state_t* state,
                              bool first_fault,
                              bool retry_fault,
                              bool retry_clean,
                              uint8_t first_status,
                              uint8_t retry_status,
                              esp_err_t retry_err,
                              int64_t now_ms);

/**
 * @brief Check whether pending RTD retry diagnostics should be sent now.
 */
static bool
RuntimeShouldSendRtdFaultNtfy(const runtime_state_t* state, int64_t now_ms);

/**
 * @brief Build a custom ntfy summary job from pending RTD retry diagnostics.
 */
static bool
RuntimeBuildRtdFaultSummaryNtfyJob(runtime_state_t* state,
                                   int64_t now_ms,
                                   alert_ntfy_job_t* out_job);

/**
 * @brief Try to enqueue a pending RTD retry diagnostic ntfy summary job.
 */
static void
RuntimeMaybeSendRtdFaultSummaryNtfy(runtime_state_t* state, int64_t now_ms);

/**
 * @brief Apply EMA settings to a freshly captured RTD sample.
 * @param state Runtime state containing MAX31865 EMA storage.
 * @param ema_enabled True when EMA filtering is enabled.
 * @param alpha_permille EMA alpha in permille units [1, 1000].
 * @param sample Sample to fold into EMA state.
 * @param result Capture result associated with @p sample.
 */
static void
UpdateSensorEmaFromSample(runtime_state_t* state,
                          bool ema_enabled,
                          uint16_t alpha_permille,
                          const max31865_sample_t* sample,
                          esp_err_t result);

/**
 * @brief Publish latest runtime sensor snapshot from SensorTask.
 * @param sample Source MAX31865 sample.
 */
static void
RuntimePublishSensorSnapshot(const max31865_sample_t* sample);

static const char*
Max31865OneShotPhaseToString(max31865_one_shot_phase_t phase);

/**
 * @brief Execute RuntimeRecoverI2cBusCommon.
 * @param state Parameter state.
 * @param reason Parameter reason.
 * @param last_error Parameter last_error.
 * @param lock_held Parameter lock_held.
 * @return Return the function result.
 */
static bool
RuntimeRecoverI2cBusCommon(runtime_state_t* state,
                           const char* reason,
                           esp_err_t last_error,
                           bool lock_held);

static void
RuntimeRebootOnSdEioEscalation(runtime_state_t* state, const char* context);

/**
 * @brief Enqueue an ntfy job and optionally wait for AlertHttpTask completion.
 * @param state Runtime state.
 * @param job Ntfy job to enqueue.
 * @param wait_ms Maximum time to wait for send counters to change.
 * @param status_out Optional pointer receiving last HTTP status.
 * @param err_out Optional pointer receiving last esp_err_t.
 * @param retry_after_seconds_out Optional pointer receiving cooldown-derived
 * retry seconds.
 * @return Result indicating enqueue/wait/send outcome.
 */
static alert_ntfy_result_t
RuntimeEnqueueNtfyJobAndWait(runtime_state_t* state,
                             const alert_ntfy_job_t* job,
                             uint32_t wait_ms,
                             int* status_out,
                             esp_err_t* err_out,
                             int* retry_after_seconds_out);

static void
RuntimeDumpLocks(runtime_state_t* state, const char* reason);

static void
RuntimeRecordError(runtime_state_t* state,
                   const char* module,
                   esp_err_t err,
                   const char* phase);

static bool
IsRecoverableI2cErr(esp_err_t err);

/**
 * @brief Execute DiscardFramRecordsWithYield.
 * @param state Parameter state.
 * @param records_to_discard Parameter records_to_discard.
 * @param fram_log_timeout_ticks Parameter fram_log_timeout_ticks.
 * @param timeout_counter Parameter timeout_counter.
 * @param last_log_ms Parameter last_log_ms.
 * @param context Parameter context.
 * @return Return the function result.
 */
static esp_err_t
DiscardFramRecordsWithYield(runtime_state_t* state,
                            uint32_t records_to_discard,
                            TickType_t fram_log_timeout_ticks,
                            uint32_t* timeout_counter,
                            uint32_t* last_log_ms,
                            const char* context);

static void
UpdateFramFillState(runtime_state_t* state);

static void
UpdateCachedBool(runtime_state_t* state, bool* field, bool value);

static void
RuntimeLatchOperatorHold(runtime_state_t* state, uint32_t now_ms);

static void
RuntimeClearOperatorHold(runtime_state_t* state);

static void
UpdateCachedUint64(runtime_state_t* state, uint64_t* field, uint64_t value);

static bool
DeferredLogPush(runtime_state_t* state, const log_record_t* record);

static bool
DeferredLogPop(runtime_state_t* state, log_record_t* out);

static uint8_t
DeferredLogCount(runtime_state_t* state);

static uint32_t
DeferredLogDrops(runtime_state_t* state);

static void
DeferredLogReset(runtime_state_t* state);

static void
RuntimeBeginI2cQuiesce(runtime_state_t* state, const char* reason);

static void
RuntimeEndI2cQuiesce(runtime_state_t* state);

static esp_err_t
RuntimeDrainDeferredToFram(runtime_state_t* state, const char* context);

static void
RuntimeAssignFallbackRecordIds(runtime_state_t* state, log_record_t* record);

static void
RuntimeFramRetryTick(runtime_state_t* state, int64_t now_ms);

static void
RestoreTimeJumpBackPendingFromFram(runtime_state_t* state);

static esp_err_t
LogFramErrorEvent(runtime_state_t* state,
                  uint16_t code,
                  bool resolved,
                  int32_t detail0,
                  int32_t detail1);

static void
RuntimeRtcErrlogLatchInitIfNeeded(void);

static void
RuntimeRtcErrlogLatchPush(uint16_t code,
                          bool resolved,
                          int32_t detail0,
                          int32_t detail1,
                          uint32_t epoch_sec,
                          uint16_t millis);

static void
RuntimeRtcErrlogLatchFlushToFram(runtime_state_t* state);

static uint32_t
GetStackMonitorMinBytes(const char* name);

static void
LogDrainPreflight(const runtime_state_t* state, const char* reason);

static void
LogDrainPostflight(const runtime_state_t* state,
                   const char* reason,
                   int32_t flushed_records,
                   int32_t remaining_records,
                   uint32_t duration_ms);

/**
 * @brief Build a printable SD flush trigger list.
 * @param trigger_flags Bitset of SD flush trigger flags.
 * @param buffer Destination buffer for the printable trigger list.
 * @param buffer_len Size of @p buffer in bytes.
 */
static void
SdFlushTriggerFlagsToString(uint32_t trigger_flags,
                            char* buffer,
                            size_t buffer_len);

/**
 * @brief Start an SD flush session if one is not active.
 * @param state Runtime state.
 */
static void
SdFlushMaybeStartSession(runtime_state_t* state);

/**
 * @brief Log end-of-session drain metrics.
 * @param state Runtime state.
 * @param records_flushed Number of records flushed in the session.
 * @param duration_ms Session duration in milliseconds.
 */
static void
SdFlushLogSessionEnd(runtime_state_t* state,
                     uint32_t records_flushed,
                     uint32_t duration_ms);

static uint32_t
RuntimeI2cLockHeldMsNoLock(const runtime_state_t* state);

static void
RuntimeDumpI2cLockState(runtime_state_t* state, const char* reason);

static void
RuntimeI2cOpBegin(const char* op_name,
                  uint32_t address,
                  size_t length,
                  const char* caller);

static void
RuntimeI2cOpEnd(void);

static void
RuntimeDumpI2cOpState(const runtime_state_t* state, const char* reason);

static bool
ReadFramBufferedRecords(runtime_state_t* state, uint32_t* buffered_out);

static void
RuntimeNotifyTask(TaskHandle_t handle)
{
  if (handle == NULL) {
    return;
  }
  xTaskNotifyGive(handle);
}

static bool
RuntimeFramLogLockWithWarn(runtime_state_t* state,
                           TickType_t timeout_ticks,
                           uint32_t* timeout_counter,
                           uint32_t* last_log_ms,
                           const char* context)
{
  if (RuntimeFramLogLock(state, timeout_ticks)) {
    return true;
  }
  if (timeout_counter != NULL) {
    (*timeout_counter)++;
  }
  if (LogRateLimitAllow(last_log_ms, kFramLogLockWarnIntervalMs)) {
    ESP_LOGW(kTag, "FRAM log lock timeout in %s", context);
    RuntimeDumpI2cLockState(state, "fram_log_lock_timeout");
    RuntimeDumpI2cOpState(state, "fram_log_lock_timeout");
    I2cBusLogState(&state->i2c_bus, "fram_log_lock_timeout");
  }
  return false;
}

static void
RegisterStackMonitorTask(const char* name,
                         TaskHandle_t* handle_ptr,
                         uint32_t stack_alloc_bytes)
{
  if (!StackMonitorRegister(
        &g_stack_monitor, name, handle_ptr, stack_alloc_bytes)) {
    ESP_LOGW(kTag, "Stack monitor registration failed; skipping %s", name);
  }
}

/**
 * @brief Update EMA state with an already-read MAX31865 sample.
 * @param state Runtime state containing sensor EMA fields.
 * @param ema_enabled True when EMA filtering is enabled.
 * @param alpha_permille EMA alpha in permille units [1, 1000].
 * @param sample Sample captured in the current sensor loop iteration.
 * @param result Capture status associated with @p sample.
 */
static void
UpdateSensorEmaFromSample(runtime_state_t* state,
                          bool ema_enabled,
                          uint16_t alpha_permille,
                          const max31865_sample_t* sample,
                          esp_err_t result)
{
  if (state == NULL || sample == NULL || !ema_enabled || result != ESP_OK) {
    return;
  }

  const double alpha = (double)alpha_permille / 1000.0;
  (void)Max31865ApplyEmaSample(&state->sensor, alpha, sample, NULL);
}

static void
RuntimePublishSensorSnapshot(const max31865_sample_t* sample)
{
  if (sample == NULL) {
    return;
  }

  taskENTER_CRITICAL(&g_runtime_sensor_sample_lock);
  g_runtime_sensor_sample.timestamp_us = esp_timer_get_time();
  g_runtime_sensor_sample.temp_mC =
    (int32_t)llround(sample->temperature_c * 1000.0);
  g_runtime_sensor_sample.ohm_mohm =
    (int32_t)llround(sample->resistance_ohm * 1000.0);
  g_runtime_sensor_sample.fault = sample->fault_status;
  g_runtime_sensor_sample.valid = !sample->fault_present;
  g_runtime_sensor_sample.sample_id++;
  taskEXIT_CRITICAL(&g_runtime_sensor_sample_lock);
}

static const char*
Max31865OneShotPhaseToString(max31865_one_shot_phase_t phase)
{
  switch (phase) {
    case kMax31865OneShotIdle:
      return "Idle";
    case kMax31865OneShotBiasSettling:
      return "BiasSettling";
    case kMax31865OneShotConverting:
      return "Converting";
    default:
      return "Unknown";
  }
}

static uint32_t
GetStackMonitorMinBytes(const char* name)
{
  uint32_t min_bytes = 0;
  if (!StackMonitorGetMinFreeBytes(&g_stack_monitor, name, &min_bytes)) {
    return 0;
  }
  return min_bytes;
}

static const char*
RuntimeGetCurrentTaskName(void)
{
  if (xTaskGetSchedulerState() != taskSCHEDULER_RUNNING) {
    return "scheduler-not-started";
  }
  const char* name = pcTaskGetName(NULL);
  return (name != NULL) ? name : "unknown";
}

static uint32_t
RuntimeElapsedMs(TickType_t start_ticks, TickType_t now_ticks)
{
  if (start_ticks == 0) {
    return 0;
  }
  return (uint32_t)pdTICKS_TO_MS(now_ticks - start_ticks);
}

static void
RuntimeUpdateHoldMax(uint32_t hold_ms, uint32_t* max_observed_ms)
{
  if (max_observed_ms == NULL) {
    return;
  }
  if (hold_ms > *max_observed_ms) {
    *max_observed_ms = hold_ms;
  }
}

static void
RuntimeRecordError(runtime_state_t* state,
                   const char* module,
                   esp_err_t err,
                   const char* phase)
{
  if (state == NULL) {
    return;
  }
  runtime_error_entry_t* entry = &state->error_ring[state->error_ring_head];
  entry->uptime_ms = (uint32_t)(esp_timer_get_time() / 1000);
  entry->module = (module != NULL) ? module : "unknown";
  entry->err = err;
  entry->phase = (phase != NULL) ? phase : kMutexHolderNone;

  state->error_ring_head =
    (uint8_t)((state->error_ring_head + 1u) % RUNTIME_ERROR_RING_SIZE);
  if (state->error_ring_count < RUNTIME_ERROR_RING_SIZE) {
    state->error_ring_count++;
  }
}

/**
 * @brief Return I2C lock hold duration without taking locks.
 * @param state Parameter state.
 * @return Return the function result.
 */
static uint32_t
RuntimeI2cLockHeldMsNoLock(const runtime_state_t* state)
{
  if (state == NULL) {
    return 0;
  }
  if (state->i2c_mutex_holder == kMutexHolderNone ||
      state->i2c_mutex_hold_start_ticks == 0) {
    return 0;
  }
  return RuntimeElapsedMs(state->i2c_mutex_hold_start_ticks,
                          xTaskGetTickCount());
}

/**
 * @brief Log I2C lock state for debugging.
 * @param state Parameter state.
 * @param reason Parameter reason.
 */
static void
RuntimeDumpI2cLockState(runtime_state_t* state, const char* reason)
{
  if (state == NULL) {
    return;
  }
  const TickType_t now_ticks = xTaskGetTickCount();
  const char* holder = (state->i2c_mutex_holder != NULL)
                         ? state->i2c_mutex_holder
                         : kMutexHolderNone;
  const uint32_t held_ms =
    (holder != kMutexHolderNone)
      ? RuntimeElapsedMs(state->i2c_mutex_hold_start_ticks, now_ticks)
      : 0u;
  const char* phase =
    (state->sd_flush_phase != NULL) ? state->sd_flush_phase : kMutexHolderNone;
  const char* reason_label = (reason != NULL) ? reason : "unknown";
  ESP_LOGW(kTag,
           "I2C lock (%s): holder=%s held_ms=%" PRIu32 " timeouts=%" PRIu32
           " max_ms=%" PRIu32 " sd_phase=%s last_err=%s (%d)",
           reason_label,
           holder,
           held_ms,
           state->i2c_mutex_timeouts,
           state->i2c_mutex_hold_max_ms_observed,
           phase,
           esp_err_to_name(state->sd_flush_last_err),
           (int)state->sd_flush_last_err);
}

/**
 * @brief Begin tracking an I2C operation.
 * @param op_name Parameter op_name.
 * @param address Parameter address.
 * @param length Parameter length.
 * @param caller Parameter caller.
 */
static void
RuntimeI2cOpBegin(const char* op_name,
                  uint32_t address,
                  size_t length,
                  const char* caller)
{
  taskENTER_CRITICAL(&g_i2c_op_lock);
  g_i2c_op_state.active = true;
  g_i2c_op_state.op_name = (op_name != NULL) ? op_name : kMutexHolderNone;
  g_i2c_op_state.address = address;
  g_i2c_op_state.length = length;
  g_i2c_op_state.start_ticks = xTaskGetTickCount();
  g_i2c_op_state.caller = (caller != NULL) ? caller : kMutexHolderNone;
  taskEXIT_CRITICAL(&g_i2c_op_lock);
}

/**
 * @brief End tracking an I2C operation.
 */
static void
RuntimeI2cOpEnd(void)
{
  taskENTER_CRITICAL(&g_i2c_op_lock);
  g_i2c_op_state.active = false;
  g_i2c_op_state.op_name = kMutexHolderNone;
  g_i2c_op_state.address = 0;
  g_i2c_op_state.length = 0;
  g_i2c_op_state.start_ticks = 0;
  g_i2c_op_state.caller = kMutexHolderNone;
  taskEXIT_CRITICAL(&g_i2c_op_lock);
}

/**
 * @brief Log current I2C operation state.
 * @param state Parameter state.
 * @param reason Parameter reason.
 */
static void
RuntimeDumpI2cOpState(const runtime_state_t* state, const char* reason)
{
  runtime_i2c_op_state_t snapshot;
  taskENTER_CRITICAL(&g_i2c_op_lock);
  snapshot = g_i2c_op_state;
  taskEXIT_CRITICAL(&g_i2c_op_lock);

  const TickType_t now_ticks = xTaskGetTickCount();
  const char* holder = kMutexHolderNone;
  const uint32_t held_ms =
    (state != NULL && state->i2c_mutex_holder != NULL &&
     state->i2c_mutex_holder != kMutexHolderNone)
      ? RuntimeElapsedMs(state->i2c_mutex_hold_start_ticks, now_ticks)
      : 0u;
  if (state != NULL) {
    holder = (state->i2c_mutex_holder != NULL) ? state->i2c_mutex_holder
                                               : kMutexHolderNone;
  }
  const char* phase = (state != NULL && state->sd_flush_phase != NULL)
                        ? state->sd_flush_phase
                        : kMutexHolderNone;
  const char* reason_label = (reason != NULL) ? reason : "unknown";
  const uint32_t op_ms = (snapshot.active && snapshot.start_ticks != 0)
                           ? RuntimeElapsedMs(snapshot.start_ticks, now_ticks)
                           : 0u;
  ESP_LOGW(kTag,
           "I2C op (%s): lock_holder=%s held_ms=%" PRIu32
           " op=%s addr=0x%08" PRIx32 " len=%zu op_ms=%" PRIu32
           " caller=%s sd_phase=%s last_err=%s (%d)",
           reason_label,
           holder,
           held_ms,
           snapshot.active ? snapshot.op_name : kMutexHolderNone,
           snapshot.address,
           snapshot.length,
           op_ms,
           snapshot.active ? snapshot.caller : kMutexHolderNone,
           phase,
           (state != NULL) ? esp_err_to_name(state->sd_flush_last_err)
                           : kMutexHolderNone,
           (state != NULL) ? (int)state->sd_flush_last_err : 0);

  if (state != NULL) {
    I2cBusLogState(&state->i2c_bus, reason_label);
  }
}

static void
RuntimeDumpLocks(runtime_state_t* state, const char* reason)
{
  if (state == NULL) {
    return;
  }
  const TickType_t now_ticks = xTaskGetTickCount();
  const char* fram_holder = (state->fram_log_mutex_holder != NULL)
                              ? state->fram_log_mutex_holder
                              : kMutexHolderNone;
  const char* i2c_holder = (state->i2c_mutex_holder != NULL)
                             ? state->i2c_mutex_holder
                             : kMutexHolderNone;
  const char* sd_holder = (state->sd_io_mutex_holder != NULL)
                            ? state->sd_io_mutex_holder
                            : kMutexHolderNone;
  const uint32_t fram_held_ms =
    (fram_holder != kMutexHolderNone)
      ? RuntimeElapsedMs(state->fram_log_mutex_hold_start_ticks, now_ticks)
      : 0u;
  const uint32_t i2c_held_ms =
    (i2c_holder != kMutexHolderNone)
      ? RuntimeElapsedMs(state->i2c_mutex_hold_start_ticks, now_ticks)
      : 0u;
  const uint32_t sd_held_ms =
    (sd_holder != kMutexHolderNone)
      ? RuntimeElapsedMs(state->sd_io_mutex_hold_start_ticks, now_ticks)
      : 0u;
  const char* phase =
    (state->sd_flush_phase != NULL) ? state->sd_flush_phase : kMutexHolderNone;
  const char* reason_label = (reason != NULL) ? reason : "unknown";

  ESP_LOGW(kTag, "Lock dump (%s):", reason_label);
  ESP_LOGW(kTag,
           "  fram_log holder=%s held_ms=%" PRIu32 " timeouts=%" PRIu32
           " max_ms=%" PRIu32,
           fram_holder,
           fram_held_ms,
           state->fram_log_mutex_timeouts,
           state->fram_log_mutex_hold_max_ms_observed);
  ESP_LOGW(kTag,
           "  i2c holder=%s held_ms=%" PRIu32 " timeouts=%" PRIu32
           " max_ms=%" PRIu32,
           i2c_holder,
           i2c_held_ms,
           state->i2c_mutex_timeouts,
           state->i2c_mutex_hold_max_ms_observed);
  ESP_LOGW(kTag,
           "  sd_io holder=%s held_ms=%" PRIu32 " timeouts=%" PRIu32
           " max_ms=%" PRIu32,
           sd_holder,
           sd_held_ms,
           state->sd_io_mutex_timeouts,
           state->sd_io_mutex_hold_max_ms_observed);
  ESP_LOGW(kTag,
           "  sd_flush phase=%s last_err=%s (%d) i2c_errs=%" PRIu32
           " sd_errs=%" PRIu32,
           phase,
           esp_err_to_name(state->sd_flush_last_err),
           (int)state->sd_flush_last_err,
           state->sd_flush_i2c_errs,
           state->sd_flush_sd_errs);

  if (state->error_ring_count > 0u) {
    const uint8_t count = state->error_ring_count;
    const uint8_t start =
      (uint8_t)((state->error_ring_head + RUNTIME_ERROR_RING_SIZE - count) %
                RUNTIME_ERROR_RING_SIZE);
    for (uint8_t i = 0; i < count; ++i) {
      const uint8_t idx = (uint8_t)((start + i) % RUNTIME_ERROR_RING_SIZE);
      const runtime_error_entry_t* entry = &state->error_ring[idx];
      const char* err_phase =
        (entry->phase != NULL) ? entry->phase : kMutexHolderNone;
      ESP_LOGW(kTag,
               "  err[%u] uptime_ms=%" PRIu32 " module=%s err=%s (%d) phase=%s",
               (unsigned)i,
               entry->uptime_ms,
               (entry->module != NULL) ? entry->module : "unknown",
               esp_err_to_name(entry->err),
               (int)entry->err,
               err_phase);
    }
  }
}

void
RuntimeDumpLocksManual(const char* reason)
{
  RuntimeDumpLocks(&g_state, reason);
}

/**
 * @brief Dump current I2C operation diagnostics to log output.
 * @param reason Reason string for the dump.
 */
void
RuntimeDumpI2cOpStateManual(const char* reason)
{
  RuntimeDumpI2cOpState(&g_state, reason);
}

static bool
IsRecoverableI2cErr(esp_err_t err)
{
  return err == ESP_ERR_TIMEOUT || err == ESP_FAIL ||
         err == ESP_ERR_INVALID_STATE || err == ESP_ERR_INVALID_RESPONSE;
}

static void
LogDrainPreflight(const runtime_state_t* state, const char* reason)
{
  if (state == NULL) {
    return;
  }

  StackMonitorMaybeSample(&g_stack_monitor);
  const runtime_cached_status_t* cached = &state->cached_status;
  const uint32_t fram_count = cached->fram_count;
  const uint32_t fram_capacity = cached->fram_capacity;
  const uint32_t watermark = cached->fram_flush_watermark_records;
  const uint32_t fram_pct =
    (fram_capacity > 0u) ? (fram_count * 100u) / fram_capacity : 0u;

  const char* reason_label = (reason != NULL) ? reason : "unknown";

  ESP_LOGI(kTag,
           "Drain preflight(%s): fram=%" PRIu32 "/%" PRIu32 " wm=%" PRIu32
           " (%" PRIu32 "%%) sd=mounted:%u degraded:%u backoff:%" PRIu32
           "ms heap=int:%" PRIu32 "/%" PRIu32 " psram:%" PRIu32 "/%" PRIu32
           " stack_min(ctrl:%" PRIu32 " stor:%" PRIu32 " flush:%" PRIu32
           " net:%" PRIu32 " http:%" PRIu32 ")",
           reason_label,
           fram_count,
           fram_capacity,
           watermark,
           fram_pct,
           cached->sd_mounted ? 1u : 0u,
           cached->sd_degraded ? 1u : 0u,
           cached->sd_backoff_remaining_ms,
           cached->heap_internal_free_bytes,
           cached->heap_internal_largest_free_block_bytes,
           cached->heap_psram_free_bytes,
           cached->heap_psram_largest_free_block_bytes,
           GetStackMonitorMinBytes("control"),
           GetStackMonitorMinBytes("storage"),
           GetStackMonitorMinBytes("sd_flush"),
           GetStackMonitorMinBytes("net_tx"),
           GetStackMonitorMinBytes("alert_http"));
}

static void
LogDrainPostflight(const runtime_state_t* state,
                   const char* reason,
                   int32_t flushed_records,
                   int32_t remaining_records,
                   uint32_t duration_ms)
{
  if (state == NULL) {
    return;
  }

  StackMonitorMaybeSample(&g_stack_monitor);
  ESP_LOGI(kTag,
           "Drain post(%s): flushed=%" PRIi32 " remaining=%" PRIi32
           " duration=%" PRIu32 "ms stack_min(ctrl:%" PRIu32 " stor:%" PRIu32
           " flush:%" PRIu32 " net:%" PRIu32 " http:%" PRIu32 ")",
           (reason != NULL) ? reason : "unknown",
           flushed_records,
           remaining_records,
           duration_ms,
           GetStackMonitorMinBytes("control"),
           GetStackMonitorMinBytes("storage"),
           GetStackMonitorMinBytes("sd_flush"),
           GetStackMonitorMinBytes("net_tx"),
           GetStackMonitorMinBytes("alert_http"));
}

static void
SdFlushTriggerFlagsToString(uint32_t trigger_flags,
                            char* buffer,
                            size_t buffer_len)
{
  if (buffer == NULL || buffer_len == 0u) {
    return;
  }

  buffer[0] = '\0';
  const struct
  {
    uint32_t flag;
    const char* label;
  } entries[] = {
    { SD_FLUSH_TRIGGER_WATERMARK, "watermark" },
    { SD_FLUSH_TRIGGER_PERIODIC, "periodic" },
    { SD_FLUSH_TRIGGER_BACKLOG, "backlog" },
    { SD_FLUSH_TRIGGER_RETRY, "retry" },
    { SD_FLUSH_TRIGGER_MORE_PENDING, "more_pending" },
    { SD_FLUSH_TRIGGER_MANUAL, "manual" },
  };

  size_t used = 0u;
  for (size_t i = 0; i < (sizeof(entries) / sizeof(entries[0])); ++i) {
    if ((trigger_flags & entries[i].flag) == 0u) {
      continue;
    }
    int written = snprintf(buffer + used,
                           buffer_len - used,
                           "%s%s",
                           (used > 0u) ? "+" : "",
                           entries[i].label);
    if (written < 0) {
      buffer[0] = '\0';
      return;
    }
    if ((size_t)written >= (buffer_len - used)) {
      used = buffer_len - 1u;
      break;
    }
    used += (size_t)written;
  }

  if (used == 0u) {
    (void)snprintf(buffer, buffer_len, "unknown");
  }
}

static void
SdFlushMaybeStartSession(runtime_state_t* state)
{
  if (state == NULL || state->sd_flush_quiesce_session_active) {
    return;
  }

  uint32_t trigger_flags = state->sd_flush_pending_trigger_flags;
  if (state->sd_start_drain_pending) {
    trigger_flags |= SD_FLUSH_TRIGGER_BACKLOG;
  }
  if (state->sd_manual_drain_active) {
    trigger_flags |= SD_FLUSH_TRIGGER_MANUAL;
  }
  if (trigger_flags == 0u) {
    trigger_flags = SD_FLUSH_TRIGGER_PERIODIC;
  }

  state->sd_flush_trigger_flags = trigger_flags;
  state->sd_flush_pending_trigger_flags = 0u;
  state->sd_flush_session_records_flushed = 0u;
  state->sd_flush_session_start_ticks = xTaskGetTickCount();
  state->sd_flush_session_id++;

  char trigger_string[64];
  SdFlushTriggerFlagsToString(
    state->sd_flush_trigger_flags, trigger_string, sizeof(trigger_string));
  (void)snprintf(state->sd_flush_session_label,
                 sizeof(state->sd_flush_session_label),
                 "sd_flush/%s#%" PRIu32,
                 trigger_string,
                 state->sd_flush_session_id);
  LogDrainPreflight(state, state->sd_flush_session_label);
}

static void
SdFlushLogSessionEnd(runtime_state_t* state,
                     uint32_t records_flushed,
                     uint32_t duration_ms)
{
  if (state == NULL) {
    return;
  }

  char session_label[RUNTIME_SD_FLUSH_SESSION_LABEL_LEN];
  const char* label = state->sd_flush_session_label;
  if (label == NULL || label[0] == '\0') {
    label = "sd_flush/unknown#0";
  }
  (void)snprintf(session_label, sizeof(session_label), "%s", label);

  uint32_t remaining = 0u;
  (void)ReadFramBufferedRecords(state, &remaining);
  LogDrainPostflight(state,
                     session_label,
                     (int32_t)records_flushed,
                     (int32_t)remaining,
                     duration_ms);

  state->sd_flush_trigger_flags = 0u;
  state->sd_flush_session_records_flushed = 0u;
  state->sd_flush_session_start_ticks = 0;
  state->sd_flush_session_label[0] = '\0';
}

static void
RuntimeNotifyAllRunTasks(runtime_state_t* state)
{
  if (state == NULL) {
    return;
  }
  RuntimeNotifyTask(state->sensor_task);
  RuntimeNotifyTask(state->storage_task);
  RuntimeNotifyTask(state->sd_flush_task);
  RuntimeNotifyTask(state->export_task);
  RuntimeNotifyTask(state->net_tx_task);
  RuntimeNotifyTask(state->alert_http_task);
  RuntimeNotifyTask(state->wifi_direct_task);
}

static bool
AlertManagerEligible(const runtime_state_t* state)
{
  if (state == NULL) {
    return false;
  }
  if (state->node_role_active == APP_NODE_ROLE_ROOT) {
    return true;
  }
  if (state->node_role_active != APP_NODE_ROLE_SENSOR) {
    return false;
  }
  if (state->net_mode_active != APP_NET_MODE_DIRECT_WIFI) {
    return false;
  }
  if (!WifiManagerIsConnected()) {
    return false;
  }
  return !MeshTransportIsConnected(&state->mesh);
}

static bool
AlertManagerSuppressed(const runtime_state_t* state)
{
  if (state == NULL) {
    return true;
  }
  if (state->node_role_active == APP_NODE_ROLE_ROOT) {
    return false;
  }
  if (state->node_role_active != APP_NODE_ROLE_SENSOR) {
    return true;
  }
  if (state->net_mode_active != APP_NET_MODE_DIRECT_WIFI) {
    return true;
  }
  return MeshTransportIsConnected(&state->mesh);
}

static bool
AlertManagerCanSend(const runtime_state_t* state)
{
  if (!AlertManagerEligible(state)) {
    return false;
  }
  if (state->node_role_active == APP_NODE_ROLE_ROOT) {
    return true;
  }
  return WifiManagerIsConnected();
}

/**
 * @brief Reset storage stall tracking baselines.
 * @param state Runtime state.
 * @param now_ms Current uptime in milliseconds.
 */
static void
RuntimeResetStorageStallTracking(runtime_state_t* state, int64_t now_ms)
{
  if (state == NULL) {
    return;
  }

  if (now_ms < 0) {
    now_ms = 0;
  }

  state->storage_stall_last_progress_ms = (uint32_t)now_ms;
  state->storage_stall_last_fram_count = state->cached_status.fram_count;
  state->storage_stall_last_sd_last_record_id =
    SdLoggerLastRecordIdOnSd(&state->sd_logger);
  state->storage_stall_last_sd_fail_count = state->cached_status.sd_fail_count;
  state->storage_stall_active = false;
}

/**
 * @brief Evaluate if storage drain appears stalled.
 * @param state Runtime state.
 * @param now_ms Current uptime in milliseconds.
 * @return True when stall condition is active.
 */
static bool
RuntimeComputeStorageStallCondition(runtime_state_t* state, int64_t now_ms)
{
  if (state == NULL || now_ms < 0) {
    return false;
  }

  const uint32_t now_ms_u32 = (uint32_t)now_ms;
  const uint32_t fram_count = state->cached_status.fram_count;
  const uint32_t watermark = state->cached_status.fram_flush_watermark_records;
  const uint64_t sd_last_record_id =
    SdLoggerLastRecordIdOnSd(&state->sd_logger);
  const uint32_t sd_fail_count = state->cached_status.sd_fail_count;

  const bool progress =
    (sd_last_record_id > state->storage_stall_last_sd_last_record_id) ||
    (fram_count < state->storage_stall_last_fram_count);
  if (progress) {
    state->storage_stall_last_progress_ms = now_ms_u32;
  }

  state->storage_stall_last_fram_count = fram_count;
  state->storage_stall_last_sd_last_record_id = sd_last_record_id;

  const bool fram_pressure = state->cached_status.fram_overrun_active ||
                             (watermark > 0u && fram_count >= watermark);
  const bool sd_issue =
    state->cached_status.sd_degraded ||
    (!state->cached_status.sd_mounted &&
     state->cached_status.sd_card_present) ||
    (state->cached_status.sd_backoff_remaining_ms > 0u) ||
    (sd_fail_count > state->storage_stall_last_sd_fail_count) ||
    state->cached_status.sd_io_error_active ||
    state->cached_status.sd_out_of_space_active;

  state->storage_stall_last_sd_fail_count = sd_fail_count;

  if (!state->cached_status.runtime_running || !fram_pressure || !sd_issue) {
    state->storage_stall_active = false;
    return false;
  }

  const uint32_t elapsed_ms =
    now_ms_u32 - state->storage_stall_last_progress_ms;
  state->storage_stall_active = elapsed_ms >= kStorageStallThresholdMs;
  return state->storage_stall_active;
}

static bool
RuntimeRebootAlertLatchValid(void)
{
  return g_reboot_alert_latch.magic == kRebootAlertLatchMagic &&
         (g_reboot_alert_latch.version == 1 ||
          g_reboot_alert_latch.version == kRebootAlertLatchVersion);
}

static void
RuntimeRebootAlertLatchUpgradeIfNeeded(void)
{
  if (g_reboot_alert_latch.magic != kRebootAlertLatchMagic ||
      g_reboot_alert_latch.version != 1) {
    return;
  }
  g_reboot_alert_latch.version = kRebootAlertLatchVersion;
  g_reboot_alert_latch.send_attempt_count = 0;
  g_reboot_alert_latch.last_attempt_epoch = 0;
  g_reboot_alert_latch.last_attempt_uptime_ms = 0;
  g_reboot_alert_latch.last_gate_reason = RUNTIME_REBOOT_ALERT_GATE_UNKNOWN;
  g_reboot_alert_latch.last_send_result = RUNTIME_REBOOT_ALERT_SEND_NONE;
  g_reboot_alert_latch.last_http_status = 0;
  g_reboot_alert_latch.last_ntfy_err = 0;
  g_reboot_alert_latch.last_retry_after_seconds = 0;
  g_reboot_alert_latch.sent_successfully = false;
}

static void
RuntimeRebootAlertLatchSet(alert_system_code_t code,
                           int64_t epoch,
                           uint32_t uptime_ms)
{
  g_reboot_alert_latch.magic = kRebootAlertLatchMagic;
  g_reboot_alert_latch.version = kRebootAlertLatchVersion;
  g_reboot_alert_latch.pending_is_active = true;
  g_reboot_alert_latch.pending_system_code = (uint32_t)code;
  g_reboot_alert_latch.pending_epoch = epoch;
  g_reboot_alert_latch.pending_uptime_ms = uptime_ms;
  g_reboot_alert_latch.send_attempt_count = 0;
  g_reboot_alert_latch.last_attempt_epoch = 0;
  g_reboot_alert_latch.last_attempt_uptime_ms = 0;
  g_reboot_alert_latch.last_gate_reason = RUNTIME_REBOOT_ALERT_GATE_UNKNOWN;
  g_reboot_alert_latch.last_send_result = RUNTIME_REBOOT_ALERT_SEND_NONE;
  g_reboot_alert_latch.last_http_status = 0;
  g_reboot_alert_latch.last_ntfy_err = 0;
  g_reboot_alert_latch.last_retry_after_seconds = 0;
  g_reboot_alert_latch.sent_successfully = false;
}

static void
RuntimeRebootAlertLatchClear(void)
{
  g_reboot_alert_latch.magic = kRebootAlertLatchMagic;
  g_reboot_alert_latch.version = kRebootAlertLatchVersion;
  g_reboot_alert_latch.pending_is_active = false;
  g_reboot_alert_latch.pending_system_code = 0;
  g_reboot_alert_latch.pending_epoch = 0;
  g_reboot_alert_latch.pending_uptime_ms = 0;
  g_reboot_alert_latch.send_attempt_count = 0;
  g_reboot_alert_latch.last_attempt_epoch = 0;
  g_reboot_alert_latch.last_attempt_uptime_ms = 0;
  g_reboot_alert_latch.last_gate_reason = RUNTIME_REBOOT_ALERT_GATE_UNKNOWN;
  g_reboot_alert_latch.last_send_result = RUNTIME_REBOOT_ALERT_SEND_NONE;
  g_reboot_alert_latch.last_http_status = 0;
  g_reboot_alert_latch.last_ntfy_err = 0;
  g_reboot_alert_latch.last_retry_after_seconds = 0;
  g_reboot_alert_latch.sent_successfully = false;
}

static void
RuntimeLoadRebootAlertLatch(runtime_state_t* state)
{
  if (state == NULL) {
    return;
  }
  state->reboot_alert_pending = false;
  state->reboot_alert_active_sent = false;
  state->reboot_alert_active_sent_ms = 0;
  state->reboot_alert_event_epoch = 0;
  state->reboot_alert_event_uptime_ms = 0;
  state->reboot_alert_code = ALERT_SYSTEM_CODE_NONE;
  state->reboot_alert_next_check_ms = 0;

  if (!RuntimeRebootAlertLatchValid()) {
    return;
  }
  RuntimeRebootAlertLatchUpgradeIfNeeded();
  if (!g_reboot_alert_latch.pending_is_active ||
      g_reboot_alert_latch.pending_system_code == 0) {
    return;
  }

  state->reboot_alert_pending = true;
  state->reboot_alert_code =
    (alert_system_code_t)g_reboot_alert_latch.pending_system_code;
  state->reboot_alert_event_epoch = g_reboot_alert_latch.pending_epoch;
  state->reboot_alert_event_uptime_ms = g_reboot_alert_latch.pending_uptime_ms;
}

static void
RuntimeRtcErrlogLatchInitIfNeeded(void)
{
  taskENTER_CRITICAL(&g_rtc_errlog_latch_lock);
  const bool needs_reset =
    g_rtc_errlog_latch.magic != kRtcErrlogLatchMagic ||
    g_rtc_errlog_latch.version != kRtcErrlogLatchVersion ||
    g_rtc_errlog_latch.count > RUNTIME_RTC_ERRLOG_RING_SIZE ||
    g_rtc_errlog_latch.head >= RUNTIME_RTC_ERRLOG_RING_SIZE;
  if (needs_reset) {
    memset(&g_rtc_errlog_latch, 0, sizeof(g_rtc_errlog_latch));
    g_rtc_errlog_latch.magic = kRtcErrlogLatchMagic;
    g_rtc_errlog_latch.version = kRtcErrlogLatchVersion;
  }
  taskEXIT_CRITICAL(&g_rtc_errlog_latch_lock);
}

static void
RuntimeRtcErrlogLatchPush(uint16_t code,
                          bool resolved,
                          int32_t detail0,
                          int32_t detail1,
                          uint32_t epoch_sec,
                          uint16_t millis)
{
  RuntimeRtcErrlogLatchInitIfNeeded();
  taskENTER_CRITICAL(&g_rtc_errlog_latch_lock);
  uint16_t write_index = 0;
  if (g_rtc_errlog_latch.count >= RUNTIME_RTC_ERRLOG_RING_SIZE) {
    write_index = g_rtc_errlog_latch.head;
    g_rtc_errlog_latch.head =
      (g_rtc_errlog_latch.head + 1u) % RUNTIME_RTC_ERRLOG_RING_SIZE;
    g_rtc_errlog_latch.count = RUNTIME_RTC_ERRLOG_RING_SIZE;
  } else {
    write_index = (g_rtc_errlog_latch.head + g_rtc_errlog_latch.count) %
                  RUNTIME_RTC_ERRLOG_RING_SIZE;
    g_rtc_errlog_latch.count++;
  }
  runtime_rtc_errlog_entry_t* entry = &g_rtc_errlog_latch.entries[write_index];
  entry->code = code;
  entry->resolved = resolved;
  entry->detail0 = detail0;
  entry->detail1 = detail1;
  entry->epoch_sec = epoch_sec;
  entry->millis = millis;
  taskEXIT_CRITICAL(&g_rtc_errlog_latch_lock);
}

static void
RuntimeRtcErrlogLatchFlushToFram(runtime_state_t* state)
{
  if (state == NULL || !state->fram_error_log.initialized) {
    return;
  }
  RuntimeRtcErrlogLatchInitIfNeeded();
  while (true) {
    runtime_rtc_errlog_entry_t entry = { 0 };
    uint16_t head_snapshot = 0;
    bool has_entry = false;
    taskENTER_CRITICAL(&g_rtc_errlog_latch_lock);
    if (g_rtc_errlog_latch.count > 0) {
      head_snapshot = g_rtc_errlog_latch.head;
      entry = g_rtc_errlog_latch.entries[head_snapshot];
      has_entry = true;
    }
    taskEXIT_CRITICAL(&g_rtc_errlog_latch_lock);
    if (!has_entry) {
      break;
    }
    bool logged = false;
    const esp_err_t result =
      entry.resolved ? FramErrorLogAppendResolved(&state->fram_error_log,
                                                  entry.code,
                                                  entry.detail0,
                                                  entry.detail1,
                                                  entry.epoch_sec,
                                                  entry.millis,
                                                  &logged)
                     : FramErrorLogAppendActive(&state->fram_error_log,
                                                entry.code,
                                                entry.detail0,
                                                entry.detail1,
                                                entry.epoch_sec,
                                                entry.millis,
                                                &logged);
    if (result != ESP_OK) {
      break;
    }
    taskENTER_CRITICAL(&g_rtc_errlog_latch_lock);
    if (g_rtc_errlog_latch.count > 0 &&
        g_rtc_errlog_latch.head == head_snapshot) {
      g_rtc_errlog_latch.head =
        (g_rtc_errlog_latch.head + 1u) % RUNTIME_RTC_ERRLOG_RING_SIZE;
      g_rtc_errlog_latch.count--;
    }
    taskEXIT_CRITICAL(&g_rtc_errlog_latch_lock);
  }
}

static const char*
RuntimeRebootAlertGateReasonToString(runtime_reboot_alert_gate_reason_t reason)
{
  switch (reason) {
    case RUNTIME_REBOOT_ALERT_GATE_NOT_CONFIGURED:
      return "not_configured";
    case RUNTIME_REBOOT_ALERT_GATE_DISABLED_BY_MASK:
      return "disabled_by_mask";
    case RUNTIME_REBOOT_ALERT_GATE_NOT_ELIGIBLE_NET_MODE:
      return "not_eligible_net_mode";
    case RUNTIME_REBOOT_ALERT_GATE_NOT_ELIGIBLE_ROLE:
      return "not_eligible_role";
    case RUNTIME_REBOOT_ALERT_GATE_WIFI_DISCONNECTED:
      return "wifi_disconnected";
    case RUNTIME_REBOOT_ALERT_GATE_MESH_CONNECTED_BLOCKING_DIRECT:
      return "mesh_connected";
    case RUNTIME_REBOOT_ALERT_GATE_COOLDOWN_ACTIVE:
      return "cooldown_active";
    case RUNTIME_REBOOT_ALERT_GATE_QUEUE_FULL:
      return "queue_full";
    case RUNTIME_REBOOT_ALERT_GATE_UNKNOWN:
    default:
      return "unknown";
  }
}

static runtime_reboot_alert_gate_reason_t
RuntimeRebootAlertGateReason(const runtime_state_t* state, int64_t now_ms)
{
  if (state == NULL) {
    return RUNTIME_REBOOT_ALERT_GATE_UNKNOWN;
  }
  if (!AlertManagerIsConfigured(&state->alert_manager)) {
    return RUNTIME_REBOOT_ALERT_GATE_NOT_CONFIGURED;
  }
  const uint32_t enable_mask = state->alert_manager.config.enable_mask;
  if ((enable_mask & (1u << ALERT_SYSTEM_ERROR)) == 0u) {
    return RUNTIME_REBOOT_ALERT_GATE_DISABLED_BY_MASK;
  }
  if (state->node_role_active != APP_NODE_ROLE_ROOT &&
      state->node_role_active != APP_NODE_ROLE_SENSOR) {
    return RUNTIME_REBOOT_ALERT_GATE_NOT_ELIGIBLE_ROLE;
  }
  if (state->node_role_active == APP_NODE_ROLE_SENSOR &&
      state->net_mode_active != APP_NET_MODE_DIRECT_WIFI) {
    return RUNTIME_REBOOT_ALERT_GATE_NOT_ELIGIBLE_NET_MODE;
  }
  if (!WifiManagerIsConnected()) {
    return RUNTIME_REBOOT_ALERT_GATE_WIFI_DISCONNECTED;
  }
  if (state->node_role_active == APP_NODE_ROLE_SENSOR &&
      MeshTransportIsConnected(&state->mesh)) {
    return RUNTIME_REBOOT_ALERT_GATE_MESH_CONNECTED_BLOCKING_DIRECT;
  }
  if (state->alert_manager.ntfy.cooldown_until_ms > now_ms) {
    return RUNTIME_REBOOT_ALERT_GATE_COOLDOWN_ACTIVE;
  }
  return RUNTIME_REBOOT_ALERT_GATE_UNKNOWN;
}

static void
RuntimeRebootAlertLatchRecordGate(runtime_reboot_alert_gate_reason_t reason)
{
  if (!RuntimeRebootAlertLatchValid()) {
    return;
  }
  RuntimeRebootAlertLatchUpgradeIfNeeded();
  if (!g_reboot_alert_latch.pending_is_active) {
    return;
  }
  g_reboot_alert_latch.last_gate_reason = (uint32_t)reason;
  g_reboot_alert_latch.last_send_result = RUNTIME_REBOOT_ALERT_SEND_SKIPPED;
}

static void
RuntimeRebootAlertLatchRecordAttempt(runtime_reboot_alert_send_result_t result,
                                     runtime_reboot_alert_gate_reason_t reason,
                                     int64_t attempt_epoch,
                                     uint32_t attempt_uptime_ms,
                                     int http_status,
                                     esp_err_t err,
                                     int retry_after_seconds)
{
  if (!RuntimeRebootAlertLatchValid()) {
    return;
  }
  RuntimeRebootAlertLatchUpgradeIfNeeded();
  if (!g_reboot_alert_latch.pending_is_active) {
    return;
  }
  g_reboot_alert_latch.send_attempt_count++;
  g_reboot_alert_latch.last_attempt_epoch = attempt_epoch;
  g_reboot_alert_latch.last_attempt_uptime_ms = attempt_uptime_ms;
  g_reboot_alert_latch.last_gate_reason = (uint32_t)reason;
  g_reboot_alert_latch.last_send_result = (uint32_t)result;
  g_reboot_alert_latch.last_http_status = (int32_t)http_status;
  g_reboot_alert_latch.last_ntfy_err = (int32_t)err;
  g_reboot_alert_latch.last_retry_after_seconds = (int32_t)retry_after_seconds;
  if (result == RUNTIME_REBOOT_ALERT_SEND_OK) {
    g_reboot_alert_latch.sent_successfully = true;
  }
}

static bool
RuntimeWaitForWifiConnected(uint32_t wait_ms)
{
  if (WifiManagerIsConnected()) {
    return true;
  }
  const int64_t start_ms = esp_timer_get_time() / 1000;
  while ((esp_timer_get_time() / 1000) - start_ms < (int64_t)wait_ms) {
    if (WifiManagerIsConnected()) {
      return true;
    }
    vTaskDelay(pdMS_TO_TICKS(100));
  }
  return WifiManagerIsConnected();
}

static bool
RuntimeEnqueueSystemErrorNote(runtime_state_t* state,
                              alert_system_code_t code,
                              bool resolved,
                              int64_t event_epoch,
                              int64_t event_uptime_ms)
{
  if (state == NULL || !AlertManagerIsConfigured(&state->alert_manager)) {
    return false;
  }
  if (state->alert_manager.ntfy.queue == NULL) {
    return false;
  }
  const uint32_t enable_mask = state->alert_manager.config.enable_mask;
  if ((enable_mask & (1u << ALERT_SYSTEM_ERROR)) == 0u) {
    return false;
  }

  alert_notification_t note = { 0 };
  note.type = ALERT_SYSTEM_ERROR;
  note.severity = ALERT_SEV_CRIT;
  note.resolved = resolved;
  note.leaf_id = state->local_leaf_id;
  note.payload.event_code = (uint32_t)code;
  note.payload.event_epoch = (event_epoch > 0) ? event_epoch : -1;
  note.payload.event_uptime_ms = event_uptime_ms;
  return AlertNtfyEnqueue(&state->alert_manager.ntfy, &note);
}

/**
 * @brief Enqueue an ntfy job and optionally wait for AlertHttpTask completion.
 * @param state Runtime state.
 * @param job Ntfy job to enqueue.
 * @param wait_ms Maximum time to wait for send counters to change.
 * @param status_out Optional pointer receiving last HTTP status.
 * @param err_out Optional pointer receiving last esp_err_t.
 * @param retry_after_seconds_out Optional pointer receiving cooldown-derived
 * retry seconds.
 * @return Result indicating enqueue/wait/send outcome.
 */
static alert_ntfy_result_t
RuntimeEnqueueNtfyJobAndWait(runtime_state_t* state,
                             const alert_ntfy_job_t* job,
                             uint32_t wait_ms,
                             int* status_out,
                             esp_err_t* err_out,
                             int* retry_after_seconds_out)
{
  if (status_out != NULL) {
    *status_out = 0;
  }
  if (err_out != NULL) {
    *err_out = ESP_OK;
  }
  if (retry_after_seconds_out != NULL) {
    *retry_after_seconds_out = -1;
  }
  if (state == NULL) {
    if (err_out != NULL) {
      *err_out = ESP_ERR_INVALID_ARG;
    }
    return ALERT_NTFY_FAILED;
  }
  if (state->alert_manager.ntfy.job_queue == NULL) {
    if (err_out != NULL) {
      *err_out = ESP_ERR_INVALID_STATE;
    }
    return ALERT_NTFY_SKIPPED;
  }

  const uint32_t success_before = state->alert_manager.ntfy.send_success;
  const uint32_t fail_before = state->alert_manager.ntfy.send_fail;
  if (job != NULL && !AlertNtfyEnqueueJob(&state->alert_manager.ntfy, job)) {
    if (err_out != NULL) {
      *err_out = ESP_FAIL;
    }
    return ALERT_NTFY_FAILED;
  }

  const int64_t start_ms = esp_timer_get_time() / 1000;
  while (!state->stop_requested) {
    const bool sent_ok =
      (state->alert_manager.ntfy.send_success != success_before);
    const bool sent_fail = (state->alert_manager.ntfy.send_fail != fail_before);
    if (sent_ok || sent_fail) {
      break;
    }
    const int64_t now_ms = esp_timer_get_time() / 1000;
    if ((uint32_t)(now_ms - start_ms) >= wait_ms) {
      break;
    }
    vTaskDelay(pdMS_TO_TICKS(25));
  }

  const int64_t now_ms = esp_timer_get_time() / 1000;
  if (status_out != NULL) {
    *status_out = state->alert_manager.ntfy.last_http_status;
  }
  if (err_out != NULL) {
    *err_out = state->alert_manager.ntfy.last_err;
  }
  if (retry_after_seconds_out != NULL) {
    *retry_after_seconds_out = -1;
    if (state->alert_manager.ntfy.cooldown_until_ms > now_ms) {
      *retry_after_seconds_out =
        (int)((state->alert_manager.ntfy.cooldown_until_ms - now_ms + 999) /
              1000);
    }
  }

  if (state->alert_manager.ntfy.send_success != success_before) {
    return ALERT_NTFY_OK;
  }
  if (state->alert_manager.ntfy.send_fail != fail_before) {
    return ALERT_NTFY_FAILED;
  }
  if (err_out != NULL && *err_out == ESP_OK) {
    *err_out = ESP_ERR_TIMEOUT;
  }
  return ALERT_NTFY_SKIPPED;
}

static alert_ntfy_result_t
RuntimeAttemptPreRebootAlertSendDetailed(runtime_state_t* state,
                                         alert_system_code_t code,
                                         int64_t event_epoch,
                                         int64_t event_uptime_ms,
                                         int* retry_after_seconds_out,
                                         int* status_out,
                                         esp_err_t* err_out)
{
  if (retry_after_seconds_out != NULL) {
    *retry_after_seconds_out = -1;
  }
  if (status_out != NULL) {
    *status_out = 0;
  }
  if (err_out != NULL) {
    *err_out = ESP_OK;
  }
  if (state == NULL) {
    if (err_out != NULL) {
      *err_out = ESP_ERR_INVALID_ARG;
    }
    return ALERT_NTFY_FAILED;
  }
  if (!AlertManagerIsConfigured(&state->alert_manager)) {
    if (err_out != NULL) {
      *err_out = ESP_ERR_INVALID_STATE;
    }
    return ALERT_NTFY_SKIPPED;
  }
  const uint32_t enable_mask = state->alert_manager.config.enable_mask;
  if ((enable_mask & (1u << ALERT_SYSTEM_ERROR)) == 0u) {
    if (err_out != NULL) {
      *err_out = ESP_ERR_INVALID_STATE;
    }
    return ALERT_NTFY_SKIPPED;
  }

  bool wifi_connected = WifiManagerIsConnected();
  if (!wifi_connected) {
    wifi_connected = RuntimeWaitForWifiConnected(kRebootAlertWifiWaitMs);
  }
  if (!wifi_connected) {
    if (err_out != NULL) {
      *err_out = ESP_ERR_TIMEOUT;
    }
    return ALERT_NTFY_SKIPPED;
  }

  const int64_t now_ms = esp_timer_get_time() / 1000;
  if (!RuntimeEnqueueSystemErrorNote(
        state, code, false, event_epoch, event_uptime_ms)) {
    if (err_out != NULL) {
      *err_out = ESP_FAIL;
    }
    return ALERT_NTFY_FAILED;
  }

  int64_t next_attempt_ms = now_ms;
  (void)AlertManagerPumpNtfy(&state->alert_manager, now_ms, &next_attempt_ms);

  return RuntimeEnqueueNtfyJobAndWait(state,
                                      NULL,
                                      kRebootAlertHttpTimeoutMs,
                                      status_out,
                                      err_out,
                                      retry_after_seconds_out);
}

esp_err_t
RuntimeManagerRunSafeHoldIfNeeded(runtime_state_t* state)
{
  if (state == NULL) {
    return ESP_ERR_INVALID_ARG;
  }
  if (!RuntimeRebootAlertLatchIsPending()) {
    return ESP_OK;
  }

  ESP_LOGW(kTag, "SAFE HOLD active: pending reboot alert latched");
  const int64_t start_ms = esp_timer_get_time() / 1000;
  uint32_t backoff_ms = kSafeHoldMinRetryMs;
  uint32_t last_log_ms = 0;

  while (RuntimeRebootAlertLatchIsPending()) {
    const int64_t now_ms = esp_timer_get_time() / 1000;
    if ((uint32_t)(now_ms - start_ms) >= kSafeHoldMaxMs) {
      ESP_LOGW(kTag, "SAFE HOLD timeout after %u ms", kSafeHoldMaxMs);
      return ESP_ERR_TIMEOUT;
    }

    runtime_reboot_alert_gate_reason_t gate_reason =
      RuntimeRebootAlertGateReason(state, now_ms);
    if (gate_reason != RUNTIME_REBOOT_ALERT_GATE_UNKNOWN) {
      RuntimeRebootAlertLatchRecordGate(gate_reason);
      if (LogRateLimitAllow(&last_log_ms, kSafeHoldLogIntervalMs)) {
        ESP_LOGI(kTag,
                 "SAFE HOLD waiting: gate=%s",
                 RuntimeRebootAlertGateReasonToString(gate_reason));
      }
      vTaskDelay(pdMS_TO_TICKS(backoff_ms));
      backoff_ms = (backoff_ms < kSafeHoldMaxRetryMs) ? (backoff_ms * 2)
                                                      : kSafeHoldMaxRetryMs;
      continue;
    }

    int64_t event_epoch = state->reboot_alert_event_epoch;
    uint32_t event_uptime_ms = state->reboot_alert_event_uptime_ms;
    if (event_uptime_ms == 0) {
      event_uptime_ms = (uint32_t)now_ms;
    }
    if (event_epoch <= 0 && TimeSyncIsSystemTimeValid()) {
      event_epoch = (int64_t)time(NULL);
    }

    int status = 0;
    int retry_after_seconds = -1;
    esp_err_t err = ESP_OK;
    alert_ntfy_result_t result =
      RuntimeAttemptPreRebootAlertSendDetailed(state,
                                               state->reboot_alert_code,
                                               event_epoch,
                                               event_uptime_ms,
                                               &retry_after_seconds,
                                               &status,
                                               &err);
    runtime_reboot_alert_send_result_t send_result =
      (result == ALERT_NTFY_OK)
        ? RUNTIME_REBOOT_ALERT_SEND_OK
        : (result == ALERT_NTFY_FAILED ? RUNTIME_REBOOT_ALERT_SEND_FAIL
                                       : RUNTIME_REBOOT_ALERT_SEND_SKIPPED);
    const int64_t attempt_epoch =
      TimeSyncIsSystemTimeValid() ? (int64_t)time(NULL) : -1;
    RuntimeRebootAlertLatchRecordAttempt(send_result,
                                         gate_reason,
                                         attempt_epoch,
                                         (uint32_t)now_ms,
                                         status,
                                         err,
                                         retry_after_seconds);

    if (result == ALERT_NTFY_OK) {
      state->reboot_alert_pending = false;
      state->reboot_alert_active_sent = true;
      state->reboot_alert_active_sent_ms = now_ms;
      state->reboot_alert_next_check_ms =
        now_ms + (int64_t)kRebootAlertResolveDelayMs;
      RuntimeRebootAlertLatchClear();
      ESP_LOGI(kTag, "SAFE HOLD alert sent");
      return ESP_OK;
    }

    if (LogRateLimitAllow(&last_log_ms, kSafeHoldLogIntervalMs)) {
      ESP_LOGW(kTag,
               "SAFE HOLD send failed: result=%d err=%s status=%d retry=%d",
               (int)result,
               esp_err_to_name(err),
               status,
               retry_after_seconds);
    }
    vTaskDelay(pdMS_TO_TICKS(backoff_ms));
    backoff_ms = (backoff_ms < kSafeHoldMaxRetryMs) ? (backoff_ms * 2)
                                                    : kSafeHoldMaxRetryMs;
  }

  return ESP_OK;
}

static uint32_t
RuntimeExpectedSpiPauseMask(runtime_state_t* state)
{
  if (state == NULL) {
    return 0;
  }
  uint32_t mask = 0;
  if (state->sensor_task != NULL) {
    mask |= SPI_PAUSE_ACK_SENSOR;
  }
  if (state->display_task != NULL) {
    mask |= SPI_PAUSE_ACK_DISPLAY;
  }
  return mask;
}

static bool
RuntimePauseSpiUsers(runtime_state_t* state, uint32_t timeout_ms)
{
  if (state == NULL) {
    return false;
  }

  const uint32_t expected_mask = RuntimeExpectedSpiPauseMask(state);
  if (expected_mask == 0) {
    return true;
  }

  state->spi_pause_requested = true;
  state->spi_pause_ack_mask = 0;
  RuntimeNotifyTask(state->display_task);
  RuntimeNotifyTask(state->sensor_task);

  const TickType_t wait_start = xTaskGetTickCount();
  while (((state->spi_pause_ack_mask & expected_mask) != expected_mask) &&
         (pdTICKS_TO_MS(xTaskGetTickCount() - wait_start) < timeout_ms)) {
    vTaskDelay(pdMS_TO_TICKS(10));
  }

  if ((state->spi_pause_ack_mask & expected_mask) != expected_mask) {
    ESP_LOGW(kTag,
             "SPI pause timed out; acked=0x%02" PRIx32 " expected=0x%02" PRIx32,
             state->spi_pause_ack_mask,
             expected_mask);
    return false;
  }
  return true;
}

static void
RuntimeResumeSpiUsers(runtime_state_t* state)
{
  if (state == NULL) {
    return;
  }
  state->spi_pause_requested = false;
  state->spi_pause_ack_mask = 0;
  RuntimeNotifyTask(state->display_task);
  RuntimeNotifyTask(state->sensor_task);
}

/**
 * @brief Request net_tx + alert_http pause state and wait for acknowledgements.
 * @param state Runtime state.
 * @param pause_enabled True to request pause, false to resume.
 * @param timeout_ms Maximum wait for acknowledgement.
 */
static void
RuntimeRequestNetPause(runtime_state_t* state,
                       bool pause_enabled,
                       uint32_t timeout_ms)
{
  if (state == NULL) {
    return;
  }

  state->net_tx_pause_requested = pause_enabled;
  state->alert_http_pause_requested = pause_enabled;
  RuntimeNotifyTask(state->net_tx_task);
  RuntimeNotifyTask(state->alert_http_task);

  const TickType_t wait_start = xTaskGetTickCount();
  while (pdTICKS_TO_MS(xTaskGetTickCount() - wait_start) < timeout_ms) {
    const bool net_ok =
      (state->net_tx_task == NULL) || (state->net_tx_paused == pause_enabled);
    const bool alert_ok = (state->alert_http_task == NULL) ||
                          (state->alert_http_paused == pause_enabled);
    if (net_ok && alert_ok) {
      return;
    }
    vTaskDelay(pdMS_TO_TICKS(10));
  }

  ESP_LOGW(kTag,
           "net pause timeout: requested=%d net_paused=%d alert_paused=%d",
           (int)pause_enabled,
           (int)state->net_tx_paused,
           (int)state->alert_http_paused);
}

static void
RuntimeInterruptibleDelayTicks(TickType_t delay_ticks)
{
  (void)ulTaskNotifyTake(pdTRUE, delay_ticks);
}

static bool
ManualDrainTimedOutTicks(TickType_t now_ticks, TickType_t deadline_ticks)
{
  if (deadline_ticks == 0) {
    return false;
  }
  return ((int32_t)(now_ticks - deadline_ticks) >= 0);
}

static void
RuntimeSyncFramFallbackCounters(runtime_state_t* state)
{
  if (state == NULL) {
    return;
  }
  const uint32_t next_sequence = FramLogNextSequence(&state->fram_log);
  const uint64_t next_record_id = FramLogNextRecordId(&state->fram_log);
  if (next_sequence != 0) {
    state->fram_fallback_sequence = next_sequence;
  }
  if (next_record_id != 0) {
    state->fram_fallback_record_id = next_record_id;
  }
}

static void
RuntimeSetFramUnavailable(runtime_state_t* state,
                          const char* context,
                          esp_err_t error,
                          int64_t now_ms)
{
  if (state == NULL) {
    return;
  }
  state->fram_available = false;
  state->fram_next_retry_ms = now_ms + kFramRetryIntervalMs;
  if (LogRateLimitAllow(&state->last_fram_retry_log_ms,
                        (uint32_t)kFramRetryIntervalMs)) {
    ESP_LOGW(kTag,
             "FRAM unavailable (%s): %s; retry in %u ms",
             (context != NULL) ? context : "init",
             esp_err_to_name(error),
             (unsigned)kFramRetryIntervalMs);
  }
  if (!state->cached_status.fram_io_error_active) {
    LogFramErrorEvent(state, ERROR_FRAM_IO_FAIL, false, (int32_t)error, 0);
    UpdateCachedBool(state, &state->cached_status.fram_io_error_active, true);
  }
  if (RuntimeFramLogLock(state, kFramLogLockTimeoutTicks)) {
    UpdateFramFillState(state);
    RuntimeFramLogUnlock(state);
  }
}

static bool
ReadFramBufferedRecords(runtime_state_t* state, uint32_t* buffered_out)
{
  if (buffered_out == NULL) {
    return false;
  }
  *buffered_out = 0;
  if (state == NULL) {
    return false;
  }
  if (!state->fram_available) {
    return true;
  }
  if (!RuntimeFramLogLock(state, kFramLogLockTimeoutTicks)) {
    return false;
  }
  *buffered_out = FramLogGetBufferedRecords(&state->fram_log);
  RuntimeFramLogUnlock(state);
  return true;
}

static esp_err_t
RuntimeAssignRecordIds(runtime_state_t* state, log_record_t* record)
{
  if (state == NULL || record == NULL) {
    return ESP_ERR_INVALID_ARG;
  }
  if (!state->fram_available) {
    if (state->fram_fallback_sequence == 0) {
      state->fram_fallback_sequence = 1;
    }
    if (state->fram_fallback_record_id == 0) {
      state->fram_fallback_record_id = 1;
    }
    record->sequence = state->fram_fallback_sequence++;
    record->record_id = state->fram_fallback_record_id++;
    record->schema_version = LOG_RECORD_SCHEMA_VER;
    return ESP_OK;
  }
  const esp_err_t result = FramLogAssignRecordIds(&state->fram_log, record);
  if (result == ESP_OK) {
    state->fram_fallback_sequence = record->sequence + 1u;
    state->fram_fallback_record_id = record->record_id + 1u;
  }
  return result;
}

/**
 * @brief Assign monotonic fallback record IDs without FRAM access.
 * @param state Runtime state.
 * @param record Record to update.
 */
static void
RuntimeAssignFallbackRecordIds(runtime_state_t* state, log_record_t* record)
{
  if (state == NULL || record == NULL) {
    return;
  }
  if (state->fram_fallback_sequence == 0u) {
    state->fram_fallback_sequence = 1u;
  }
  if (state->fram_fallback_record_id == 0u) {
    state->fram_fallback_record_id = 1u;
  }
  record->sequence = state->fram_fallback_sequence++;
  record->record_id = state->fram_fallback_record_id++;
  record->schema_version = LOG_RECORD_SCHEMA_VER;
}

static int32_t
ResolveStopDrainMaxMs(void)
{
  if (CONFIG_APP_STOP_DRAIN_MAX_MS < 0) {
    ESP_LOGW(kTag,
             "Stop drain max ms is unlimited; enforcing hard cap of %d ms",
             kStopDrainHardMaxDefaultMs);
    return kStopDrainHardMaxDefaultMs;
  }
  return CONFIG_APP_STOP_DRAIN_MAX_MS;
}

/**
 * @brief Execute UpdateCachedBool.
 * @param state Parameter state.
 * @param field Parameter field.
 * @param value Parameter value.
 */
static void
UpdateCachedBool(runtime_state_t* state, bool* field, bool value)
{
  if (state == NULL || field == NULL) {
    return;
  }
  if (*field == value) {
    return;
  }
  *field = value;
  RuntimeHealthMarkDirty(state);
}

/**
 * @brief Latch operator hold state for immediate display feedback.
 * @param state Runtime state.
 * @param now_ms Button/event uptime in milliseconds.
 */
static void
RuntimeLatchOperatorHold(runtime_state_t* state, uint32_t now_ms)
{
  if (state == NULL) {
    return;
  }

  (void)now_ms;
  UpdateCachedBool(state, &state->cached_status.operator_hold_latched, true);
}

/**
 * @brief Clear operator hold latch when returning to RUN mode.
 * @param state Runtime state.
 */
static void
RuntimeClearOperatorHold(runtime_state_t* state)
{
  if (state == NULL) {
    return;
  }

  UpdateCachedBool(state, &state->cached_status.operator_hold_latched, false);
}

/**
 * @brief Execute UpdateCachedUint32.
 * @param state Parameter state.
 * @param field Parameter field.
 * @param value Parameter value.
 */
static void
UpdateCachedUint32(runtime_state_t* state, uint32_t* field, uint32_t value)
{
  if (state == NULL || field == NULL) {
    return;
  }
  if (*field == value) {
    return;
  }
  *field = value;
  RuntimeHealthMarkDirty(state);
}

static void
UpdateCachedUint64(runtime_state_t* state, uint64_t* field, uint64_t value)
{
  if (state == NULL || field == NULL) {
    return;
  }
  if (*field == value) {
    return;
  }
  *field = value;
  RuntimeHealthMarkDirty(state);
}

static bool
DeferredLogPush(runtime_state_t* state, const log_record_t* record)
{
  if (state == NULL || record == NULL) {
    return false;
  }
  bool pushed = false;
  taskENTER_CRITICAL(&state->deferred_log.lock);
  if (state->deferred_log.count < DEFERRED_LOG_CAPACITY) {
    state->deferred_log.records[state->deferred_log.head] = *record;
    state->deferred_log.head =
      (uint8_t)((state->deferred_log.head + 1u) % DEFERRED_LOG_CAPACITY);
    state->deferred_log.count++;
    pushed = true;
  }
  taskEXIT_CRITICAL(&state->deferred_log.lock);
  return pushed;
}

static bool
DeferredLogPop(runtime_state_t* state, log_record_t* out)
{
  if (state == NULL || out == NULL) {
    return false;
  }
  bool popped = false;
  taskENTER_CRITICAL(&state->deferred_log.lock);
  if (state->deferred_log.count > 0u) {
    *out = state->deferred_log.records[state->deferred_log.tail];
    state->deferred_log.tail =
      (uint8_t)((state->deferred_log.tail + 1u) % DEFERRED_LOG_CAPACITY);
    state->deferred_log.count--;
    popped = true;
  }
  taskEXIT_CRITICAL(&state->deferred_log.lock);
  return popped;
}

static uint8_t
DeferredLogCount(runtime_state_t* state)
{
  if (state == NULL) {
    return 0;
  }
  uint8_t count = 0;
  taskENTER_CRITICAL(&state->deferred_log.lock);
  count = state->deferred_log.count;
  taskEXIT_CRITICAL(&state->deferred_log.lock);
  return count;
}

static uint32_t
DeferredLogDrops(runtime_state_t* state)
{
  if (state == NULL) {
    return 0;
  }
  uint32_t drops = 0;
  taskENTER_CRITICAL(&state->deferred_log.lock);
  drops = state->deferred_log.drops;
  taskEXIT_CRITICAL(&state->deferred_log.lock);
  return drops;
}

static void
DeferredLogReset(runtime_state_t* state)
{
  if (state == NULL) {
    return;
  }
  taskENTER_CRITICAL(&state->deferred_log.lock);
  state->deferred_log.head = 0;
  state->deferred_log.tail = 0;
  state->deferred_log.count = 0;
  state->deferred_log.drops = 0;
  taskEXIT_CRITICAL(&state->deferred_log.lock);
  UpdateCachedUint32(state, &state->cached_status.deferred_count, 0u);
  UpdateCachedUint32(state, &state->cached_status.deferred_drops, 0u);
  UpdateCachedBool(state, &state->cached_status.deferred_active, false);
}

static void
RuntimeBeginI2cQuiesce(runtime_state_t* state, const char* reason)
{
  if (state == NULL) {
    return;
  }

  if (state->i2c_quiesce_refcount > 0u) {
    state->i2c_quiesce_refcount++;
    state->i2c_quiesce_reason = (reason != NULL) ? reason : "unknown";
    return;
  }

  state->i2c_quiesce_active = true;
  state->i2c_quiesce_refcount = 1u;
  state->i2c_quiesce_enter_count++;
  state->i2c_quiesce_reason = (reason != NULL) ? reason : "unknown";
  UpdateCachedBool(state, &state->cached_status.i2c_quiesce_active, true);
  UpdateCachedUint32(
    state, &state->cached_status.deferred_count, DeferredLogCount(state));
  UpdateCachedUint32(
    state, &state->cached_status.deferred_drops, DeferredLogDrops(state));
  UpdateCachedBool(state,
                   &state->cached_status.deferred_active,
                   (DeferredLogCount(state) > 0u));
  if (strncmp(state->i2c_quiesce_reason, "sd_flush", 8) == 0) {
    char trigger_string[64];
    SdFlushTriggerFlagsToString(
      state->sd_flush_trigger_flags, trigger_string, sizeof(trigger_string));
    ESP_LOGI(kTag,
             "I2C quiesce begin (%s) sd_session_id=%" PRIu32
             " trigger=%s flags=0x%08" PRIx32
             " pending=%u start_drain=%u fram=%" PRIu32 " wm=%" PRIu32
             " deferred=%u drops=%u",
             state->i2c_quiesce_reason,
             state->sd_flush_session_id,
             trigger_string,
             state->sd_flush_trigger_flags,
             state->sd_flush_pending ? 1u : 0u,
             state->sd_start_drain_pending ? 1u : 0u,
             state->cached_status.fram_count,
             state->cached_status.fram_flush_watermark_records,
             (unsigned)state->cached_status.deferred_count,
             (unsigned)state->cached_status.deferred_drops);
  } else {
    ESP_LOGI(kTag,
             "I2C quiesce begin (%s) deferred=%u drops=%u",
             state->i2c_quiesce_reason,
             (unsigned)state->cached_status.deferred_count,
             (unsigned)state->cached_status.deferred_drops);
  }
}

static void
RuntimeEndI2cQuiesce(runtime_state_t* state)
{
  if (state == NULL || state->i2c_quiesce_refcount == 0u) {
    return;
  }

  state->i2c_quiesce_refcount--;
  if (state->i2c_quiesce_refcount > 0u) {
    return;
  }

  state->i2c_quiesce_active = false;
  state->i2c_quiesce_reason = NULL;
  UpdateCachedBool(state, &state->cached_status.i2c_quiesce_active, false);
  UpdateCachedUint32(
    state, &state->cached_status.deferred_count, DeferredLogCount(state));
  UpdateCachedUint32(
    state, &state->cached_status.deferred_drops, DeferredLogDrops(state));
  UpdateCachedBool(state,
                   &state->cached_status.deferred_active,
                   (DeferredLogCount(state) > 0u));
}

static esp_err_t
RuntimeDrainDeferredToFram(runtime_state_t* state, const char* context)
{
  if (state == NULL || !state->fram_available) {
    return ESP_OK;
  }
  log_record_t record;
  while (DeferredLogPop(state, &record)) {
    if (!RuntimeFramLogLockWithWarn(
          state,
          kFramLogLockTimeoutTicks,
          &state->fram_log_lock_timeout_count_sdflush,
          &state->last_fram_log_lock_timeout_sdflush_log_ms,
          context)) {
      (void)DeferredLogPush(state, &record);
      return ESP_ERR_TIMEOUT;
    }
    if (record.sequence == 0u || record.record_id == 0u) {
      const esp_err_t id_result = RuntimeAssignRecordIds(state, &record);
      if (id_result != ESP_OK) {
        RuntimeFramLogUnlock(state);
        (void)DeferredLogPush(state, &record);
        return id_result;
      }
    }
    const esp_err_t append_result = FramLogAppend(&state->fram_log, &record);
    RuntimeFramLogUnlock(state);
    if (append_result != ESP_OK) {
      (void)DeferredLogPush(state, &record);
      return append_result;
    }
    state->sd_flush_records_since++;
  }
  return ESP_OK;
}

static bool
SdCardPresent(const runtime_state_t* state)
{
  if (state == NULL) {
    return true;
  }
  return SdCardDetectIsPresent(&state->sd_card_detect);
}

/**
 * @brief Execute UpdateCachedInt32.
 * @param state Parameter state.
 * @param field Parameter field.
 * @param value Parameter value.
 */
static void
UpdateCachedInt32(runtime_state_t* state, int32_t* field, int32_t value)
{
  if (state == NULL || field == NULL) {
    return;
  }
  if (*field == value) {
    return;
  }
  *field = value;
  RuntimeHealthMarkDirty(state);
}

/**
 * @brief Execute RuntimeDiagHeapCheck.
 * @param state Parameter state.
 * @param context Parameter context.
 * @param force Parameter force.
 * @return Return the function result.
 */
bool
RuntimeDiagHeapCheck(runtime_state_t* state, const char* context, bool force)
{
  if (state == NULL) {
    return true;
  }
  if (!force && !state->diag_heap_check_enabled) {
    return true;
  }
  const bool ok = heap_caps_check_integrity_all(true);
  if (!ok) {
    ESP_LOGE(kTag,
             "HEAP integrity check failed: %s",
             (context != NULL) ? context : "unknown");
    if (!state->logger_running) {
      ESP_LOGE(kTag, "Diagnostics mode heap check failure; aborting");
      abort();
    }
  }
  return ok;
}

static void
MarkSdIoLockFailure(runtime_state_t* state)
{
  if (state == NULL) {
    return;
  }
  state->sd_degraded = true;
  state->sd_fail_count++;
  UpdateCachedBool(state, &state->cached_status.sd_degraded, true);
  UpdateCachedUint32(
    state, &state->cached_status.sd_fail_count, state->sd_fail_count);
  UpdateCachedBool(
    state, &state->cached_status.sd_mounted, state->sd_logger.is_mounted);
}

/**
 * @brief Execute RuntimeSdFsLock.
 * @param state Parameter state.
 * @param timeout_ticks Parameter timeout_ticks.
 * @return Return the function result.
 */
bool
RuntimeSdFsLock(runtime_state_t* state, TickType_t timeout_ticks)
{
  if (state == NULL) {
    return false;
  }
  if (state->sd_io_mutex == NULL) {
    ESP_LOGE(kTag, "SD I/O mutex unavailable; marking SD degraded");
    MarkSdIoLockFailure(state);
    return false;
  }
  if (xSemaphoreTake(state->sd_io_mutex, timeout_ticks) != pdTRUE) {
    const char* phase = (state->stop_requested || !state->logger_running)
                          ? "stop/diag"
                          : "runtime";
    state->sd_io_mutex_timeouts++;
    const TickType_t now_ticks = xTaskGetTickCount();
    const uint32_t held_ms =
      RuntimeElapsedMs(state->sd_io_mutex_hold_start_ticks, now_ticks);
    const char* holder = (state->sd_io_mutex_holder != NULL)
                           ? state->sd_io_mutex_holder
                           : kMutexHolderNone;
    const char* flush_phase = (state->sd_flush_phase != NULL)
                                ? state->sd_flush_phase
                                : kMutexHolderNone;
    ESP_LOGE(kTag,
             "SD I/O mutex timeout during %s; holder=%s held_ms=%" PRIu32
             " task=%s sd_phase=%s",
             phase,
             holder,
             held_ms,
             RuntimeGetCurrentTaskName(),
             flush_phase);
    const TickType_t dump_elapsed = now_ticks - state->last_lock_dump_ticks;
    if (state->last_lock_dump_ticks == 0 ||
        pdTICKS_TO_MS(dump_elapsed) >= kI2cLockDumpIntervalMs) {
      state->last_lock_dump_ticks = now_ticks;
      RuntimeDumpLocks(state, "sd_io_timeout");
    }
    MarkSdIoLockFailure(state);
    return false;
  }
  state->sd_io_mutex_holder = RuntimeGetCurrentTaskName();
  state->sd_io_mutex_hold_start_ticks = xTaskGetTickCount();
  return true;
}

/**
 * @brief Execute RuntimeSdFsUnlock.
 * @param state Parameter state.
 */
void
RuntimeSdFsUnlock(runtime_state_t* state)
{
  if (state == NULL || state->sd_io_mutex == NULL) {
    return;
  }
  const TickType_t now_ticks = xTaskGetTickCount();
  const uint32_t held_ms =
    RuntimeElapsedMs(state->sd_io_mutex_hold_start_ticks, now_ticks);
  RuntimeUpdateHoldMax(held_ms, &state->sd_io_mutex_hold_max_ms_observed);
  state->sd_io_mutex_holder = kMutexHolderNone;
  state->sd_io_mutex_hold_start_ticks = 0;
  (void)xSemaphoreGive(state->sd_io_mutex);
}

/**
 * @brief Execute RuntimeSdIoLock.
 * @param state Parameter state.
 * @param timeout_ticks Parameter timeout_ticks.
 * @return Return the function result.
 */
bool
RuntimeSdIoLock(runtime_state_t* state, TickType_t timeout_ticks)
{
  return RuntimeSdFsLock(state, timeout_ticks);
}

/**
 * @brief Execute RuntimeSdIoUnlock.
 * @param state Parameter state.
 */
void
RuntimeSdIoUnlock(runtime_state_t* state)
{
  RuntimeSdFsUnlock(state);
}

bool
RuntimeSpiBusLockForSharedDevices(runtime_state_t* state,
                                  TickType_t timeout_ticks)
{
  if (state == NULL) {
    return false;
  }
  if (state->spi_bus_mutex == NULL) {
    ESP_LOGE(kTag, "SPI bus mutex unavailable");
    return false;
  }
  if (xSemaphoreTake(state->spi_bus_mutex, timeout_ticks) != pdTRUE) {
    ESP_LOGW(kTag, "SPI bus mutex timeout");
    return false;
  }
  return true;
}

void
RuntimeSpiBusUnlockForSharedDevices(runtime_state_t* state)
{
  if (state == NULL || state->spi_bus_mutex == NULL) {
    return;
  }
  (void)xSemaphoreGive(state->spi_bus_mutex);
}

static bool
RuntimeSpiBusLock(void* context, TickType_t timeout_ticks)
{
  return RuntimeSpiBusLockForSharedDevices((runtime_state_t*)context,
                                           timeout_ticks);
}

static void
RuntimeSpiBusUnlock(void* context)
{
  RuntimeSpiBusUnlockForSharedDevices((runtime_state_t*)context);
}

static bool
RuntimeFramLogLock(runtime_state_t* state, TickType_t timeout_ticks)
{
  if (state == NULL) {
    return false;
  }
  if (state->fram_log_mutex == NULL) {
    ESP_LOGE(kTag, "FRAM log mutex unavailable");
    return false;
  }
  if (xSemaphoreTake(state->fram_log_mutex, timeout_ticks) != pdTRUE) {
    state->fram_log_mutex_timeouts++;
    const TickType_t now_ticks = xTaskGetTickCount();
    const uint32_t held_ms =
      RuntimeElapsedMs(state->fram_log_mutex_hold_start_ticks, now_ticks);
    const char* holder_name = (state->fram_log_mutex_holder != NULL)
                                ? state->fram_log_mutex_holder
                                : kMutexHolderNone;
    const char* flush_phase = (state->sd_flush_phase != NULL)
                                ? state->sd_flush_phase
                                : kMutexHolderNone;
    ESP_LOGW(kTag,
             "FRAM log mutex timeout (holder=%s held_ms=%" PRIu32
             " task=%s sd_phase=%s)",
             holder_name,
             held_ms,
             RuntimeGetCurrentTaskName(),
             flush_phase);
    const TickType_t dump_elapsed = now_ticks - state->last_lock_dump_ticks;
    if (state->last_lock_dump_ticks == 0 ||
        pdTICKS_TO_MS(dump_elapsed) >= kI2cLockDumpIntervalMs) {
      state->last_lock_dump_ticks = now_ticks;
      RuntimeDumpLocks(state, "fram_log_timeout");
    }
    return false;
  }
  state->fram_log_mutex_holder = RuntimeGetCurrentTaskName();
  state->fram_log_mutex_hold_start_ticks = xTaskGetTickCount();
  return true;
}

static void
RuntimeFramLogUnlock(runtime_state_t* state)
{
  if (state == NULL || state->fram_log_mutex == NULL) {
    return;
  }
  const TickType_t now_ticks = xTaskGetTickCount();
  const uint32_t held_ms =
    RuntimeElapsedMs(state->fram_log_mutex_hold_start_ticks, now_ticks);
  RuntimeUpdateHoldMax(held_ms, &state->fram_log_mutex_hold_max_ms_observed);
  state->fram_log_mutex_holder = kMutexHolderNone;
  state->fram_log_mutex_hold_start_ticks = 0;
  (void)xSemaphoreGive(state->fram_log_mutex);
}

/**
 * @brief Execute RuntimeI2cLock.
 * @param timeout_ticks Parameter timeout_ticks.
 * @return Return the function result.
 */
bool
RuntimeI2cLock(TickType_t timeout_ticks)
{
  if (g_state.i2c_mutex == NULL) {
    ESP_LOGE(kTag, "I2C mutex unavailable");
    return false;
  }

  const TaskHandle_t current_task = xTaskGetCurrentTaskHandle();
  if (g_state.i2c_mutex_owner_task != NULL &&
      g_state.i2c_mutex_owner_task == current_task) {
    g_state.i2c_mutex_same_task_reentry_count++;
    const TickType_t now_ticks = xTaskGetTickCount();
    const uint32_t held_ms =
      RuntimeElapsedMs(g_state.i2c_mutex_hold_start_ticks, now_ticks);
    const char* holder = (g_state.i2c_mutex_holder != NULL)
                           ? g_state.i2c_mutex_holder
                           : kMutexHolderNone;
    if (LogRateLimitAllow(&g_state.last_i2c_reentry_warn_ms,
                          kI2cTimeoutWarnIntervalMs)) {
      const uint32_t suppressed = g_state.i2c_mutex_reentry_suppressed_count;
      g_state.i2c_mutex_reentry_suppressed_count = 0;
      ESP_LOGW(kTag,
               "I2C mutex same-task reentry denied (holder=%s held_ms=%" PRIu32
               " task=%s reentry_count=%" PRIu32 " suppressed=%" PRIu32 ")",
               holder,
               held_ms,
               RuntimeGetCurrentTaskName(),
               g_state.i2c_mutex_same_task_reentry_count,
               suppressed);
    } else {
      g_state.i2c_mutex_reentry_suppressed_count++;
    }
    const TickType_t dump_elapsed =
      now_ticks - g_state.last_i2c_lock_dump_ticks;
    if (g_state.last_i2c_lock_dump_ticks == 0 ||
        pdTICKS_TO_MS(dump_elapsed) >= kI2cLockDumpIntervalMs) {
      g_state.last_i2c_lock_dump_ticks = now_ticks;
      RuntimeDumpLocks(&g_state, "i2c_same_task_reentry");
    }
    return false;
  }

  if (xSemaphoreTake(g_state.i2c_mutex, timeout_ticks) != pdTRUE) {
    g_state.i2c_mutex_timeouts++;
    const TickType_t now_ticks = xTaskGetTickCount();
    const uint32_t held_ms =
      RuntimeElapsedMs(g_state.i2c_mutex_hold_start_ticks, now_ticks);
    const char* holder = (g_state.i2c_mutex_holder != NULL)
                           ? g_state.i2c_mutex_holder
                           : kMutexHolderNone;
    const char* flush_phase = (g_state.sd_flush_phase != NULL)
                                ? g_state.sd_flush_phase
                                : kMutexHolderNone;
    if (LogRateLimitAllow(&g_state.last_i2c_timeout_warn_ms,
                          kI2cTimeoutWarnIntervalMs)) {
      const uint32_t suppressed = g_state.i2c_mutex_timeout_suppressed_count;
      g_state.i2c_mutex_timeout_suppressed_count = 0;
      ESP_LOGW(kTag,
               "I2C mutex timeout (holder=%s held_ms=%" PRIu32 " task=%s "
               "sd_phase=%s suppressed=%" PRIu32 ")",
               holder,
               held_ms,
               RuntimeGetCurrentTaskName(),
               flush_phase,
               suppressed);
    } else {
      g_state.i2c_mutex_timeout_suppressed_count++;
    }
    const TickType_t dump_elapsed =
      now_ticks - g_state.last_i2c_lock_dump_ticks;
    if (g_state.last_i2c_lock_dump_ticks == 0 ||
        pdTICKS_TO_MS(dump_elapsed) >= kI2cLockDumpIntervalMs) {
      g_state.last_i2c_lock_dump_ticks = now_ticks;
      RuntimeDumpLocks(&g_state, "i2c_timeout");
    }
    return false;
  }
  g_state.i2c_mutex_holder = RuntimeGetCurrentTaskName();
  g_state.i2c_mutex_owner_task = current_task;
  g_state.i2c_mutex_hold_start_ticks = xTaskGetTickCount();
  return true;
}

/**
 * @brief Execute RuntimeI2cUnlock.
 */
void
RuntimeI2cUnlock(void)
{
  if (g_state.i2c_mutex == NULL) {
    return;
  }
  const TickType_t now_ticks = xTaskGetTickCount();
  const uint32_t held_ms =
    RuntimeElapsedMs(g_state.i2c_mutex_hold_start_ticks, now_ticks);
  RuntimeUpdateHoldMax(held_ms, &g_state.i2c_mutex_hold_max_ms_observed);
  g_state.i2c_mutex_holder = kMutexHolderNone;
  g_state.i2c_mutex_owner_task = NULL;
  g_state.i2c_mutex_hold_start_ticks = 0;
  (void)xSemaphoreGive(g_state.i2c_mutex);
}

typedef struct
{
  log_record_t record;
  char node_id[32];
} export_item_t;

typedef struct
{
  char topic[128];
  char payload[256];
  uint16_t payload_len;
} broker_publish_item_t;

static StaticQueue_t g_export_outbox_queue_struct;
static StaticQueue_t g_broker_outbox_queue_struct;
static uint8_t* g_export_outbox_queue_storage = NULL;
static uint8_t* g_broker_outbox_queue_storage = NULL;
static uint8_t* g_export_outbox_pool_storage = NULL;
static uint8_t* g_broker_outbox_pool_storage = NULL;
static mem_pool_t g_export_outbox_pool;
static mem_pool_t g_broker_outbox_pool;

static StaticQueue_t g_export_queue_struct;
static uint8_t* g_export_queue_storage = NULL;

static void*
AllocatePreferPsram(size_t bytes)
{
  // Prefer PSRAM to preserve internal heap for Wi-Fi/COEX and internal-only
  // DMA.
  void* buffer = heap_caps_malloc(bytes, MALLOC_CAP_SPIRAM | MALLOC_CAP_8BIT);
  if (buffer != NULL) {
    return buffer;
  }
  return heap_caps_malloc(bytes, MALLOC_CAP_INTERNAL | MALLOC_CAP_8BIT);
}

static void
DrainExportOutboxQueue(runtime_state_t* state)
{
  if (state == NULL || state->export_outbox == NULL) {
    return;
  }

  export_record_item_t* item = NULL;
  while (xQueueReceive(state->export_outbox, &item, 0) == pdTRUE) {
    if (item != NULL) {
      MemPoolFree(&g_export_outbox_pool, item);
    }
  }
}

static void
DrainBrokerOutboxQueue(runtime_state_t* state)
{
  if (state == NULL || state->broker_outbox == NULL) {
    return;
  }

  broker_publish_item_t* item = NULL;
  while (xQueueReceive(state->broker_outbox, &item, 0) == pdTRUE) {
    if (item != NULL) {
      MemPoolFree(&g_broker_outbox_pool, item);
    }
  }
}

static const sd_csv_append_scratch_t*
BuildSdAppendScratch(const runtime_state_t* state,
                     sd_csv_append_scratch_t* scratch_out)
{
  if (state == NULL || scratch_out == NULL) {
    return NULL;
  }
  scratch_out->io_bounce_bytes = state->sd_logger.io_bounce_bytes;
  scratch_out->io_bounce_capacity = state->sd_logger.io_bounce_capacity;
  scratch_out->verify_readback_bytes = state->sd_logger.verify_readback_bytes;
  scratch_out->verify_readback_capacity =
    state->sd_logger.verify_readback_capacity;
  if (scratch_out->io_bounce_bytes == NULL &&
      scratch_out->verify_readback_bytes == NULL) {
    return NULL;
  }
  return scratch_out;
}
static esp_err_t
RuntimeFlushToSd(void* context);
static void
ClearSdIoError(runtime_state_t* state);
static esp_err_t
DrainFramToSd(runtime_state_t* state,
              bool unmount_on_exit,
              int32_t max_duration_ms,
              int32_t max_records_per_pass,
              int32_t yield_every_records,
              sd_drain_stats_t* out_stats);
static esp_err_t
DrainFramToSdOnStartBestEffort(runtime_state_t* state,
                               sd_drain_stats_t* out_stats);
static void
ControlTask(void* context);
static void
ControlTickTimeSync(runtime_state_t* state);
static void
ControlTickRtcResync(runtime_state_t* state);
static void
ControlTickTopology(runtime_state_t* state, int64_t now_ms);
static void
NetTxTask(void* context);

static void
EnsureSdMounted(void);
static void
EnsureSdMountedLocked(runtime_state_t* state);

static void
ReduceSdMaxFreqOnEio(runtime_state_t* state, int errno_value);

static void
MarkSdFailure(runtime_state_t* state,
              const char* context,
              const char* operation,
              esp_err_t error,
              int errno_value,
              bool did_unmount);

/**
 * @brief Execute SdMaintenanceTick.
 * @param state Parameter state.
 */
static void
SdMaintenanceTick(runtime_state_t* state)
{
  if (state == NULL || state->sd_logger.is_mounted) {
    return;
  }
  if (!SdCardPresent(state)) {
    return;
  }

  const TickType_t now_ticks = xTaskGetTickCount();
  if (state->sd_backoff_until_ticks != 0 &&
      now_ticks < state->sd_backoff_until_ticks) {
    return;
  }

  const bool was_degraded = state->sd_degraded;
  const uint32_t prev_fail_count = state->sd_fail_count;
  if (!RuntimeSdIoLock(state, kSdIoLockTimeoutTicks)) {
    return;
  }
  esp_err_t mount_result = SdLoggerTryRemount(&state->sd_logger, false);
  RuntimeSdIoUnlock(state);
  if (mount_result != ESP_OK) {
    MarkSdFailure(state, "SD mount failed", "mount", mount_result, 0, false);
    return;
  }

  state->sd_backoff_until_ticks = 0;
  state->sd_degraded = false;
  ClearSdIoError(state);
  UpdateCachedBool(
    state, &state->cached_status.sd_mounted, state->sd_logger.is_mounted);
  UpdateCachedBool(
    state, &state->cached_status.sd_degraded, state->sd_degraded);
  UpdateCachedUint32(
    state, &state->cached_status.sd_fail_count, state->sd_fail_count);
  UpdateCachedUint32(state, &state->cached_status.sd_backoff_remaining_ms, 0u);

  if (was_degraded || prev_fail_count != 0u) {
    ESP_LOGW(kTag,
             "SD recovered (mounted). fail_count=%u backoff cleared",
             (unsigned)state->sd_fail_count);
    HeapEventLog("sd_recovered", "mounted", 0);
  }

  if (RuntimeFramLogLock(state, kFramLogLockTimeoutTicks)) {
    if (FramLogGetBufferedRecords(&state->fram_log) > 0) {
      // We have backlog and SD is now available. Start draining immediately.
      state->sd_flush_pending = true;
      state->sd_start_drain_pending = true;
      state->sd_next_flush_allowed_ticks = 0;
    }
    RuntimeFramLogUnlock(state);
  }
}

/**
 * @brief Execute ConversionModeToString.
 * @param mode Parameter mode.
 * @return Return the function result.
 */
static const char*
ConversionModeToString(uint8_t mode)
{
  switch ((max31865_conversion_t)mode) {
    case kMax31865ConversionTablePt100:
      return "TABLE";
    case kMax31865ConversionCvdIterative:
      return "CVD";
    default:
      return "UNKNOWN";
  }
}

/**
 * @brief Execute BridgeModeUsesSerial.
 * @param mode Parameter mode.
 * @return Return the function result.
 */
static bool
BridgeModeUsesSerial(mqtt_bridge_mode_t mode)
{
  return mode == MQTT_BRIDGE_SERIAL || mode == MQTT_BRIDGE_BOTH;
}

/**
 * @brief Execute BridgeModeUsesBroker.
 * @param mode Parameter mode.
 * @return Return the function result.
 */
static bool
BridgeModeUsesBroker(mqtt_bridge_mode_t mode)
{
  return mode == MQTT_BRIDGE_BROKER || mode == MQTT_BRIDGE_BOTH;
}

/**
 * @brief Execute DoubleNear.
 * @param a Parameter a.
 * @param b Parameter b.
 * @return Return the function result.
 */
static bool
DoubleNear(double a, double b)
{
  return fabs(a - b) <= 1e-6;
}

/**
 * @brief Execute IsSdIoOperation.
 * @param operation Parameter operation.
 * @return Return the function result.
 */
static bool
IsSdIoOperation(const char* operation)
{
  if (operation == NULL) {
    return false;
  }
  return strcmp(operation, "append") == 0 || strcmp(operation, "fflush") == 0 ||
         strcmp(operation, "fsync") == 0 || strcmp(operation, "verify") == 0;
}

/**
 * @brief Execute ClearSdIoError.
 * @param state Parameter state.
 */
static void
ClearSdIoError(runtime_state_t* state)
{
  if (state == NULL) {
    return;
  }
  state->sd_io_success_streak++;
  state->sd_io_error_streak = 0;
  if (state->sd_last_io_error_active &&
      state->sd_io_success_streak < kSdIoErrorClearThreshold) {
    return;
  }
  state->sd_last_io_error_active = false;
  state->sd_last_io_err = ESP_OK;
  state->sd_last_errno = 0;
  UpdateCachedBool(state, &state->cached_status.sd_io_error_active, false);
}

static void
UpdateFramOverrunActive(runtime_state_t* state, uint64_t overrun_total)
{
  if (state == NULL) {
    return;
  }
  const bool overrun_active = (overrun_total > state->fram_overrun_ack_total);
  if (overrun_active) {
    state->fram_overrun_active_streak++;
    state->fram_overrun_clear_streak = 0;
  } else {
    state->fram_overrun_clear_streak++;
    state->fram_overrun_active_streak = 0;
  }
  const bool cached_active = state->cached_status.fram_overrun_active;
  if (!cached_active && overrun_active &&
      state->fram_overrun_active_streak >= kFramOverrunActiveSetThreshold) {
    UpdateCachedBool(state, &state->cached_status.fram_overrun_active, true);
  } else if (cached_active && !overrun_active &&
             state->fram_overrun_clear_streak >=
               kFramOverrunActiveClearThreshold) {
    UpdateCachedBool(state, &state->cached_status.fram_overrun_active, false);
  }
}

/**
 * @brief Execute UpdateFramFillState.
 * @param state Parameter state.
 * @note Caller must hold fram_log_mutex.
 */
static void
UpdateFramFillState(runtime_state_t* state)
{
  if (state == NULL) {
    return;
  }
  if (!state->fram_available) {
    state->fram_full = false;
    UpdateCachedUint32(state, &state->cached_status.fram_count, 0);
    UpdateCachedUint32(state, &state->cached_status.fram_capacity, 0);
    UpdateCachedBool(state, &state->cached_status.fram_full, false);
    return;
  }
  const size_t count = FramLogGetCountRecords(&state->fram_log);
  const size_t capacity = FramLogGetCapacityRecords(&state->fram_log);
  UpdateCachedUint32(state, &state->cached_status.fram_count, (uint32_t)count);
  UpdateCachedUint32(
    state, &state->cached_status.fram_capacity, (uint32_t)capacity);
  const bool fram_full = (capacity > 0 && count >= capacity);
  state->fram_full = fram_full;
  UpdateCachedBool(state, &state->cached_status.fram_full, fram_full);
}

/**
 * @brief Execute LogFramOverrunWarning.
 * @param state Parameter state.
 * @param overrun_total Parameter overrun_total.
 * @param fram_count Parameter fram_count.
 * @param fram_capacity Parameter fram_capacity.
 * @param now_ticks Parameter now_ticks.
 */
static void
LogFramOverrunWarning(runtime_state_t* state,
                      uint64_t overrun_total,
                      size_t fram_count,
                      size_t fram_capacity,
                      TickType_t now_ticks)
{
  if (state == NULL || overrun_total == 0) {
    return;
  }
  if (state->last_overrun_records_total == 0 && overrun_total > 0) {
    ESP_LOGW(
      kTag,
      "FRAM buffer full: overwriting oldest records (data loss possible until "
      "SD flush recovers).");
    state->last_overrun_log_ticks = now_ticks;
    state->last_overrun_logged_total = overrun_total;
    return;
  }

  const bool sd_down = (!state->sd_logger.is_mounted || state->sd_degraded);
  const bool overrun_advanced =
    (overrun_total > state->last_overrun_logged_total);
  if (!sd_down || !overrun_advanced) {
    return;
  }

  const uint32_t elapsed_ms =
    (uint32_t)pdTICKS_TO_MS(now_ticks - state->last_overrun_log_ticks);
  if (elapsed_ms < 30000u) {
    return;
  }

  ESP_LOGW(kTag,
           "FRAM overruns ongoing: total=%" PRIu64
           " buffered=%zu/%zu sd_mounted=%s sd_degraded=%s",
           overrun_total,
           fram_count,
           fram_capacity,
           state->sd_logger.is_mounted ? "yes" : "no",
           state->sd_degraded ? "yes" : "no");
  state->last_overrun_log_ticks = now_ticks;
  state->last_overrun_logged_total = overrun_total;
}

/**
 * @brief Execute CalibrationContextMatches.
 * @param settings Parameter settings.
 * @param current Parameter current.
 * @param reason_out Parameter reason_out.
 * @param reason_out_len Parameter reason_out_len.
 * @return Return the function result.
 */
static bool
CalibrationContextMatches(const app_settings_t* settings,
                          const calibration_context_t* current,
                          char* reason_out,
                          size_t reason_out_len)
{
  if (settings == NULL || current == NULL || reason_out == NULL) {
    return false;
  }
  if (!settings->calibration_context_valid) {
    snprintf(reason_out, reason_out_len, "calibration context missing");
    return false;
  }

  const calibration_context_t* stored = &settings->calibration_context;
  if (stored->conversion_mode != current->conversion_mode) {
    snprintf(reason_out,
             reason_out_len,
             "conversion mode changed (stored=%s current=%s)",
             ConversionModeToString(stored->conversion_mode),
             ConversionModeToString(current->conversion_mode));
    return false;
  }
  if (stored->wires != current->wires) {
    snprintf(reason_out,
             reason_out_len,
             "wire count changed (stored=%u current=%u)",
             (unsigned)stored->wires,
             (unsigned)current->wires);
    return false;
  }
  if (stored->filter_hz != current->filter_hz) {
    snprintf(reason_out,
             reason_out_len,
             "filter setting changed (stored=%uHz current=%uHz)",
             (unsigned)stored->filter_hz,
             (unsigned)current->filter_hz);
    return false;
  }
  if (!DoubleNear(stored->rref_ohm, current->rref_ohm)) {
    snprintf(reason_out,
             reason_out_len,
             "Rref changed (stored=%.6f current=%.6f)",
             stored->rref_ohm,
             current->rref_ohm);
    return false;
  }
  if (!DoubleNear(stored->r0_ohm, current->r0_ohm)) {
    snprintf(reason_out,
             reason_out_len,
             "R0 changed (stored=%.6f current=%.6f)",
             stored->r0_ohm,
             current->r0_ohm);
    return false;
  }
  if (stored->table_version != 0 && current->table_version != 0 &&
      stored->table_version != current->table_version) {
    snprintf(reason_out,
             reason_out_len,
             "PT100 table version changed (stored=%u current=%u)",
             (unsigned)stored->table_version,
             (unsigned)current->table_version);
    return false;
  }
  return true;
}

static void
CopyLastSample(runtime_state_t* state,
               int32_t* temp_milli_c,
               bool* valid,
               uint32_t* flags,
               TickType_t* update_ticks);

/**
 * @brief Execute ComputeActiveAttentionMaskFromHealth.
 * @param health Parameter health.
 * @return Return the function result.
 */
static display_attention_mask_t
ComputeActiveAttentionMaskFromHealth(const runtime_health_snapshot_t* health)
{
  if (health == NULL) {
    return 0;
  }

  display_attention_mask_t active = 0;
  const display_attention_mask_t mask = health->disp_attn_mask;

  if ((mask & kDispAttnSdOut) != 0u &&
      (!health->sd_card_present || !health->sd_mounted)) {
    active |= kDispAttnSdOut;
  }
  if ((mask & kDispAttnSdIo) != 0u && health->sd_io_error_active) {
    active |= kDispAttnSdIo;
  }
  if ((mask & kDispAttnFramOvr) != 0u && health->fram_overrun_active) {
    active |= kDispAttnFramOvr;
  }
  if ((mask & kDispAttnRtdFault) != 0u && health->sensor_fault_present) {
    active |= kDispAttnRtdFault;
  }
  if ((mask & kDispAttnTimeBad) != 0u && !health->time_valid) {
    active |= kDispAttnTimeBad;
  }
  if ((mask & kDispAttnNtpFail) != 0u && health->ntp_fail_alert_active) {
    active |= kDispAttnNtpFail;
  }
  if ((mask & kDispAttnMeshDown) != 0u && !health->mesh_connected) {
    active |= kDispAttnMeshDown;
  }
  if ((mask & kDispAttnHeap) != 0u &&
      (health->heap_internal_warn || health->heap_internal_crit)) {
    active |= kDispAttnHeap;
  }
  if ((mask & kDispAttnSdSpace) != 0u &&
      (health->sd_space_reclaim_active || health->sd_out_of_space_active)) {
    active |= kDispAttnSdSpace;
  }

  return active;
}

/**
 * @brief Execute AttentionBitToCode.
 * @param bit Parameter bit.
 * @return Return the function result.
 */
static const char*
AttentionBitToCode(display_attention_bit_t bit,
                   const runtime_health_snapshot_t* snapshot)
{
  switch (bit) {
    case kDispAttnSdOut:
      return "SDOUT";
    case kDispAttnSdIo:
      return "SDIO ";
    case kDispAttnFramOvr:
      return "FRAM ";
    case kDispAttnRtdFault:
      return "PROBE";
    case kDispAttnTimeBad:
      return "TIME ";
    case kDispAttnNtpFail:
      return "NTP  ";
    case kDispAttnMeshDown:
      return "MESH ";
    case kDispAttnHeap:
      return "HEAP ";
    case kDispAttnSdSpace:
      if (snapshot != NULL && snapshot->sd_out_of_space_active) {
        return "SDFUL";
      }
      return "SDROT";
    default:
      return "ERR  ";
  }
}

/**
 * @brief Execute CopyLastSample.
 * @param state Parameter state.
 * @param temp_milli_c Parameter temp_milli_c.
 * @param valid Parameter valid.
 * @param flags Parameter flags.
 * @param update_ticks Parameter update_ticks.
 */
static void
CopyLastSample(runtime_state_t* state,
               int32_t* temp_milli_c,
               bool* valid,
               uint32_t* flags,
               TickType_t* update_ticks)
{
  if (state == NULL) {
    return;
  }
  taskENTER_CRITICAL(&state->last_temp_lock);
  if (temp_milli_c != NULL) {
    *temp_milli_c = state->last_temp_milli_c;
  }
  if (valid != NULL) {
    *valid = state->last_temp_valid;
  }
  if (flags != NULL) {
    *flags = state->last_flags;
  }
  if (update_ticks != NULL) {
    *update_ticks = state->last_update_ticks;
  }
  taskEXIT_CRITICAL(&state->last_temp_lock);
}

/**
 * @brief Execute FormatTemperatureText.
 * @param out Parameter out.
 * @param out_len Parameter out_len.
 * @param temp_milli_c Parameter temp_milli_c.
 * @param units Parameter units.
 * @param valid Parameter valid.
 */
static void
FormatTemperatureText(char* out,
                      size_t out_len,
                      int32_t temp_milli_c,
                      app_display_units_t units,
                      bool valid)
{
  if (out == NULL || out_len == 0) {
    return;
  }
  out[0] = '\0';
  if (!valid) {
    snprintf(out, out_len, "----");
    return;
  }

  char unit_char = 'C';
  int64_t temp_milli = temp_milli_c;
  // Avoid float formatting in DisplayTask to prevent newlib heap use.
  if (units == APP_DISPLAY_UNITS_F) {
    const int64_t scaled = (int64_t)temp_milli_c * 9;
    const int64_t rounded = (scaled >= 0) ? (scaled + 2) / 5 : (scaled - 2) / 5;
    temp_milli = rounded + 32000;
    unit_char = 'F';
  }

  const int32_t tenths = (int32_t)((temp_milli >= 0) ? (temp_milli + 50) / 100
                                                     : (temp_milli - 50) / 100);
  const int32_t abs_tenths = (tenths < 0) ? -tenths : tenths;
  if (abs_tenths >= 10000) {
    snprintf(out, out_len, (tenths >= 0) ? "HI" : "LO");
    return;
  }

  if (abs_tenths >= 1000) {
    const int32_t whole = abs_tenths / 10;
    const int32_t frac = abs_tenths % 10;
    const char* sign = (tenths < 0) ? "-" : "";
    snprintf(
      out, out_len, "%s%ld.%01ld%c", sign, (long)whole, (long)frac, unit_char);
    return;
  }

  const int32_t whole = abs_tenths / 10;
  const int32_t frac = abs_tenths % 10;
  if (tenths < 0) {
    snprintf(out, out_len, "-%ld.%ld%c", (long)whole, (long)frac, unit_char);
  } else {
    snprintf(out, out_len, "%ld.%ld%c", (long)whole, (long)frac, unit_char);
  }
}

/**
 * @brief Execute UpdateTimeHealthState.
 * @param state Parameter state.
 * @param time_valid Parameter time_valid.
 */
static void
UpdateTimeHealthState(runtime_state_t* state, bool time_valid)
{
  if (state == NULL) {
    return;
  }
  UpdateCachedBool(state, &state->cached_status.time_valid, time_valid);
  const int64_t now_utc = time_valid ? (int64_t)time(NULL) : 0;
  UpdateCalibrationDueState(state, time_valid, now_utc);
  if (!time_valid) {
    UpdateCachedInt32(state, &state->cached_status.utc_offset_sec, 0);
    UpdateCachedBool(state, &state->cached_status.dst_in_effect, false);
    return;
  }

  const time_t now = (time_t)now_utc;
  struct tm utc_as_local;
  struct tm local_time;
  gmtime_r(&now, &utc_as_local);
  localtime_r(&now, &local_time);
  const time_t utc_epoch_as_local = mktime(&utc_as_local);
  const long utc_offset_sec = (long)difftime(now, utc_epoch_as_local);
  UpdateCachedInt32(
    state, &state->cached_status.utc_offset_sec, (int32_t)utc_offset_sec);
  UpdateCachedBool(
    state, &state->cached_status.dst_in_effect, (local_time.tm_isdst > 0));
}

static void
UpdateCalibrationDueState(runtime_state_t* state,
                          bool time_valid,
                          int64_t now_utc)
{
  if (state == NULL) {
    return;
  }

  if (time_valid) {
    if (!state->cal_time_stable) {
      if (state->cal_last_time_valid_utc == 0) {
        state->cal_last_time_valid_utc = now_utc;
      }
      if (now_utc - state->cal_last_time_valid_utc >= kCalTimeStableDelaySec) {
        state->cal_time_stable = true;
      }
    } else {
      state->cal_last_time_valid_utc = now_utc;
    }
  } else {
    state->cal_time_stable = false;
    state->cal_last_time_valid_utc = 0;
  }

  const bool cal_due_check_suspended = !time_valid;
  bool cal_overdue = false;
  if (time_valid) {
    const int64_t last_cal = (state->settings.cal_last_override_utc != 0)
                               ? state->settings.cal_last_override_utc
                               : state->settings.cal_last_utc;
    const uint16_t freq_count = (state->settings.cal_due_override_count != 0)
                                  ? state->settings.cal_due_override_count
                                  : state->settings.cal_due_count;
    const uint8_t freq_unit = (state->settings.cal_due_override_unit != 0)
                                ? state->settings.cal_due_override_unit
                                : state->settings.cal_due_unit;
    if (last_cal != 0 && freq_count != 0) {
      const int64_t due_utc =
        CalComputeDueDateUtc(last_cal, freq_count, (cal_due_unit_t)freq_unit);
      const int64_t today_midnight = GetUtcMidnightEpochNow();
      cal_overdue = (due_utc != 0 && today_midnight > due_utc);
    }
  }

  state->cal_due_check_suspended = cal_due_check_suspended;
  state->cal_overdue = cal_overdue;
  UpdateCachedBool(state,
                   &state->cached_status.cal_due_check_suspended,
                   cal_due_check_suspended);
  UpdateCachedBool(
    state, &state->cached_status.cal_overdue, state->cal_overdue);
  UpdateCachedBool(
    state, &state->cached_status.cal_time_stable, state->cal_time_stable);
}

/**
 * @brief Execute ComputeSdBackoffRemainingMs.
 * @param state Parameter state.
 * @param now_ticks Parameter now_ticks.
 * @return Return the function result.
 */
static uint32_t
ComputeSdBackoffRemainingMs(const runtime_state_t* state, TickType_t now_ticks)
{
  if (state == NULL || state->sd_backoff_until_ticks == 0 ||
      now_ticks >= state->sd_backoff_until_ticks) {
    return 0;
  }
  return (uint32_t)pdTICKS_TO_MS(state->sd_backoff_until_ticks - now_ticks);
}

/**
 * @brief Execute BuildDisplayTestText.
 * @param text Parameter text.
 * @param text_size Parameter text_size.
 * @param elapsed_ms Parameter elapsed_ms.
 */
static void
BuildDisplayTestText(char* text, size_t text_size, uint32_t elapsed_ms)
{
  if (text == NULL || text_size < 6u) {
    return;
  }

  const uint32_t step_ms = 250u;
  const char* banners[] = { "IDLE ", "STOP " };
  const size_t banner_steps = 4u;
  const char glyphs[] = "IDLESTOP ";
  const size_t glyph_count = sizeof(glyphs) - 1u;

  const size_t banner_total_steps =
    (sizeof(banners) / sizeof(banners[0])) * banner_steps;
  const size_t glyph_total_steps = glyph_count * 5u;
  const size_t total_steps = banner_total_steps + glyph_total_steps;

  size_t step = 0u;
  if (total_steps > 0u) {
    step = (elapsed_ms / step_ms) % total_steps;
  }

  if (step < banner_total_steps) {
    const size_t banner_index = step / banner_steps;
    snprintf(text, text_size, "%s", banners[banner_index]);
    return;
  }

  step -= banner_total_steps;
  const size_t glyph_index = step / 5u;
  const size_t position = step % 5u;
  memset(text, ' ', text_size);
  text[5] = '\0';
  if (glyph_index < glyph_count && position < 5u) {
    text[position] = glyphs[glyph_index];
  }
}
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
